linkejian123/Antique-Music-Box/CAD/ecc88/Renderings/ecc88_003.JPG

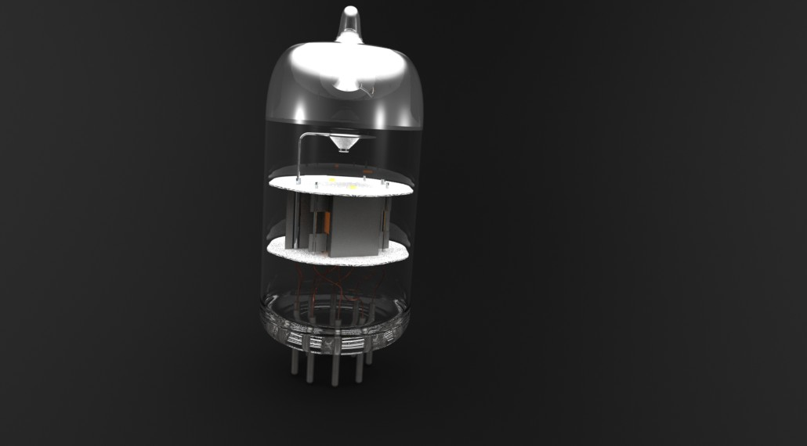
CAD/ecc88/Renderings/ecc88_003.JPG
