linkejian123/Antique-Music-Box/CAD/ecc88/Renderings/ECC88_in_Noval.JPG

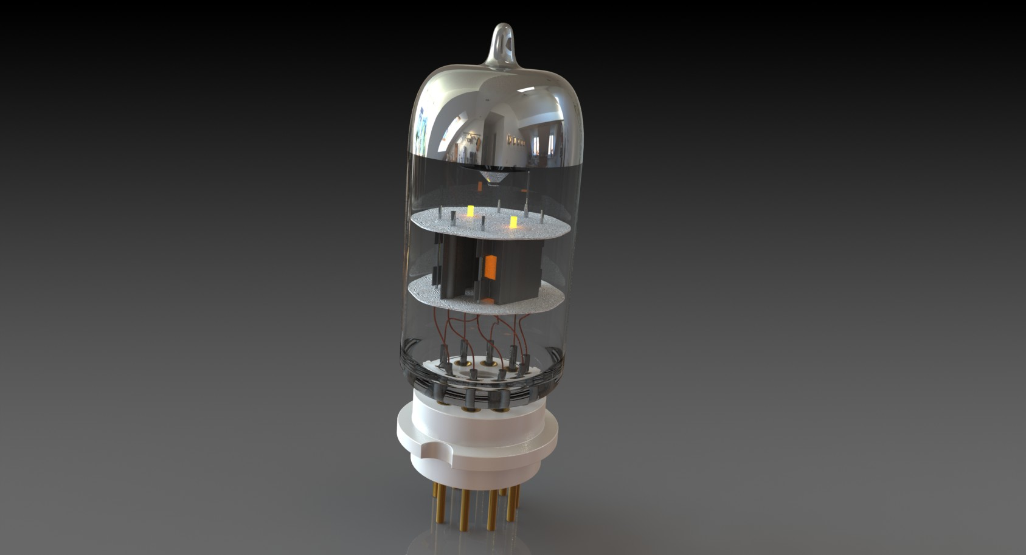
CAD/ecc88/Renderings/ECC88_in_Noval.JPG
