linkejian123/Antique-Music-Box/CAD/iv-17/render2.png

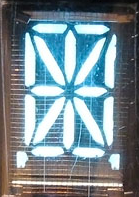
CAD/iv-17/render2.png
