linkejian123/Antique-Music-Box/CAD/iv-17/render.png

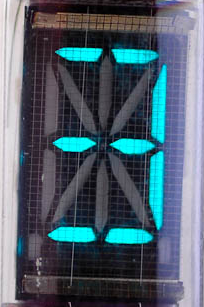
CAD/iv-17/render.png
