linkejian123/Antique-Music-Box/CAD/little-knob.snapshot.2/Renderings/2.jpg

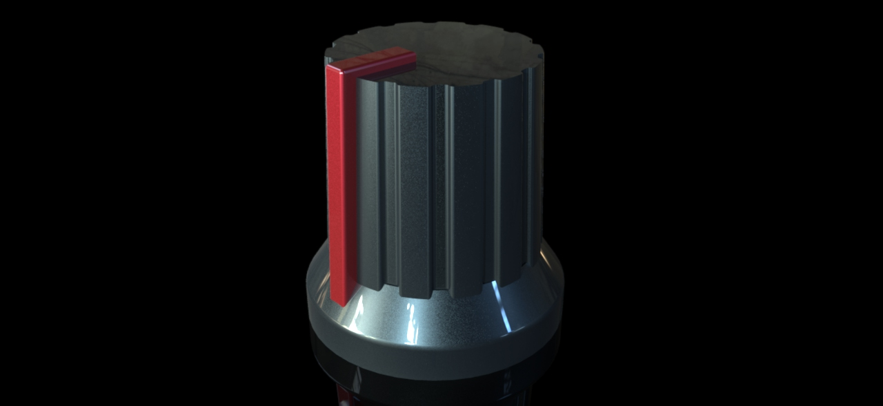
CAD/little-knob.snapshot.2/Renderings/2.jpg
