linkejian123/Antique-Music-Box/CAD/little-knob.snapshot.2/Renderings/345.JPG

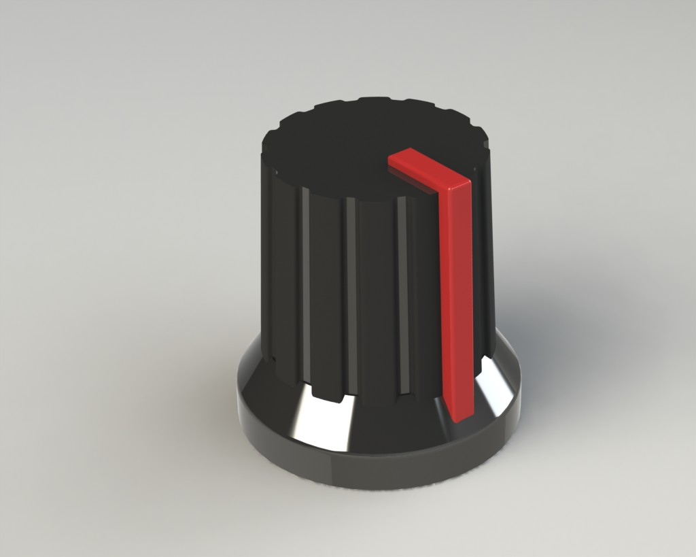
CAD/little-knob.snapshot.2/Renderings/345.JPG
