linkejian123/Antique-Music-Box/OBJ477/Gerbers/ap.JPG

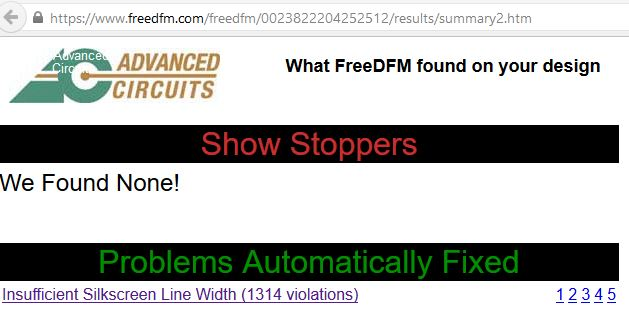
OBJ477/Gerbers/ap.JPG
