linkejian123/Antique-Music-Box/OBJ477/Gerbers/iv25.JPG

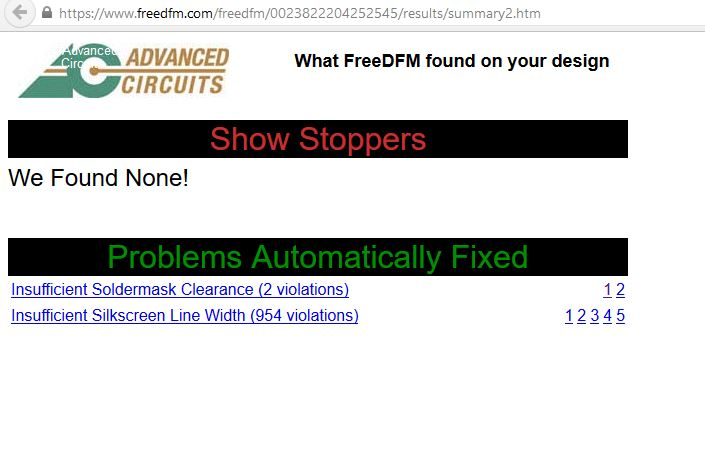
OBJ477/Gerbers/iv25.JPG
