linkejian123/Antique-Music-Box/CAD/little-knob.snapshot.2/myknob.IGS

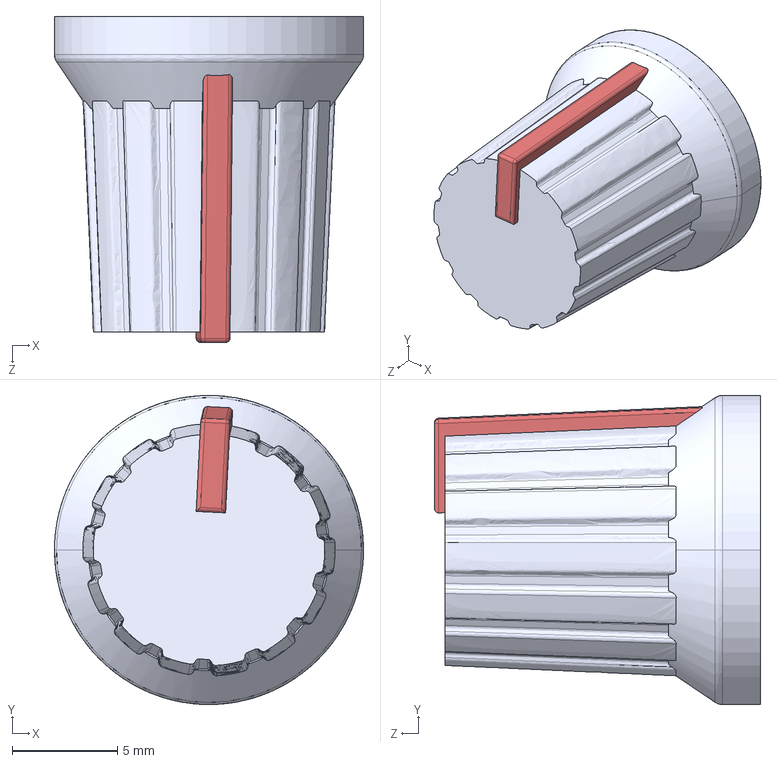
[picture p29: CAD file, 2017-10-23]
CAD/little-knob.snapshot.2/myknob.IGS
14.7 x 14.7 x 15.5 mm
