linkejian123/Antique-Music-Box/CAD/msc/12ax7/sheild.sldprt

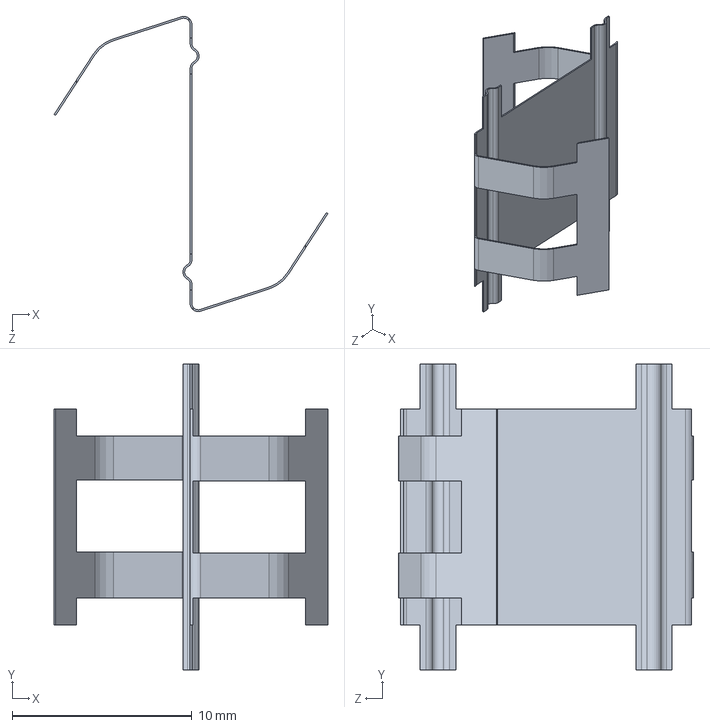
[picture p30: CAD file, 2017-10-23]
CAD/msc/12ax7/sheild.sldprt
15.2 x 17.0 x 16.4 mm
