linkejian123/Antique-Music-Box/CAD/msc/845/845 - cathode.SLDPRT

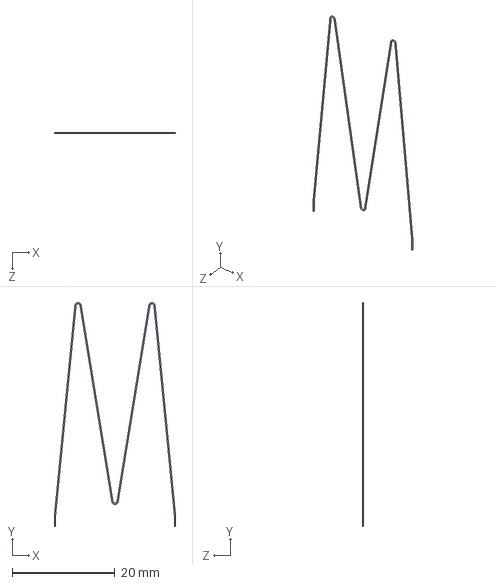
[picture p31: CAD file, 2017-10-23]
CAD/msc/845/845 - cathode.SLDPRT
23.6 x 43.6 x 0.25 mm
