linkejian123/Antique-Music-Box/CAD/ecc88/ecc88/ecc88_balon.SLDPRT

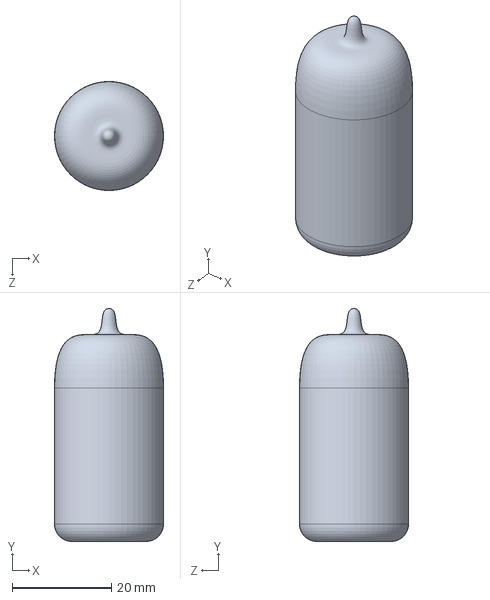
[picture p32: CAD file, 2017-10-23]
CAD/ecc88/ecc88/ecc88_balon.SLDPRT
22.0 x 47.0 x 22.0 mm
