linkejian123/Antique-Music-Box/CAD/el84  sub 6z4/el84 - spring thing.SLDPRT

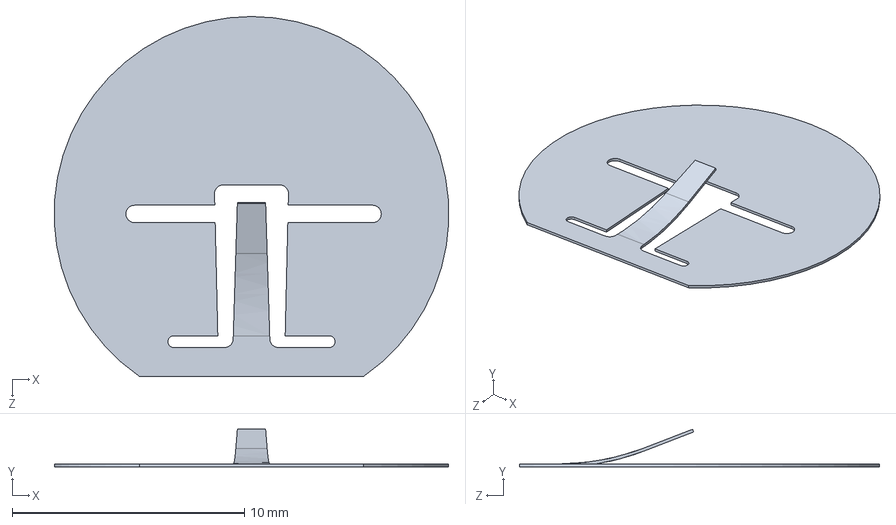
[picture p33: CAD file, 2017-10-23]
CAD/el84 sub 6z4/el84 - spring thing.SLDPRT
17.0 x 1.62 x 15.5 mm
