linkejian123/Antique-Music-Box/CAD/etd39-transformer-horizontal-1.snapshot.6/ETD39 Horizontal/7. Mounting bracket.SLDPRT

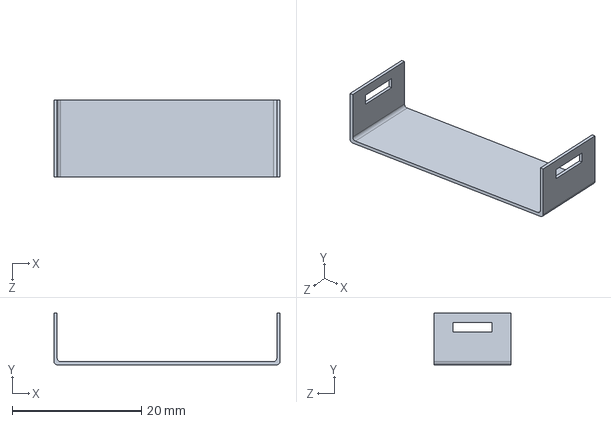
[picture p34: CAD file, 2017-10-23]
CAD/etd39-transformer-horizontal-1.snapshot.6/ETD39 Horizontal/7. Mounting bracket.SLDPRT
35.0 x 8.00 x 12.0 mm
