linkejian123/Antique-Music-Box/CAD/iv-17/tube_leads.SLDPRT

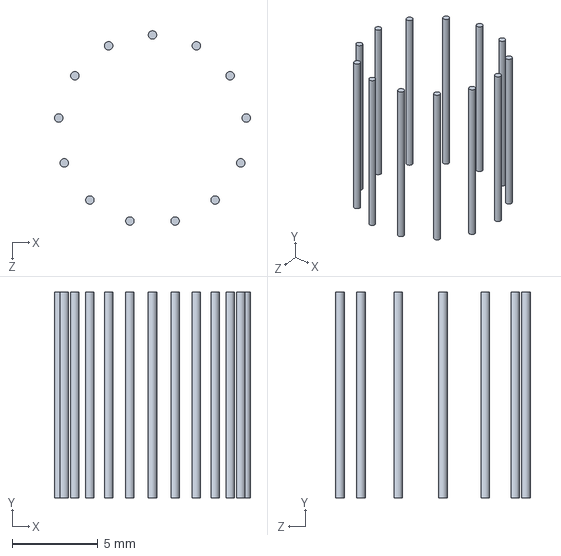
[picture p35: CAD file, 2017-10-23]
CAD/iv-17/tube_leads.SLDPRT
11.4 x 12.0 x 11.3 mm
