linkejian123/Antique-Music-Box/CAD/iv-25/insole.SLDPRT

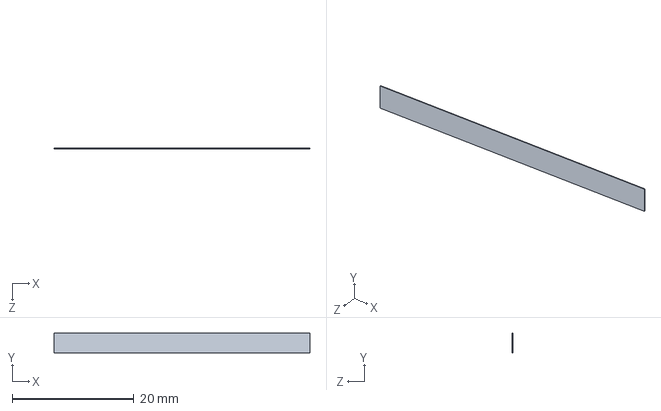
[picture p36: CAD file, 2017-10-23]
CAD/iv-25/insole.SLDPRT
42.0 x 3.20 x 0.1 mm
