linkejian123/Antique-Music-Box/CAD/msc/12ax7/cathode_end.sldprt

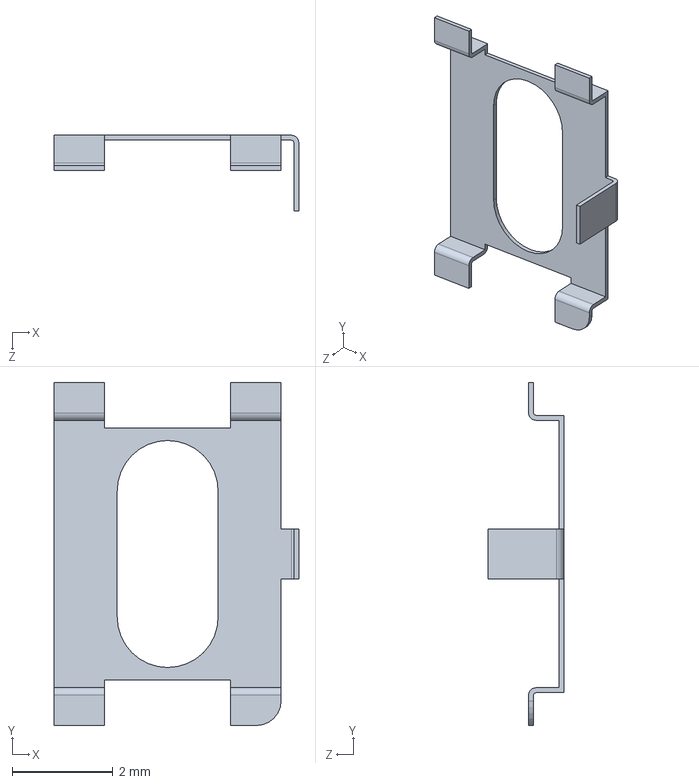
[picture p37: CAD file, 2017-10-23]
CAD/msc/12ax7/cathode_end.sldprt
4.85 x 6.80 x 1.50 mm
