linkejian123/Antique-Music-Box/CAD/ecc88/ecc88/ecc88_insulator.SLDPRT

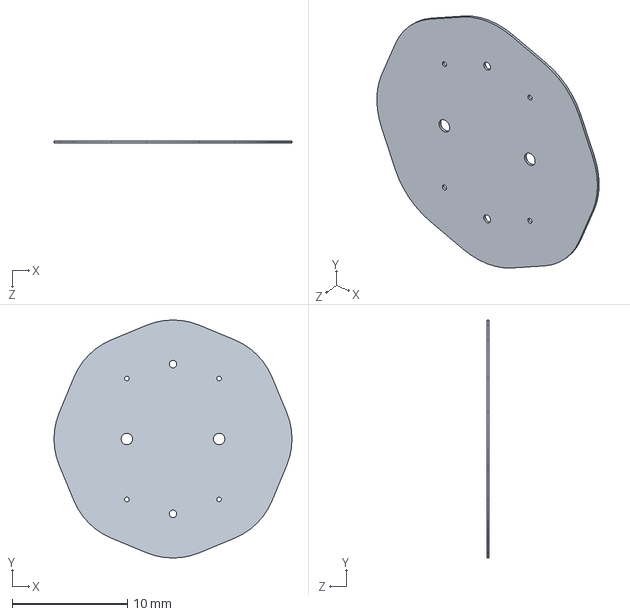
[picture p39: CAD file, 2017-10-23]
CAD/ecc88/ecc88/ecc88_insulator.SLDPRT
20.7 x 20.7 x 0.2 mm
