linkejian123/Antique-Music-Box/CAD/el84  sub 6z4/screen connector.SLDPRT

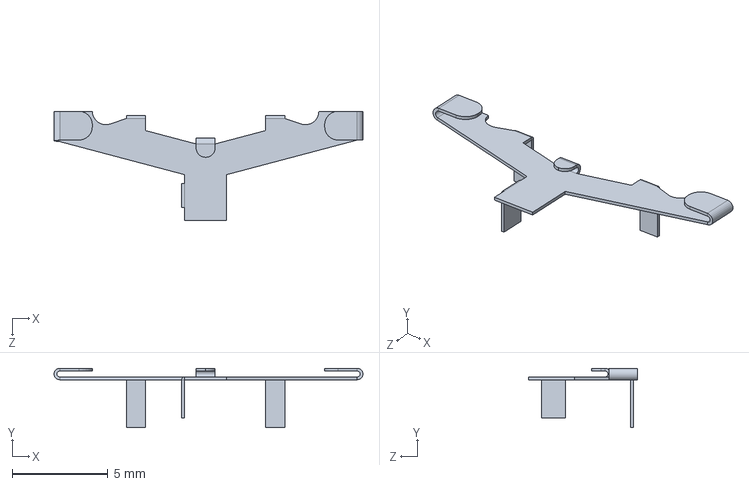
[picture p40: CAD file, 2017-10-23]
CAD/el84 sub 6z4/screen connector.SLDPRT
16.1 x 3.10 x 5.70 mm
