linkejian123/Antique-Music-Box/CAD/em84/tube_body2.SLDPRT

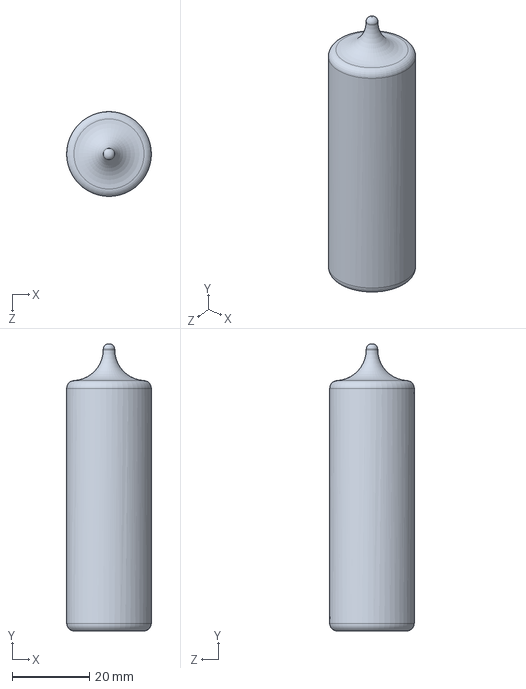
[picture p41: CAD file, 2017-10-23]
CAD/em84/tube_body2.SLDPRT
22.0 x 74.5 x 22.0 mm
