linkejian123/Antique-Music-Box/CAD/iv-25/iv-25.SLDPRT

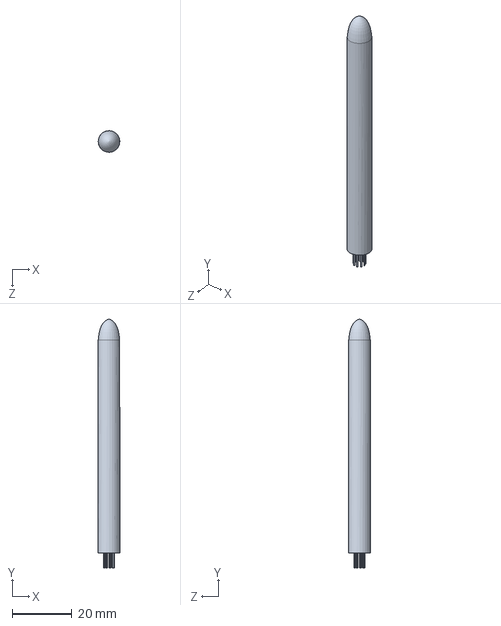
[picture p42: CAD file, 2017-10-23]
CAD/iv-25/iv-25.SLDPRT
7.20 x 83.0 x 7.20 mm
