linkejian123/Antique-Music-Box/CAD/msc/12ax7/grid wire.sldprt

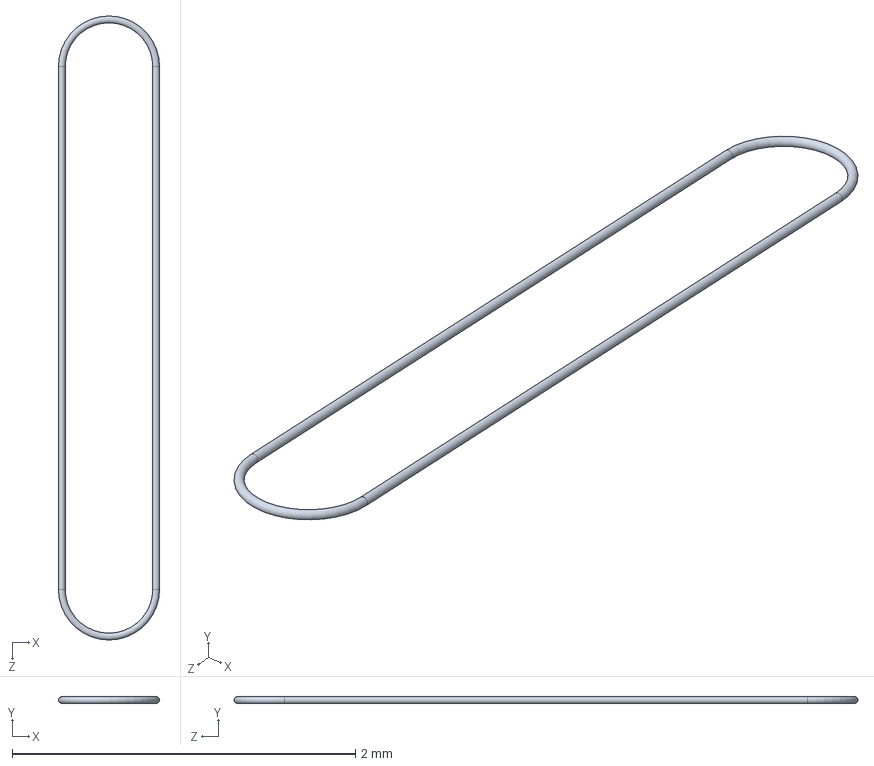
[picture p43: CAD file, 2017-10-23]
CAD/msc/12ax7/grid wire.sldprt
0.59 x 0.04 x 3.64 mm
