linkejian123/Antique-Music-Box/CAD/msc/845/845 - heater long lead.SLDPRT

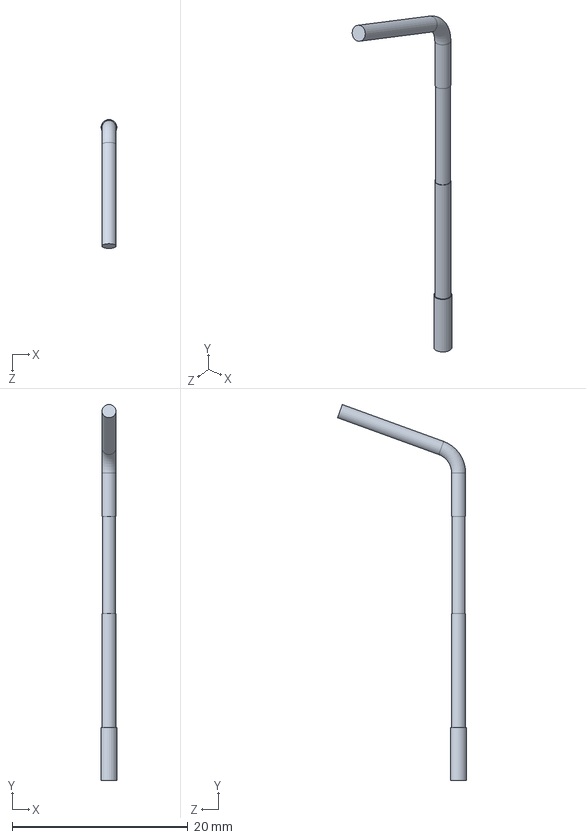
[picture p44: CAD file, 2017-10-23]
CAD/msc/845/845 - heater long lead.SLDPRT
1.80 x 42.8 x 14.7 mm
