linkejian123/Antique-Music-Box/CAD/el84  sub 6z4/el84 lower mica.SLDPRT

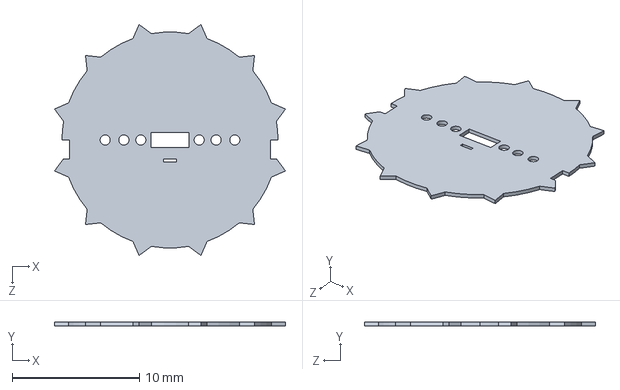
[picture p45: CAD file, 2017-10-23]
CAD/el84 sub 6z4/el84 lower mica.SLDPRT
18.2 x 0.3 x 18.2 mm
