linkejian123/Antique-Music-Box/CAD/etd39-transformer-horizontal-1.snapshot.6/ETD39 Horizontal/3. Case (Pin end)1.SLDPRT

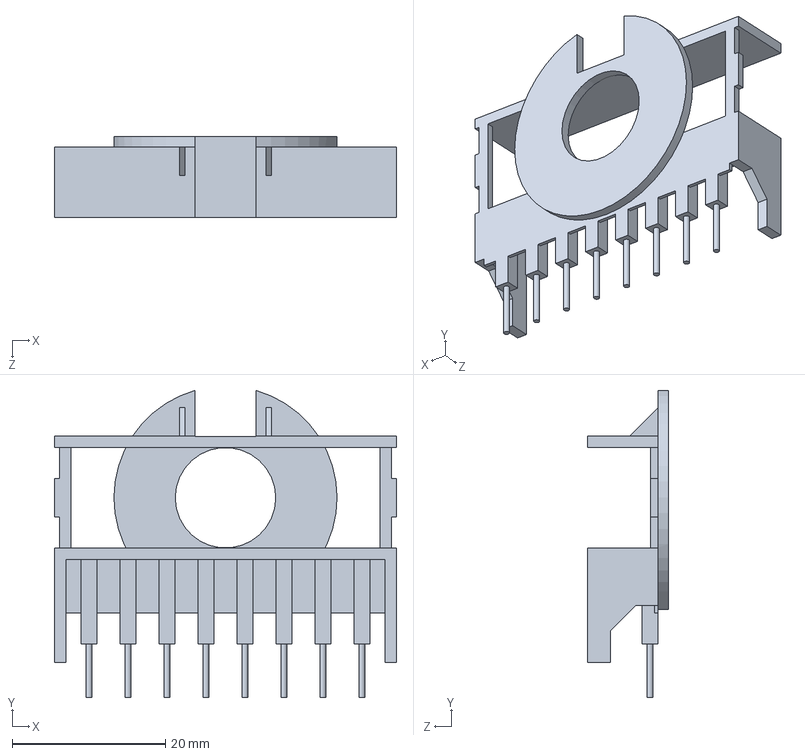
[picture p46: CAD file, 2017-10-23]
CAD/etd39-transformer-horizontal-1.snapshot.6/ETD39 Horizontal/3. Case (Pin end)1.SLDPRT
44.6 x 40.0 x 10.6 mm
