linkejian123/Antique-Music-Box/CAD/iv-17/flip.SLDPRT

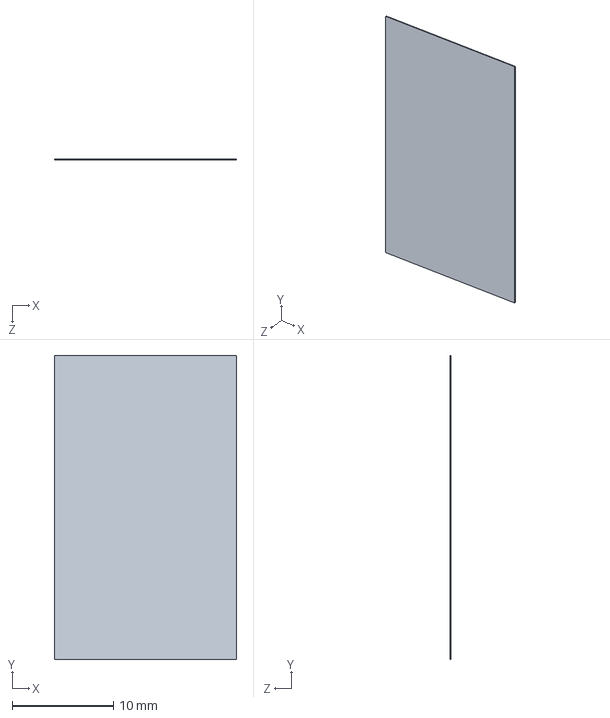
[picture p47: CAD file, 2017-10-23]
CAD/iv-17/flip.SLDPRT
18.0 x 30.0 x 0.1 mm
