linkejian123/Antique-Music-Box/CAD/msc/845/845 - inner heater to pin.SLDPRT

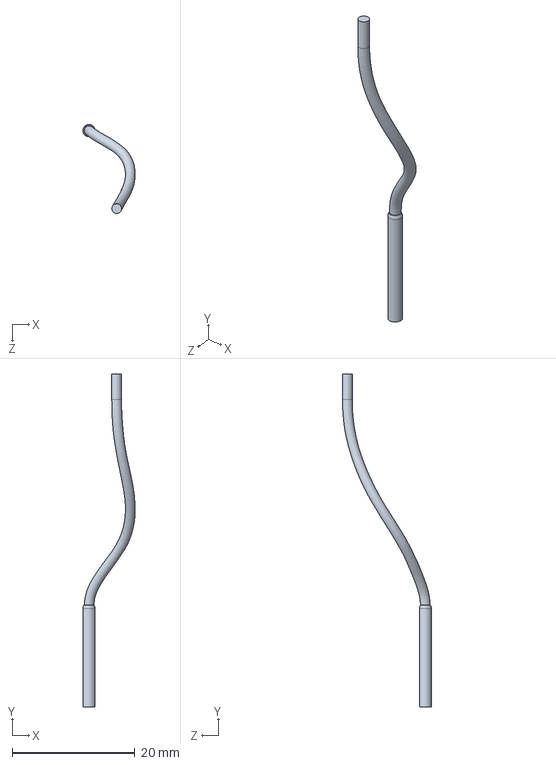
[picture p48: CAD file, 2017-10-23]
CAD/msc/845/845 - inner heater to pin.SLDPRT
8.51 x 54.2 x 14.5 mm
