linkejian123/Antique-Music-Box/CAD/ecc88/ecc88/ecc88_heater.SLDPRT

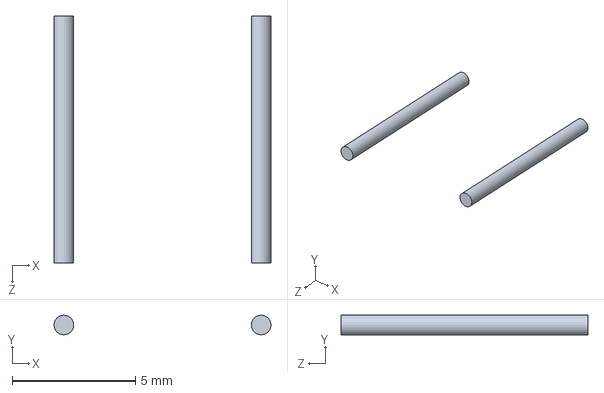
[picture p49: CAD file, 2017-10-23]
CAD/ecc88/ecc88/ecc88_heater.SLDPRT
8.80 x 0.8 x 10.0 mm
