linkejian123/Antique-Music-Box/CAD/el84  sub 6z4/el84 plate.SLDPRT

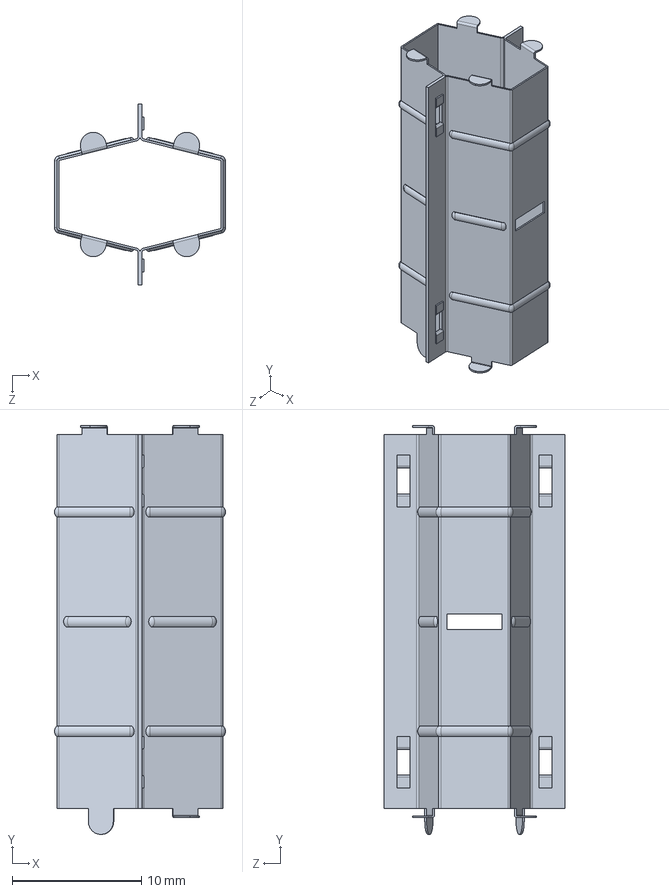
[picture p50: CAD file, 2017-10-23]
CAD/el84 sub 6z4/el84 plate.SLDPRT
13.3 x 31.7 x 14.0 mm
