linkejian123/Antique-Music-Box/CAD/em84/tiepian.SLDPRT

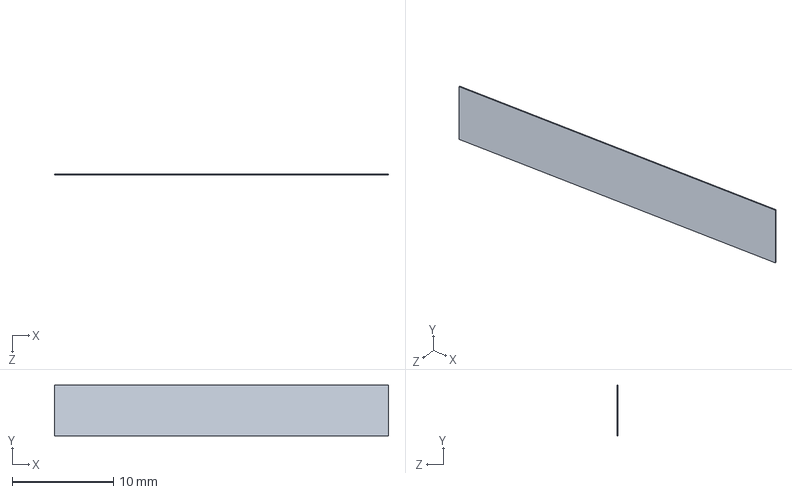
[picture p51: CAD file, 2017-10-23]
CAD/em84/tiepian.SLDPRT
33.0 x 5.00 x 0.1 mm
