linkejian123/Antique-Music-Box/CAD/etd39-transformer-horizontal-1.snapshot.6/ETD39 Horizontal/5. Coil.SLDPRT

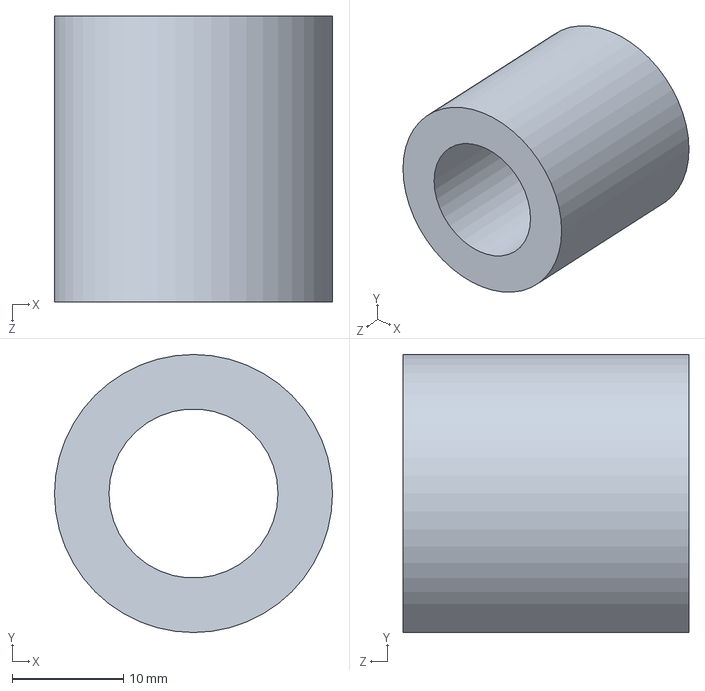
[picture p52: CAD file, 2017-10-23]
CAD/etd39-transformer-horizontal-1.snapshot.6/ETD39 Horizontal/5. Coil.SLDPRT
25.0 x 25.0 x 25.7 mm
