linkejian123/Antique-Music-Box/CAD/iv-17/tube_body.SLDPRT

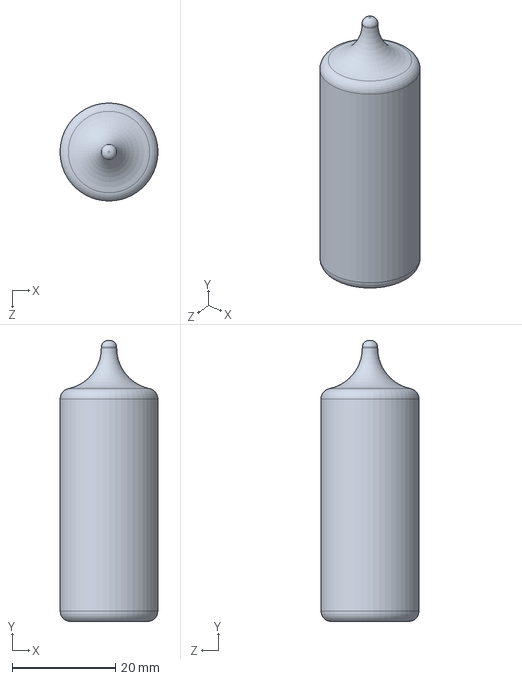
[picture p53: CAD file, 2017-10-23]
CAD/iv-17/tube_body.SLDPRT
19.0 x 54.5 x 19.0 mm
