linkejian123/Antique-Music-Box/CAD/msc/12ax7/12ax7_glass.sldprt

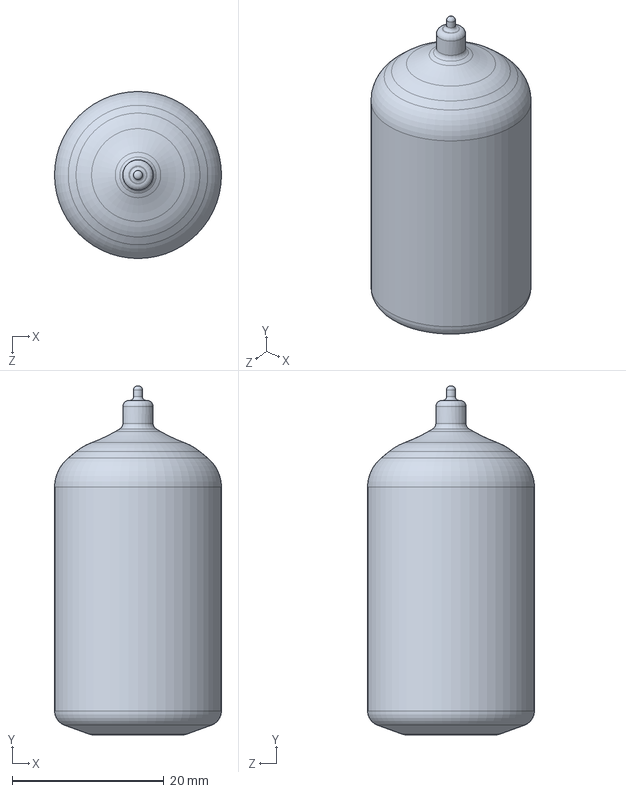
[picture p54: CAD file, 2017-10-23]
CAD/msc/12ax7/12ax7_glass.sldprt
22.0 x 46.0 x 22.0 mm
