linkejian123/Antique-Music-Box/CAD/msc/845/845 - aluminium base.SLDPRT

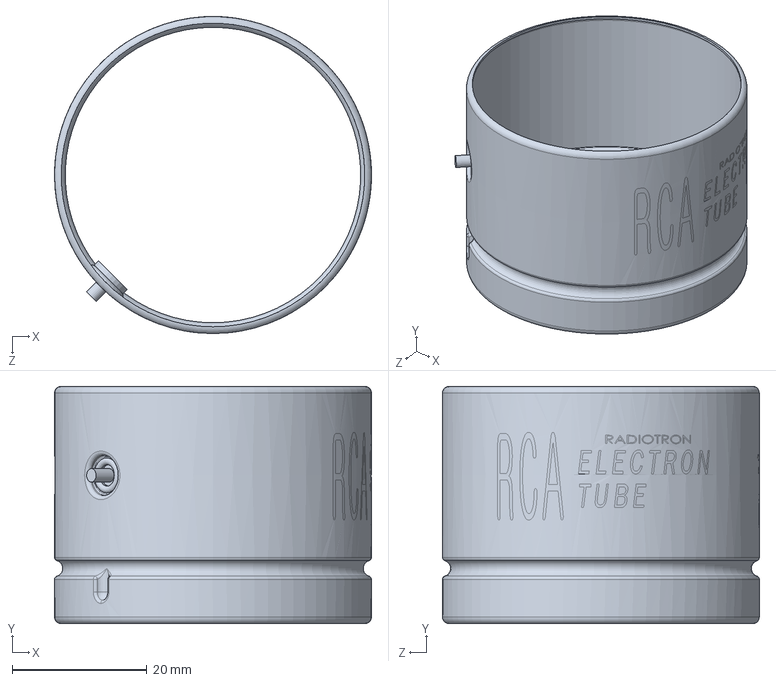
[picture p55: CAD file, 2017-10-23]
CAD/msc/845/845 - aluminium base.SLDPRT
47.0 x 35.2 x 47.0 mm
