linkejian123/Antique-Music-Box/CAD/el84  sub 6z4/el84 - top shield.SLDPRT

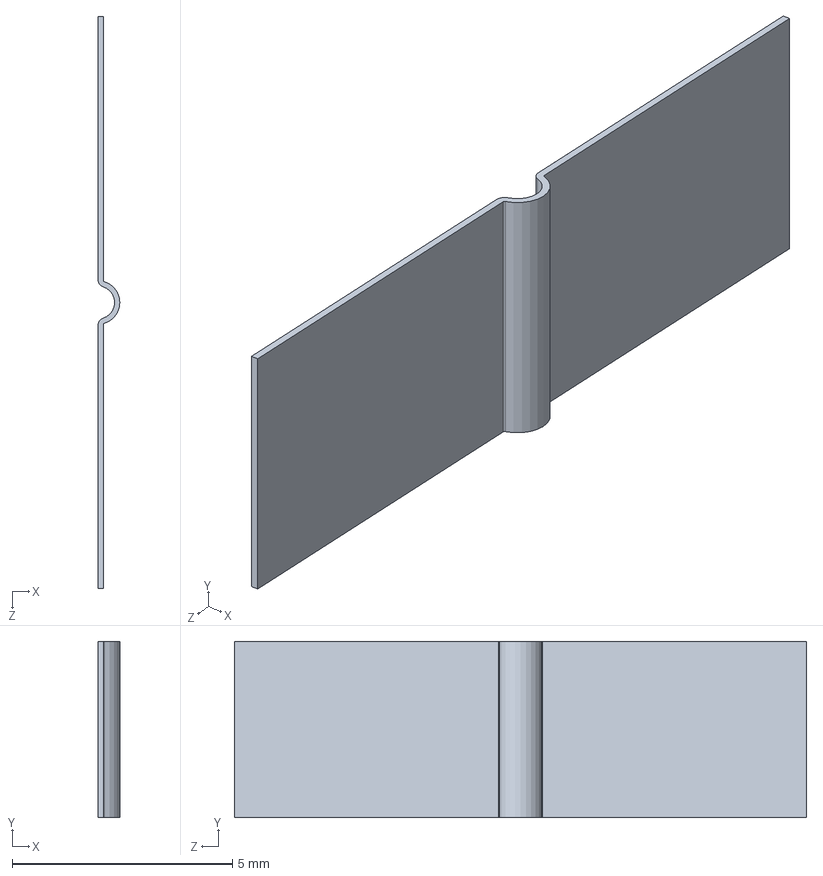
[picture p56: CAD file, 2017-10-23]
CAD/el84 sub 6z4/el84 - top shield.SLDPRT
0.495 x 4.00 x 13.0 mm
