linkejian123/Antique-Music-Box/CAD/etd39-transformer-horizontal-1.snapshot.6/ETD39 Horizontal/2. Case (center).SLDPRT

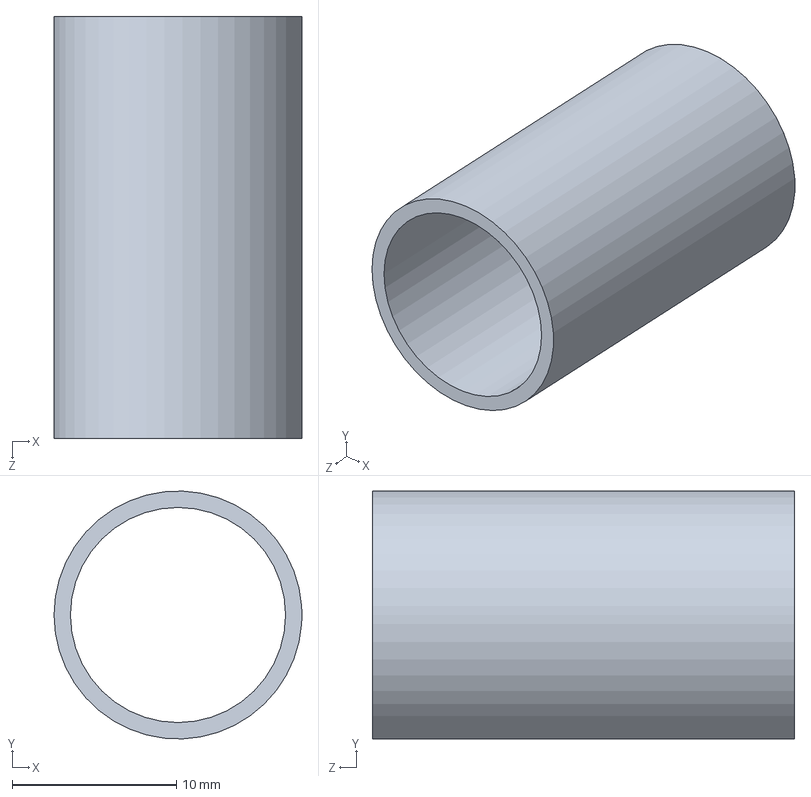
[picture p57: CAD file, 2017-10-23]
CAD/etd39-transformer-horizontal-1.snapshot.6/ETD39 Horizontal/2. Case (center).SLDPRT
15.1 x 15.1 x 25.7 mm
