linkejian123/Antique-Music-Box/CAD/msc/12ax7/top_mica.sldprt

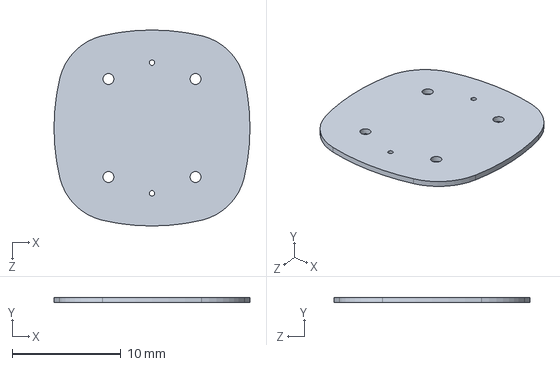
[picture p58: CAD file, 2017-10-23]
CAD/msc/12ax7/top_mica.sldprt
18.0 x 0.5 x 18.0 mm
