linkejian123/Antique-Music-Box/CAD/msc/845/845 - grid lead.SLDPRT

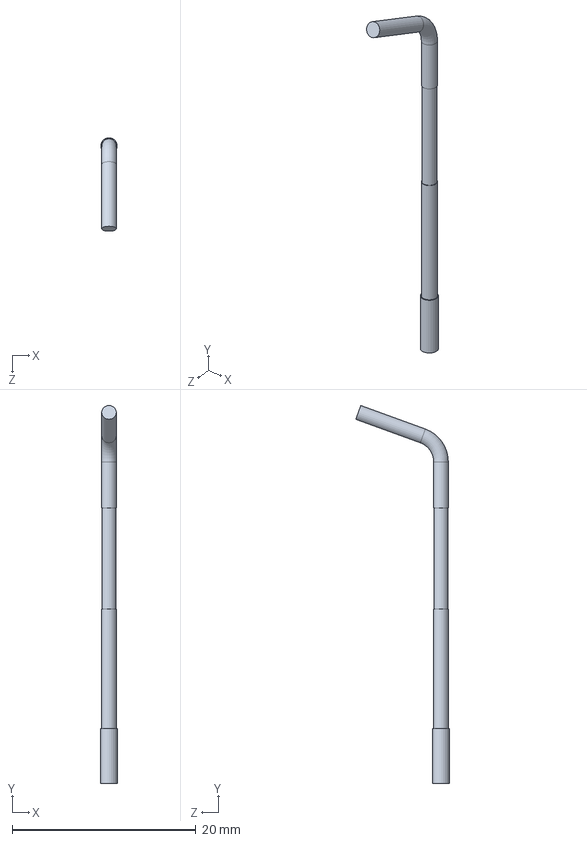
[picture p59: CAD file, 2017-10-23]
CAD/msc/845/845 - grid lead.SLDPRT
1.80 x 41.1 x 10.2 mm
