linkejian123/Antique-Music-Box/CAD/el84  sub 6z4/EL84 HEATER LEADS.SLDPRT

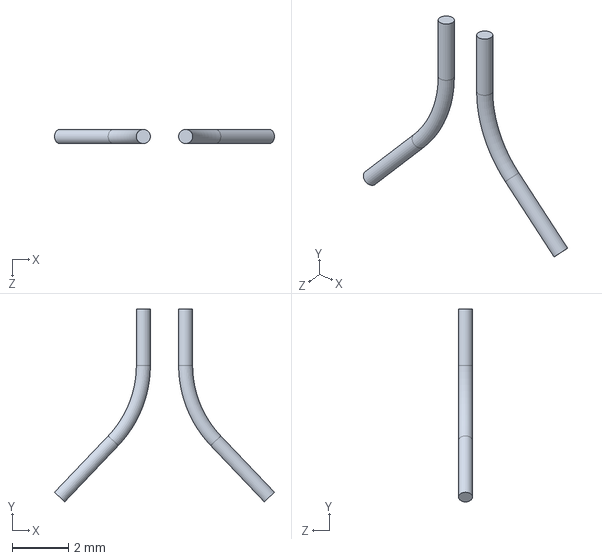
[picture p60: CAD file, 2017-10-23]
CAD/el84 sub 6z4/EL84 HEATER LEADS.SLDPRT
7.81 x 6.84 x 0.5 mm
