linkejian123/Antique-Music-Box/CAD/msc/12ax7/support_pin.sldprt

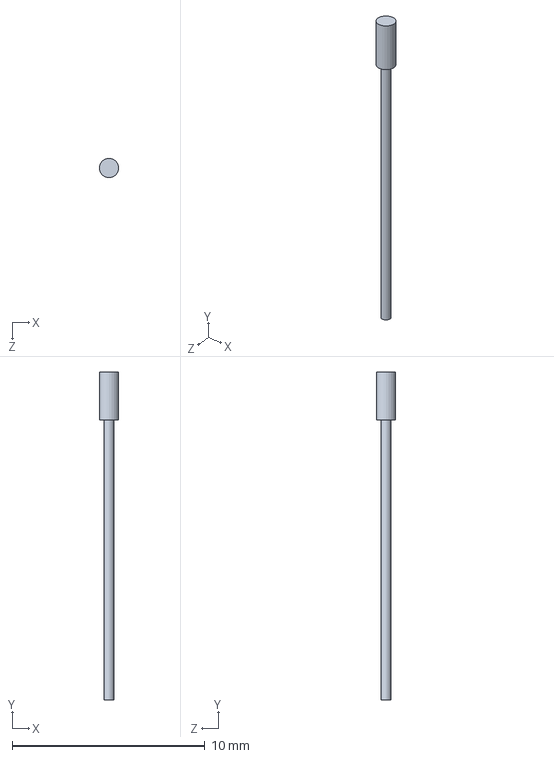
[picture p61: CAD file, 2017-10-23]
CAD/msc/12ax7/support_pin.sldprt
1.00 x 17.0 x 1.00 mm
