linkejian123/Antique-Music-Box/CAD/el84  sub 6z4/el84 pins.SLDPRT

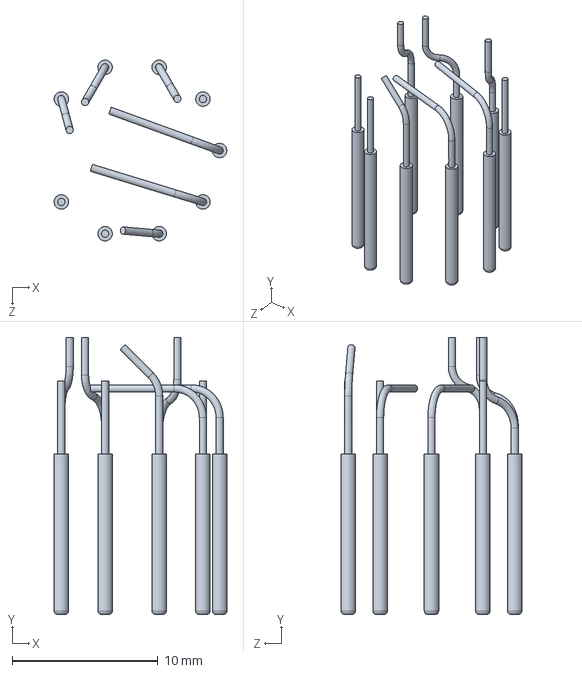
[picture p62: CAD file, 2017-10-23]
CAD/el84 sub 6z4/el84 pins.SLDPRT
11.9 x 19.0 x 12.4 mm
