linkejian123/Antique-Music-Box/CAD/msc/845/845 - left hand cathode anchor.SLDPRT

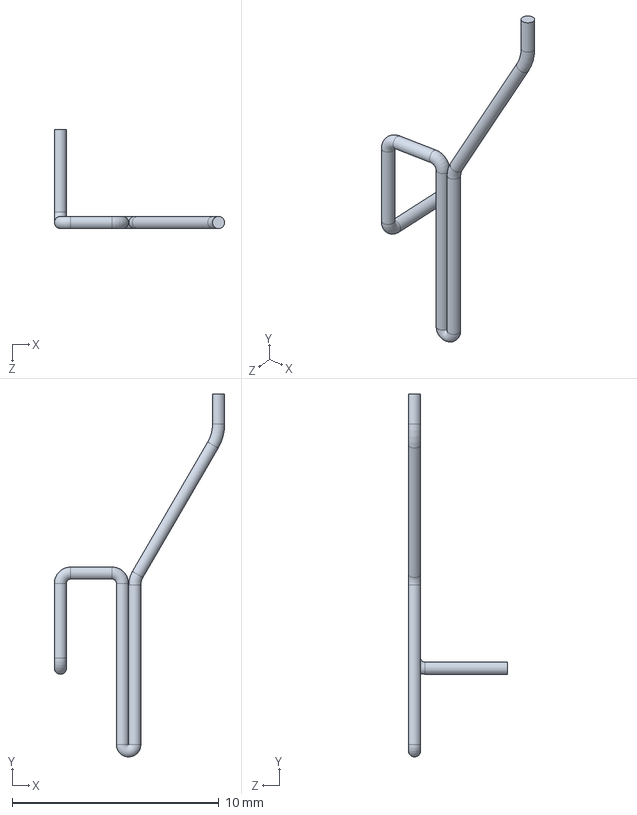
[picture p63: CAD file, 2017-10-23]
CAD/msc/845/845 - left hand cathode anchor.SLDPRT
8.24 x 17.6 x 4.79 mm
