linkejian123/Antique-Music-Box/CAD/el84  sub 6z4/el34 suppressor.SLDPRT

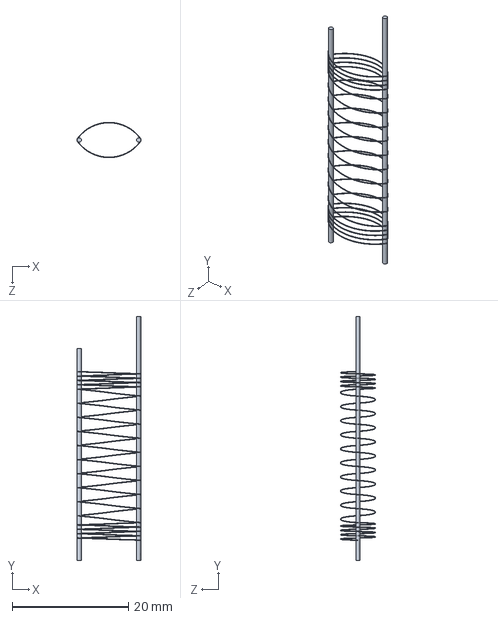
[picture p64: CAD file, 2017-10-23]
CAD/el84 sub 6z4/el34 suppressor.SLDPRT
11.1 x 42.0 x 6.10 mm
