linkejian123/Antique-Music-Box/CAD/msc/12ax7/mica3_lower.sldprt

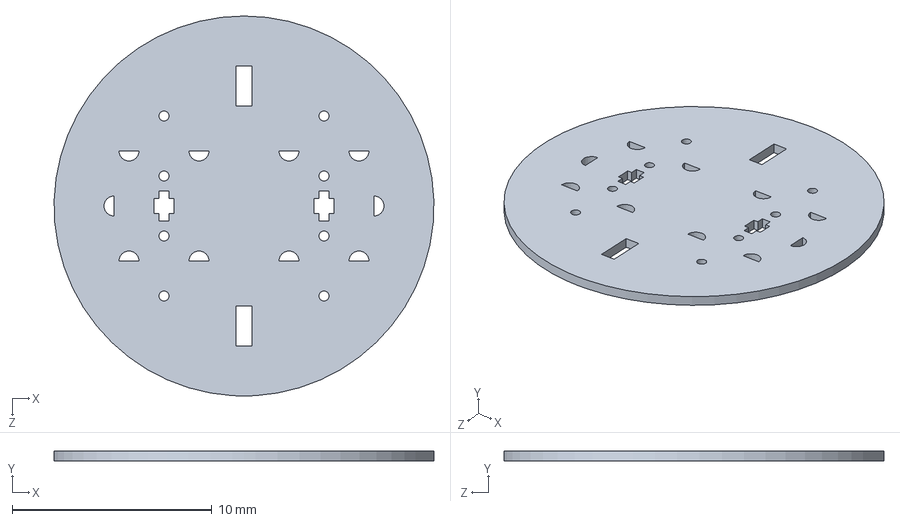
[picture p65: CAD file, 2017-10-23]
CAD/msc/12ax7/mica3_lower.sldprt
19.0 x 0.5 x 19.0 mm
