linkejian123/Antique-Music-Box/CAD/el84  sub 6z4/el84 glass.SLDPRT

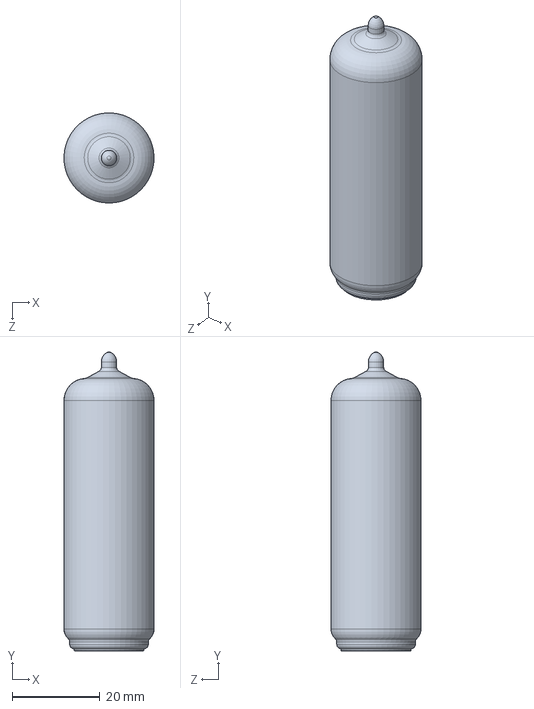
[picture p66: CAD file, 2017-10-23]
CAD/el84 sub 6z4/el84 glass.SLDPRT
20.5 x 68.0 x 20.5 mm
