linkejian123/Antique-Music-Box/CAD/msc/12ax7/pins.sldprt

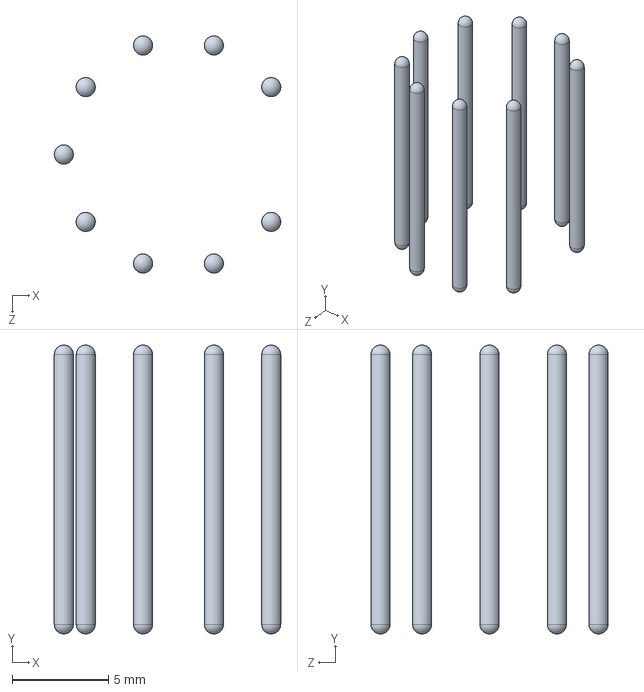
[picture p67: CAD file, 2017-10-23]
CAD/msc/12ax7/pins.sldprt
11.8 x 15.0 x 12.3 mm
