linkejian123/Antique-Music-Box/CAD/msc/845/845 - anode.SLDPRT

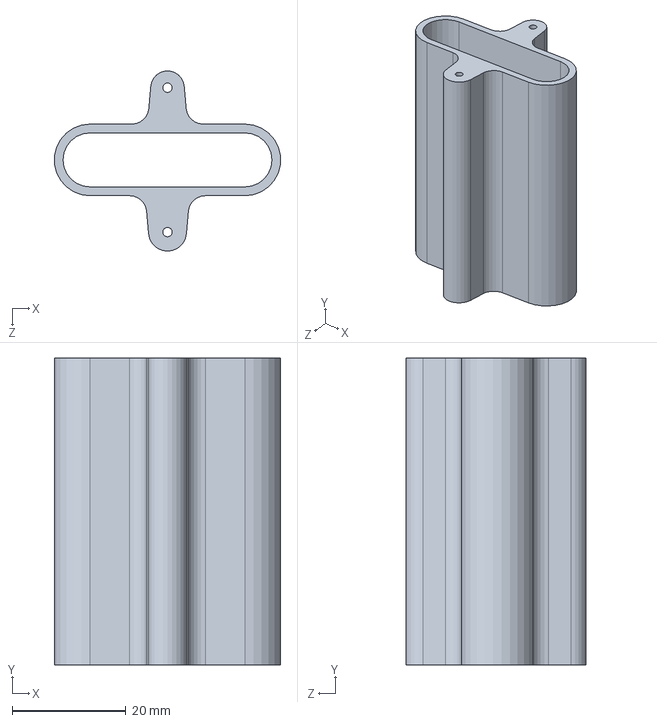
[picture p68: CAD file, 2017-10-23]
CAD/msc/845/845 - anode.SLDPRT
39.8 x 54.0 x 31.7 mm
