linkejian123/Antique-Music-Box/CAD/el84  sub 6z4/el84 - boat.SLDPRT

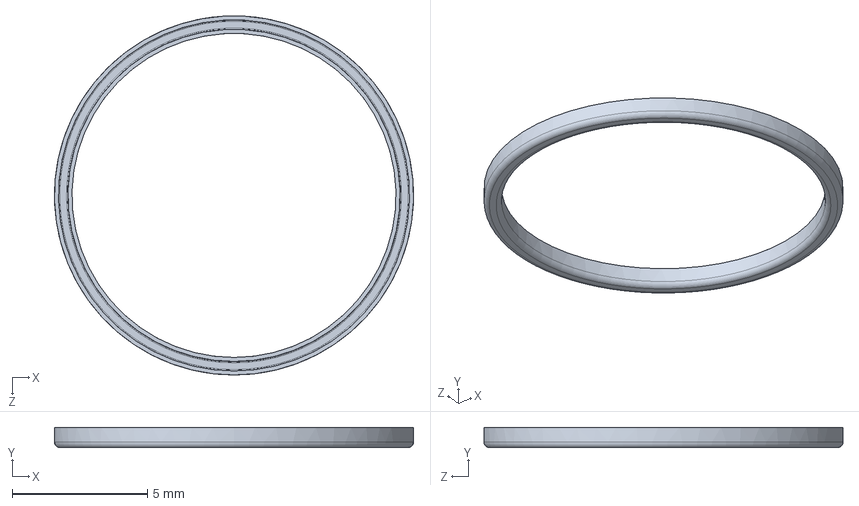
[picture p69: CAD file, 2017-10-23]
CAD/el84 sub 6z4/el84 - boat.SLDPRT
13.3 x 0.75 x 13.3 mm
