linkejian123/Antique-Music-Box/CAD/msc/12ax7/cathode.sldprt

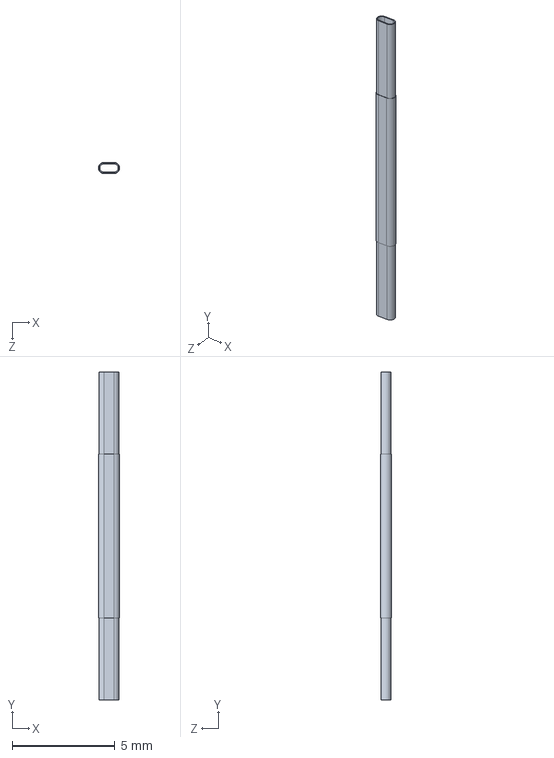
[picture p70: CAD file, 2017-10-23]
CAD/msc/12ax7/cathode.sldprt
1.04 x 16.0 x 0.54 mm
