linkejian123/Antique-Music-Box/CAD/msc/845/845 - centre cathode anchor.SLDPRT

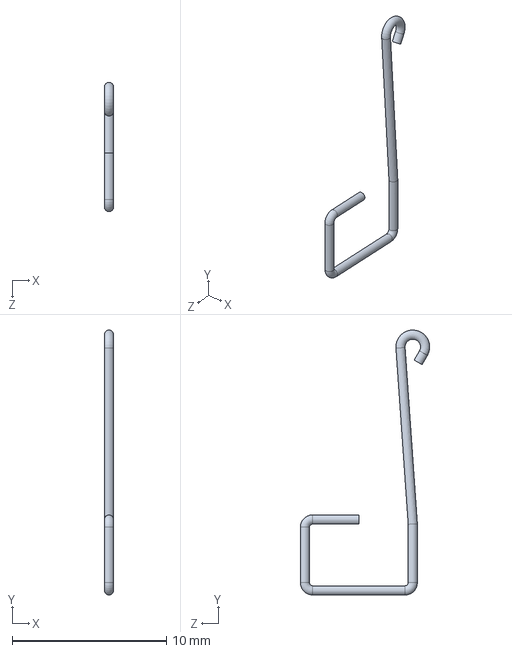
[picture p71: CAD file, 2017-10-23]
CAD/msc/845/845 - centre cathode anchor.SLDPRT
0.6 x 17.2 x 8.39 mm
