linkejian123/Antique-Music-Box/CAD/msc/12ax7/grid.sldprt

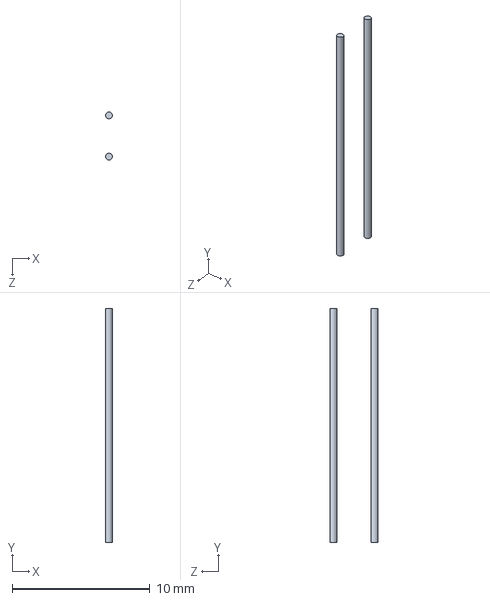
[picture p72: CAD file, 2017-10-23]
CAD/msc/12ax7/grid.sldprt
0.5 x 17.0 x 3.50 mm
