linkejian123/Antique-Music-Box/CAD/msc/12ax7/boat.sldprt

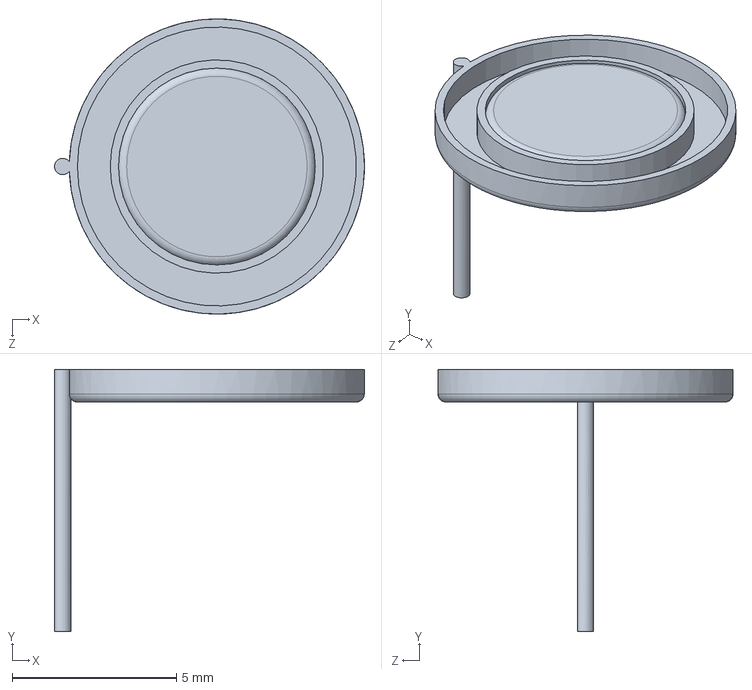
[picture p73: CAD file, 2017-10-23]
CAD/msc/12ax7/boat.sldprt
9.45 x 8.00 x 9.00 mm
