linkejian123/Antique-Music-Box/CAD/msc/845/845 - bottom ceramic.SLDPRT

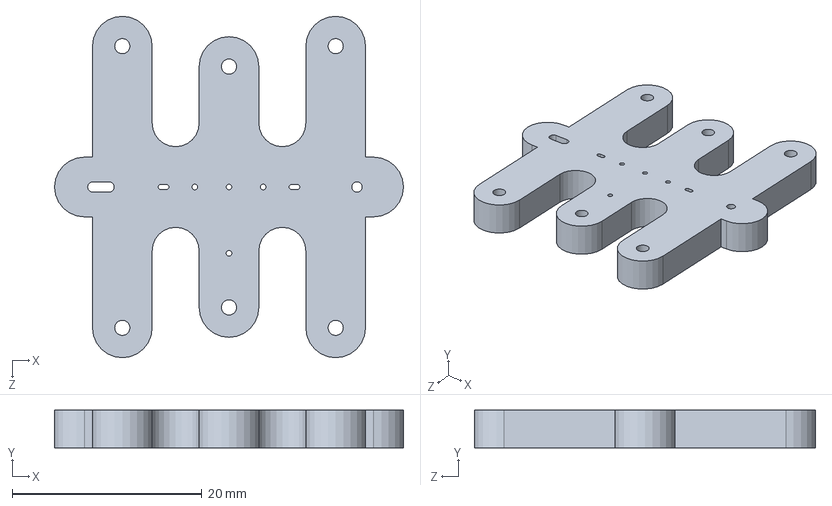
[picture p74: CAD file, 2017-10-23]
CAD/msc/845/845 - bottom ceramic.SLDPRT
36.8 x 4.00 x 36.0 mm
