linkejian123/Antique-Music-Box/CAD/msc/12ax7/mica2.sldprt

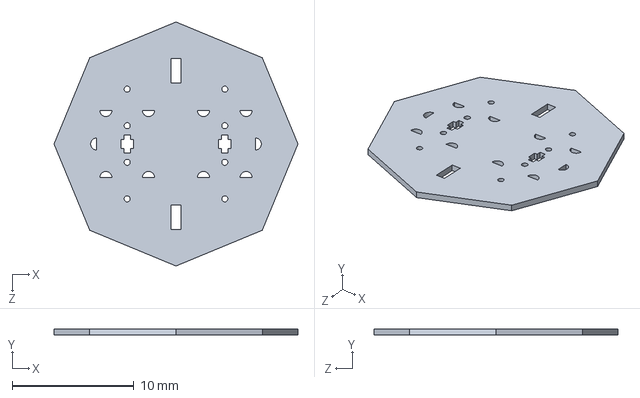
[picture p75: CAD file, 2017-10-23]
CAD/msc/12ax7/mica2.sldprt
20.0 x 0.5 x 20.0 mm
