linkejian123/Antique-Music-Box/CAD/msc/845/845 - base ceramic.SLDPRT

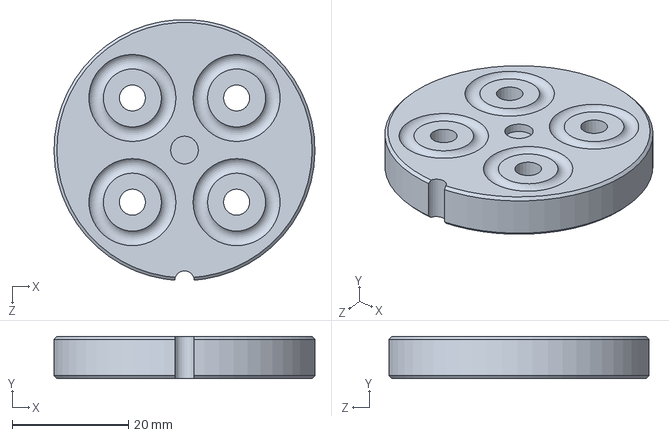
[picture p76: CAD file, 2017-10-23]
CAD/msc/845/845 - base ceramic.SLDPRT
45.0 x 7.25 x 44.9 mm
