linkejian123/Antique-Music-Box/CAD/msc/12ax7/anode.sldprt

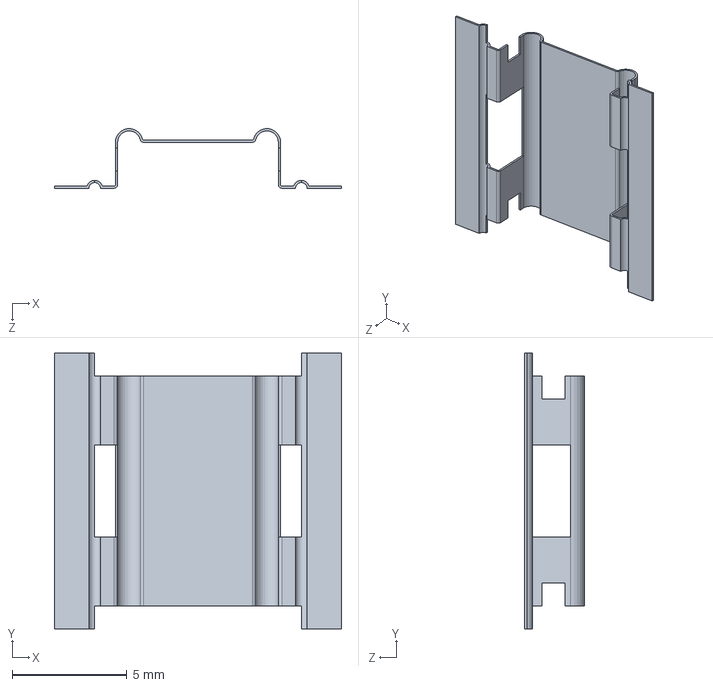
[picture p77: CAD file, 2017-10-23]
CAD/msc/12ax7/anode.sldprt
12.5 x 12.0 x 2.60 mm
