linkejian123/Antique-Music-Box/CAD/msc/845/845 - heater short lead.SLDPRT

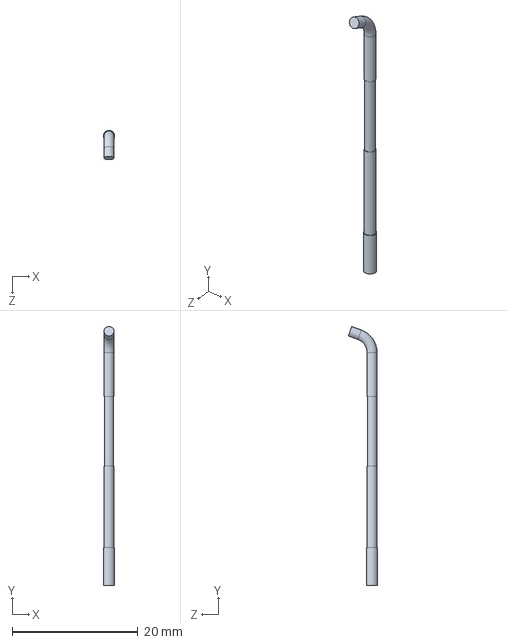
[picture p78: CAD file, 2017-10-23]
CAD/msc/845/845 - heater short lead.SLDPRT
1.80 x 41.1 x 4.67 mm
