linkejian123/Antique-Music-Box/CAD/msc/845/845 - boat frame.SLDPRT

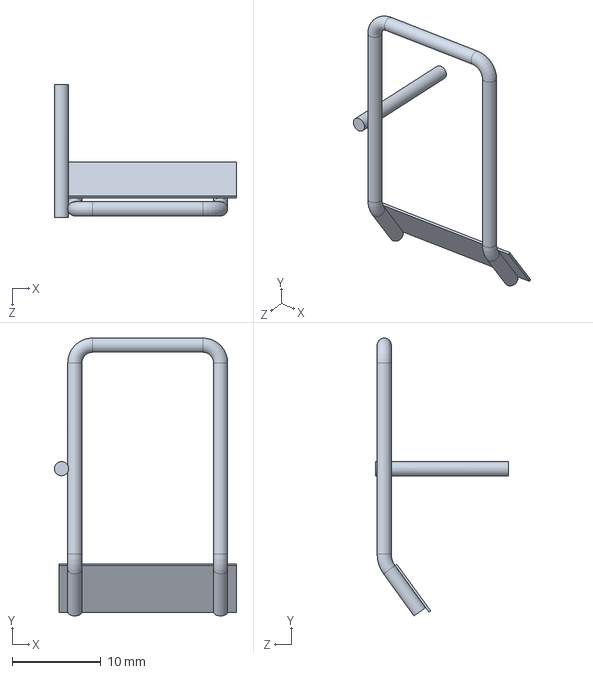
[picture p79: CAD file, 2017-10-23]
CAD/msc/845/845 - boat frame.SLDPRT
20.5 x 31.3 x 15.0 mm
