linkejian123/Antique-Music-Box/CAD/msc/845/845 - cathode spring.SLDPRT

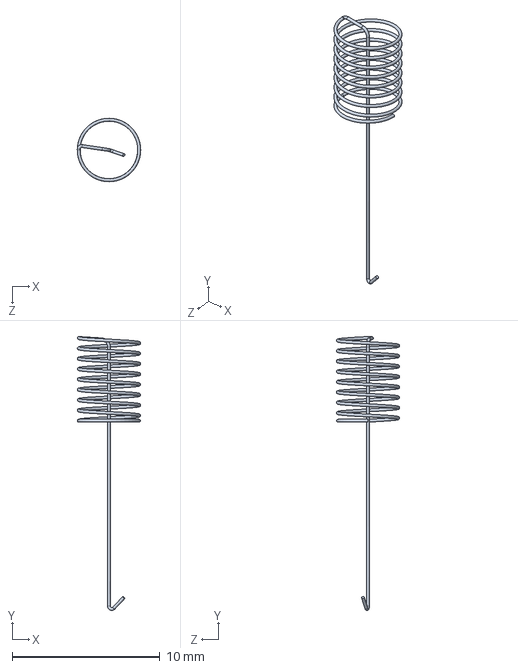
[picture p80: CAD file, 2017-10-23]
CAD/msc/845/845 - cathode spring.SLDPRT
4.30 x 18.5 x 4.30 mm
