linkejian123/Antique-Music-Box/CAD/msc/845/845 - grid wire.SLDPRT

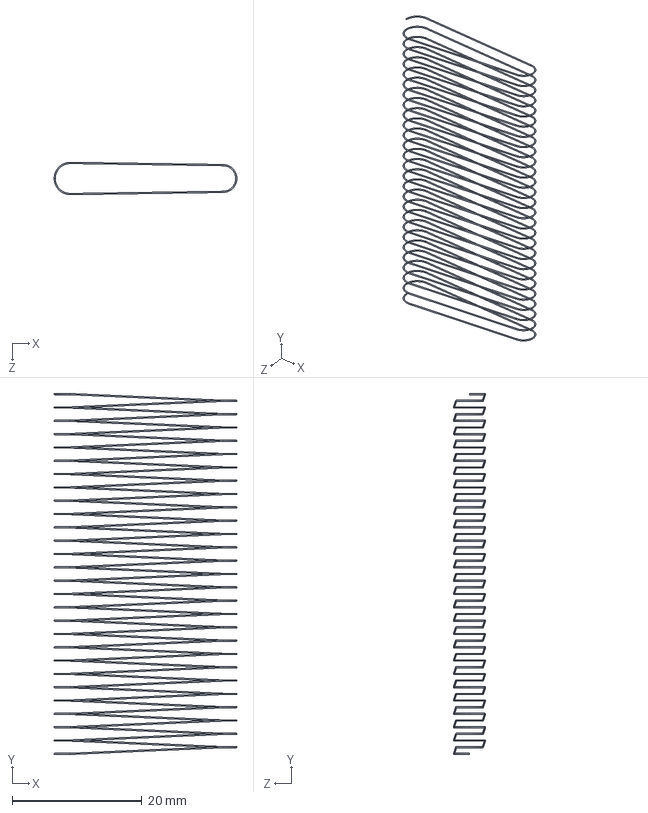
[picture p81: CAD file, 2017-10-23]
CAD/msc/845/845 - grid wire.SLDPRT
28.2 x 55.5 x 5.00 mm
