linkejian123/Antique-Music-Box/CAD/msc/845/845 - boat part 2.SLDPRT

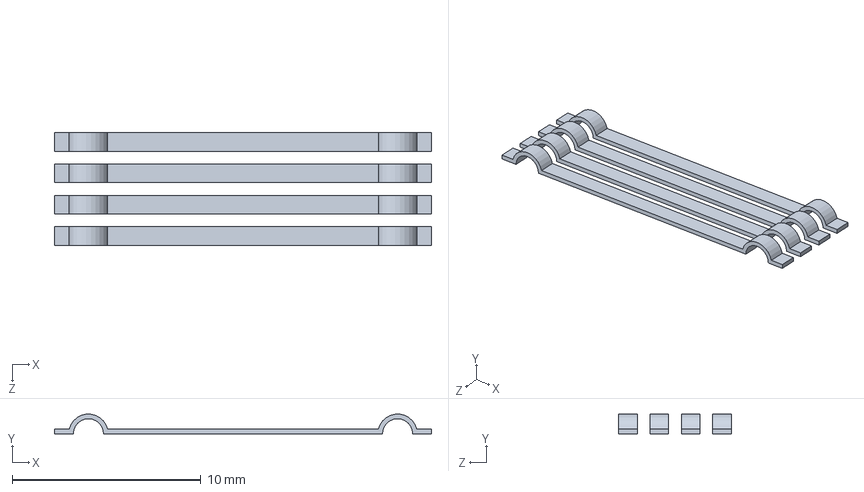
[picture p82: CAD file, 2017-10-23]
CAD/msc/845/845 - boat part 2.SLDPRT
20.0 x 1.04 x 6.00 mm
