linkejian123/Antique-Music-Box/CAD/msc/845/845 - anode lead to pin.SLDPRT

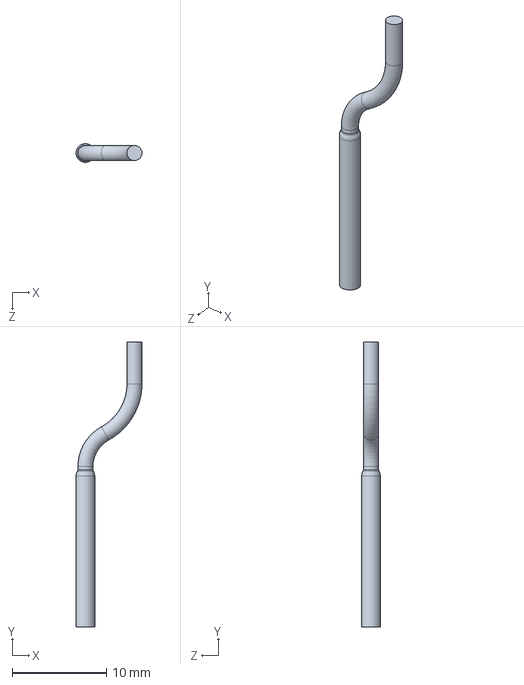
[picture p83: CAD file, 2017-10-23]
CAD/msc/845/845 - anode lead to pin.SLDPRT
7.00 x 30.2 x 2.00 mm
