linkejian123/Antique-Music-Box/CAD/msc/845/845 - grid support.SLDPRT

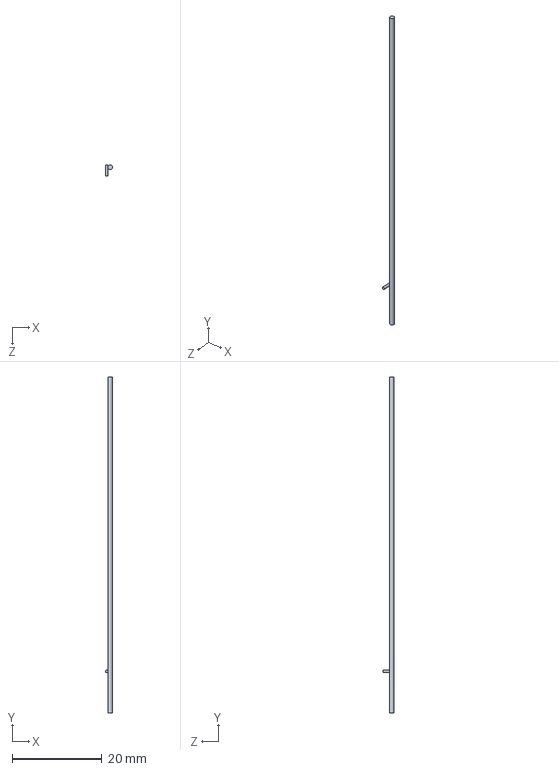
[picture p84: CAD file, 2017-10-23]
CAD/msc/845/845 - grid support.SLDPRT
1.65 x 75.0 x 2.55 mm
