linkejian123/Antique-Music-Box/SD/SD.X/FSIO.c

/******************************************************************************
*
*               Microchip Memory Disk Drive File System
*
******************************************************************************
* FileName:           FSIO.c
* Dependencies:       GenericTypeDefs.h
*                     FSIO.h
*                     Physical interface include file (SD-SPI.h, CF-PMP.h, ...)
*                     string.h
*                     stdlib.h
*                     FSDefs.h
*                     ctype.h
*                     salloc.h
* Processor:          PIC18/PIC24/dsPIC30/dsPIC33/PIC32
* Compiler:           C18/C30/C32
* Company:            Microchip Technology, Inc.
*
* Software License Agreement
*
* The software supplied herewith by Microchip Technology Incorporated
* (the ?Company?) for its PICmicro® Microcontroller is intended and
* supplied to you, the Company?s customer, for use solely and
* exclusively on Microchip PICmicro Microcontroller products. The
* software is owned by the Company and/or its supplier, and is
* protected under applicable copyright laws. All rights are reserved.
* Any use in violation of the foregoing restrictions may subject the
* user to criminal sanctions under applicable laws, as well as to
* civil liability for the breach of the terms and conditions of this
* license.
*
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
********************************************************************
 File Description:

 Change History:
  Rev     Description
  -----   -----------
  1.2.5   Fixed bug that prevented writes to alternate FAT tables
          Fixed bug that prevented FAT being updated when media is re-inserted

  1.2.6   Fixed bug that resulted in a bus error when attempts to read a invalid memory region
          Fixed bug that prevented the Windows Explorer to show the Date Creation field for directories

  x.x.x   Fixed issue on some USB drives where the information written
            to the drive is cached in a RAM for 500ms before it is 
            written to the flash unless the sector is accessed again.
          Add some error recovery for FAT32 systems when there is
            corruption in the boot sector.
********************************************************************/

#include "Compiler.h"
#include "FSIO.h"
#include "GenericTypeDefs.h"
#include <string.h>
#include <stdlib.h>
#include <ctype.h>
#include "FSDefs.h"


#ifdef ALLOW_FSFPRINTF
#include "stdarg.h"
#endif

#ifdef FS_DYNAMIC_MEM
   #ifdef __18CXX
      #include "salloc.h"
   #endif
#endif

#ifndef ALLOW_WRITES
   #ifdef ALLOW_FORMATS
      #error Write functions must be enabled to use the format function
   #endif
   #ifdef ALLOW_FSFPRINTF
      #error Write functions must be enabled to use the FSfprintf function
   #endif
#endif

#ifdef USEREALTIMECLOCK
    #ifdef USERDEFINEDCLOCK
        #error Please select only one timestamp clocking mode in FSconfig.h
    #endif
    #ifdef INCREMENTTIMESTAMP
        #error Please select only one timestamp clocking mode in FSconfig.h
    #endif
#elif defined USERDEFINEDCLOCK
    #ifdef INCREMENTTIMESTAMP
        #error Please select only one timestamp clocking mode in FSconfig.h
    #endif
#endif
/*****************************************************************************/
/*                         Global Variables                                  */
/*****************************************************************************/

#ifndef FS_DYNAMIC_MEM
    FSFILE  gFileArray[FS_MAX_FILES_OPEN];      // Array that contains file information (static allocation)
    BYTE    gFileSlotOpen[FS_MAX_FILES_OPEN];   // Array that indicates which elements of gFileArray are available for use
#endif

#if defined(USEREALTIMECLOCK) || defined(USERDEFINEDCLOCK)
// Timing variables
BYTE    gTimeCrtMS;     // Global time variable (for timestamps) used to indicate create time (milliseconds)
WORD    gTimeCrtTime;   // Global time variable (for timestamps) used to indicate create time
WORD    gTimeCrtDate;   // Global time variable (for timestamps) used to indicate create date
WORD    gTimeAccDate;   // Global time variable (for timestamps) used to indicate last access date
WORD    gTimeWrtTime;   // Global time variable (for timestamps) used to indicate last update time
WORD    gTimeWrtDate;   // Global time variable (for timestamps) used to indicate last update date
#endif

DWORD       gLastFATSectorRead = 0xFFFFFFFF;    // Global variable indicating which FAT sector was read last
BYTE        gNeedFATWrite = FALSE;              // Global variable indicating that there is information that needs to be written to the FAT
FSFILE  *   gBufferOwner = NULL;                // Global variable indicating which file is using the data buffer
DWORD       gLastDataSectorRead = 0xFFFFFFFF;   // Global variable indicating which data sector was read last
BYTE        gNeedDataWrite = FALSE;             // Global variable indicating that there is information that needs to be written to the data section
BYTE        nextClusterIsLast = FALSE;          // Global variable indicating that the entries in a directory align with a cluster boundary

BYTE    gBufferZeroed = FALSE;      // Global variable indicating that the data buffer contains all zeros

DWORD   FatRootDirClusterValue;     // Global variable containing the cluster number of the root dir (0 for FAT12/16)

BYTE    FSerrno;                    // Global error variable.  Set to one of many error codes after each function call.

DWORD   TempClusterCalc;            // Global variable used to store the calculated value of the cluster of a specified sector.
BYTE    dirCleared;                 // Global variable used by the "recursive" FSrmdir function to indicate that all subdirectories and files have been deleted from the target directory.
BYTE    recache = FALSE;            // Global variable used by the "recursive" FSrmdir function to indicate that additional cache reads are needed.
FSFILE  tempCWDobj;                 // Global variable used to preserve the current working directory information.
FSFILE  gFileTemp;                  // Global variable used for file operations.

#ifdef ALLOW_DIRS
    FSFILE   cwd;               // Global current working directory
    FSFILE * cwdptr = &cwd;     // Pointer to the current working directory
#endif


#ifdef __18CXX
    #pragma udata dataBuffer = DATA_BUFFER_ADDRESS
    BYTE gDataBuffer[MEDIA_SECTOR_SIZE];    // The global data sector buffer
    #pragma udata FATBuffer = FAT_BUFFER_ADDRESS
    BYTE gFATBuffer[MEDIA_SECTOR_SIZE];     // The global FAT sector buffer
#endif

#if defined (__C30__) || defined (__PIC32MX__)
    BYTE __attribute__ ((aligned(4)))   gDataBuffer[MEDIA_SECTOR_SIZE];     // The global data sector buffer
    BYTE __attribute__ ((aligned(4)))   gFATBuffer[MEDIA_SECTOR_SIZE];      // The global FAT sector buffer
#endif


#pragma udata

DISK gDiskData;         // Global structure containing device information.



/************************************************************************/
/*                        Structures and defines                        */
/************************************************************************/

// Directory entry structure
typedef struct
{
    char      DIR_Name[DIR_NAMESIZE];           // File name
    char      DIR_Extension[DIR_EXTENSION];     // File extension
    BYTE      DIR_Attr;                         // File attributes
    BYTE      DIR_NTRes;                        // Reserved byte
    BYTE      DIR_CrtTimeTenth;                 // Create time (millisecond field)
    WORD      DIR_CrtTime;                      // Create time (second, minute, hour field)
    WORD      DIR_CrtDate;                      // Create date
    WORD      DIR_LstAccDate;                   // Last access date
    WORD      DIR_FstClusHI;                    // High word of the entry's first cluster number
    WORD      DIR_WrtTime;                      // Last update time
    WORD      DIR_WrtDate;                      // Last update date
    WORD      DIR_FstClusLO;                    // Low word of the entry's first cluster number
    DWORD     DIR_FileSize;                     // The 32-bit file size
}_DIRENTRY;

typedef _DIRENTRY * DIRENTRY;                   // A pointer to a directory entry structure

#define DIRECTORY 0x12          // Value indicating that the CreateFileEntry function will be creating a directory

#define DIRENTRIES_PER_SECTOR   (MEDIA_SECTOR_SIZE / 32)        // The number of directory entries in a sector

// internal errors
#define CE_FAT_EOF            60   // Error that indicates an attempt to read FAT entries beyond the end of the file
#define CE_EOF                61   // Error that indicates that the end of the file has been reached

typedef FSFILE   * FILEOBJ;         // Pointer to an FSFILE object

#ifdef ALLOW_FSFPRINTF

#define _FLAG_MINUS 0x1             // FSfprintf minus flag indicator
#define _FLAG_PLUS  0x2             // FSfprintf plus flag indicator
#define _FLAG_SPACE 0x4             // FSfprintf space flag indicator
#define _FLAG_OCTO  0x8             // FSfprintf octothorpe (hash mark) flag indicator
#define _FLAG_ZERO  0x10            // FSfprintf zero flag indicator
#define _FLAG_SIGNED 0x80           // FSfprintf signed flag indicator

#ifdef __18CXX
    #define _FMT_UNSPECIFIED 0      // FSfprintf unspecified argument size flag
    #define _FMT_LONG 1             // FSfprintf 32-bit argument size flag
    #define _FMT_SHRTLONG 2         // FSfprintf 24-bit argument size flag
    #define _FMT_BYTE   3           // FSfprintf 8-bit argument size flag
#else
    #define _FMT_UNSPECIFIED 0      // FSfprintf unspecified argument size flag
    #define _FMT_LONGLONG 1         // FSfprintf 64-bit argument size flag
    #define _FMT_LONG 2             // FSfprintf 32-bit argument size flag
    #define _FMT_BYTE 3             // FSfprintf 8-bit argument size flag
#endif

#ifdef __18CXX
    static const rom char s_digits[] = "0123456789abcdef";      // FSfprintf table of conversion digits
#else
    static const char s_digits[] = "0123456789abcdef";          // FSfprintf table of conversion digits
#endif

#endif

/************************************************************************************/
/*                               Prototypes                                         */
/************************************************************************************/

DWORD ReadFAT (DISK *dsk, DWORD ccls);
DIRENTRY Cache_File_Entry( FILEOBJ fo, WORD * curEntry, BYTE ForceRead);
BYTE Fill_File_Object(FILEOBJ fo, WORD *fHandle);
DWORD Cluster2Sector(DISK * disk, DWORD cluster);
DIRENTRY LoadDirAttrib(FILEOBJ fo, WORD *fHandle);
#ifdef INCREMENTTIMESTAMP
    void IncrementTimeStamp(DIRENTRY dir);
#elif defined USEREALTIMECLOCK
    void CacheTime (void);
#endif

#if defined (__C30__) || defined (__PIC32MX__)
    BYTE ReadByte( BYTE* pBuffer, WORD index );
    WORD ReadWord( BYTE* pBuffer, WORD index );
    DWORD ReadDWord( BYTE* pBuffer, WORD index );
#endif

void FileObjectCopy(FILEOBJ foDest,FILEOBJ foSource);
BYTE ValidateChars (char * FileName, BYTE mode);
BYTE FormatFileName( const char* fileName, char* fN2, BYTE mode);
CETYPE FILEfind( FILEOBJ foDest, FILEOBJ foCompareTo, BYTE cmd, BYTE mode);
BYTE FILEget_next_cluster(FILEOBJ fo, DWORD n);
CETYPE FILEopen (FILEOBJ fo, WORD *fHandle, char type);

// Write functions
#ifdef ALLOW_WRITES
    BYTE Write_File_Entry( FILEOBJ fo, WORD * curEntry);
    BYTE flushData (void);
    CETYPE FILEerase( FILEOBJ fo, WORD *fHandle, BYTE EraseClusters);
    BYTE FILEallocate_new_cluster( FILEOBJ fo, BYTE mode);
    BYTE FAT_erase_cluster_chain (DWORD cluster, DISK * dsk);
    DWORD FATfindEmptyCluster(FILEOBJ fo);
    BYTE FindEmptyEntries(FILEOBJ fo, WORD *fHandle);
    BYTE PopulateEntries(FILEOBJ fo, char *name , WORD *fHandle, BYTE mode);
    CETYPE FILECreateHeadCluster( FILEOBJ fo, DWORD *cluster);
    BYTE EraseCluster(DISK *disk, DWORD cluster);
    CETYPE CreateFirstCluster(FILEOBJ fo);
    DWORD WriteFAT (DISK *dsk, DWORD ccls, DWORD value, BYTE forceWrite);
    CETYPE CreateFileEntry(FILEOBJ fo, WORD *fHandle, BYTE mode);
#endif

// Directory functions
#ifdef ALLOW_DIRS
    BYTE GetPreviousEntry (FSFILE * fo);
    BYTE FormatDirName (char * string, BYTE mode);
    int CreateDIR (char * path);
    BYTE writeDotEntries (DISK * dsk, DWORD dotAddress, DWORD dotdotAddress);
    int eraseDir (char * path);
#ifdef ALLOW_PGMFUNCTIONS
    #ifdef ALLOW_WRITES
        int mkdirhelper (BYTE mode, char * ramptr, const rom char * romptr);
        int rmdirhelper (BYTE mode, char * ramptr, const rom char * romptr, unsigned char rmsubdirs);
    #endif
int chdirhelper (BYTE mode, char * ramptr, const rom char * romptr);
#else
    #ifdef ALLOW_WRITES
        int mkdirhelper (BYTE mode, char * ramptr, char * romptr);
        int rmdirhelper (BYTE mode, char * ramptr, char * romptr, unsigned char rmsubdirs);
    #endif
    int chdirhelper (BYTE mode, char * ramptr, char * romptr);
#endif
#endif

#ifdef ALLOW_FSFPRINTF
    #ifdef __18CXX
        int FSvfprintf (auto FSFILE *handle, auto const rom char *formatString, auto va_list ap);
    #else
        int FSvfprintf (FSFILE *handle, const char *formatString, va_list ap);
    #endif
    int FSputc (char c, FSFILE * file);
    unsigned char str_put_n_chars (FSFILE * handle, unsigned char n, char c);
#endif

BYTE DISKmount( DISK *dsk);
BYTE LoadMBR(DISK *dsk);
BYTE LoadBootSector(DISK *dsk);
DWORD GetFullClusterNumber(DIRENTRY entry);


/*************************************************************************
  Function:
    int FSInit(void)
  Summary:
    Function to initialize the device.
  Conditions:
    The physical device should be connected to the microcontroller.
  Input:
    None
  Return Values:
    TRUE -  Initialization successful
    FALSE - Initialization unsuccessful
  Side Effects:
    The FSerrno variable will be changed.
  Description:
    Initializes the static or dynamic memory slots for holding file
    structures.  Initializes the device with the DISKmount function. Loads
    MBR and boot sector information.  Initializes the current working
    directory to the root directory for the device if directory support
    is enabled.
  Remarks:
    None
  *************************************************************************/

int FSInit(void)
{
    int fIndex;
#ifndef FS_DYNAMIC_MEM
    for( fIndex = 0; fIndex < FS_MAX_FILES_OPEN; fIndex++ )
        gFileSlotOpen[fIndex] = TRUE;
#else
    #ifdef __18CXX
        SRAMInitHeap();
    #endif
#endif

    gBufferZeroed = FALSE;
    gNeedFATWrite = FALSE;             
    gLastFATSectorRead = 0xFFFFFFFF;       
    gLastDataSectorRead = 0xFFFFFFFF;  

    MDD_InitIO();

    if(DISKmount(&gDiskData) == CE_GOOD)
    {
    // Initialize the current working directory to the root
#ifdef ALLOW_DIRS
        cwdptr->dsk = &gDiskData;
        cwdptr->sec = 0;
        cwdptr->pos = 0;
        cwdptr->seek = 0;
        cwdptr->size = 0;
        cwdptr->name[0] = '\\';
        for (fIndex = 1; fIndex < 11; fIndex++)
        {
            cwdptr->name[fIndex] = 0x20;
        }
        cwdptr->entry = 0;
        cwdptr->attributes = ATTR_DIRECTORY;
        // "FatRootDirClusterValue" indicates the root
        cwdptr->dirclus = FatRootDirClusterValue;
        cwdptr->dirccls = FatRootDirClusterValue;
#endif

        FSerrno = 0;
        return TRUE;
    }

    return FALSE;
}


/********************************************************************************
  Function:
    CETYPE FILEfind (FILEOBJ foDest, FILEOBJ foCompareTo, BYTE cmd, BYTE mode)
  Summary
    Finds a file on the device
  Conditions:
    This function should not be called by the user.
  Input:
    foDest -       FSFILE object containing information of the file found
    foCompareTo -  FSFILE object containing the name/attr of the file to be
                   found
    cmd -
        -          LOOK_FOR_EMPTY_ENTRY: Search for empty entry.
        -          LOOK_FOR_MATCHING_ENTRY: Search for matching entry.
    mode -
         -         0: Match file exactly with default attributes.
         -         1: Match file to user-specified attributes.
  Return Values:
    CE_GOOD -            File found.
    CE_FILE_NOT_FOUND -  File not found.
  Side Effects:
    None.
  Description:
    The FILEfind function will sequentially cache directory entries within
    the current working directory into the foDest FSFILE object.  If the cmd
    parameter is specified as LOOK_FOR_EMPTY_ENTRY the search will continue
    until an empty directory entry is found. If the cmd parameter is specified
    as LOOK_FOR_MATCHING_ENTRY these entries will be compared to the foCompareTo
    object until a match is found or there are no more entries in the current
    working directory. If the mode is specified a '0' the attributes of the FSFILE
    entries are irrelevant. If the mode is specified as '1' the attributes of the
    foDest entry must match the attributes specified in the foCompareTo file and
    partial string search characters may bypass portions of the comparison.
  Remarks:
    None
  ********************************************************************************/

CETYPE FILEfind( FILEOBJ foDest, FILEOBJ foCompareTo, BYTE cmd, BYTE mode)
{
    WORD   attrib, compareAttrib;
    WORD   fHandle = foDest->entry;                  // current entry counter
    BYTE   state,index;                              // state of the current object
    CETYPE   statusB = CE_FILE_NOT_FOUND;
    BYTE   character,test;

    // reset the cluster
    foDest->dirccls = foDest->dirclus;
    compareAttrib = 0xFFFF ^ foCompareTo->attributes;                // Attribute to be compared as per application layer request

    if (fHandle == 0)
    {
        if (Cache_File_Entry(foDest, &fHandle, TRUE) == NULL)
        {
            statusB = CE_BADCACHEREAD;
        }
    }
    else
    {
        if ((fHandle & MASK_MAX_FILE_ENTRY_LIMIT_BITS) != 0)          // Maximum 16 entries possible
        {
            if (Cache_File_Entry (foDest, &fHandle, TRUE) == NULL)
            {
                statusB = CE_BADCACHEREAD;
            }
        }
    }

    if (statusB != CE_BADCACHEREAD)
    {
        // Loop until you reach the end or find the file
        while(1)
        {
            if(statusB!=CE_GOOD) //First time entry always here
            {
                state = Fill_File_Object(foDest, &fHandle);
                if(state == NO_MORE) // Reached the end of available files. Comparision over and file not found so quit.
                {
                    break;
                }
            }
            else // statusB == CE_GOOD then exit
            {
                break; // Code below intializes"statusB = CE_GOOD;" so, if no problem in the filled file, Exit the while loop.
            }

            if(state == FOUND) // Validate the correct matching of filled file data with the required(to be found) one.
            {
                /* We got something */
                // get the attributes
                attrib = foDest->attributes;

                attrib &= ATTR_MASK;
                switch (mode)
                {
                    case 0:
                        // see if we are a volume id or hidden, ignore
                        if(attrib != ATTR_VOLUME)
                        {
                            statusB = CE_GOOD;
                            character = (BYTE)'m'; // random value

                            // search for one. if status = TRUE we found one
                            for(index = 0; index < DIR_NAMECOMP; index++)
                            {
                                // get the source character
                                character = foDest->name[index];
                                // get the destination character
                                test = foCompareTo->name[index];
                                if(tolower(character) != tolower(test))
                                {
                                    statusB = CE_FILE_NOT_FOUND; // Nope its not a match
                                    break;
                                }
                            }// for loop
                        } // not dir nor vol
                        break;

                    case 1:
                        // Check for attribute match
                        if (((attrib & compareAttrib) == 0) && (attrib != ATTR_LONG_NAME))
                        {
                            statusB = CE_GOOD;                 // Indicate the already filled file data is correct and go back
                            character = (BYTE)'m';             // random value
                            if (foCompareTo->name[0] != '*')   //If "*" is passed for comparion as 1st char then don't proceed. Go back, file alreay found.
                            {
                                for (index = 0; index < DIR_NAMESIZE; index++)
                                {
                                    // Get the source character
                                    character = foDest->name[index];
                                    // Get the destination character
                                    test = foCompareTo->name[index];
                                    if (test == '*')
                                        break;
                                    if (test != '?')
                                    {
                                        if(tolower(character) != tolower(test))
                                        {
                                            statusB = CE_FILE_NOT_FOUND; // it's not a match
                                            break;
                                        }
                                    }
                                }
                            }

                            // Before calling this "FILEfind" fn, "formatfilename" must be called. Hence, extn always starts from position "8".
                            if ((foCompareTo->name[8] != '*') && (statusB == CE_GOOD))
                            {
                                for (index = 8; index < DIR_NAMECOMP; index++)
                                {
                                    // Get the source character
                                    character = foDest->name[index];
                                    // Get the destination character
                                    test = foCompareTo->name[index];
                                    if (test == '*')
                                        break;
                                    if (test != '?')
                                    {
                                        if(tolower(character) != tolower(test))
                                        {
                                            statusB = CE_FILE_NOT_FOUND; // it's not a match
                                            break;
                                        }
                                    }
                                }
                            }

                        } // Attribute match

                        break;
                }
            } // not found
            else
            {
                /*** looking for an empty/re-usable entry ***/
                if ( cmd == LOOK_FOR_EMPTY_ENTRY)
                    statusB = CE_GOOD;
            } // found or not

            // increment it no matter what happened
            fHandle++;

        }// while
    }

    return(statusB);
} // FILEFind


/**************************************************************************
  Function:
    CETYPE FILEopen (FILEOBJ fo, WORD *fHandle, char type)
  Summary:
    Loads file information from the device
  Conditions:
    This function should not be called by the user.
  Input:
    fo -       File to be opened
    fHandle -  Location of file
    type -
         -     WRITE -  Create a new file or replace an existing file
         -     READ -   Read data from an existing file
         -     APPEND - Append data to an existing file
  Return Values:
    CE_GOOD -            FILEopen successful
    CE_NOT_INIT -        Device is not yet initialized
    CE_FILE_NOT_FOUND -  Could not find the file on the device
    CE_BAD_SECTOR_READ - A bad read of a sector occured
  Side Effects:
    None
  Description:
    This function will cache a directory entry in the directory specified
    by the dirclus parameter of hte FSFILE object 'fo.'  The offset of the
    entry in the directory is specified by fHandle.  Once the directory entry
    has been loaded, the first sector of the file can be loaded using the
    cluster value specified in the directory entry. The type argument will
    specify the mode the files will be opened in.  This will allow this
    function to set the correct read/write flags for the file.
  Remarks:
    If the mode the file is being opened in is a plus mode (e.g. READ+) the
    flags will be modified further in the FSfopen function.
  **************************************************************************/

CETYPE FILEopen (FILEOBJ fo, WORD *fHandle, char type)
{
    DISK   *dsk;      //Disk structure
    BYTE    r;               //Result of search for file
    DWORD    l;               //lba of first sector of first cluster
    CETYPE    error = CE_GOOD;

    dsk = (DISK *)(fo->dsk);
    if (dsk->mount == FALSE)
    {
        error = CE_NOT_INIT;
    }
    else
    {
        // load the sector
        fo->dirccls = fo->dirclus;
        // Cache no matter what if it's the first entry
        if (*fHandle == 0)
        {
            if (Cache_File_Entry(fo, fHandle, TRUE) == NULL)
            {
                error = CE_BADCACHEREAD;
            }
        }
        else
        {
            // If it's not the first, only cache it if it's
            // not divisible by the number of entries per sector
            // If it is, Fill_File_Object will cache it
            if ((*fHandle & 0xf) != 0)
            {
                if (Cache_File_Entry (fo, fHandle, TRUE) == NULL)
                {
                    error = CE_BADCACHEREAD;
                }
            }
        }

        // Fill up the File Object with the information pointed to by fHandle
        r = Fill_File_Object(fo, fHandle);
        if (r != FOUND)
            error = CE_FILE_NOT_FOUND;
        else
        {
            fo->seek = 0;               // first byte in file
            fo->ccls = fo->cluster;     // first cluster
            fo->sec = 0;                // first sector in the cluster
            fo->pos = 0;                // first byte in sector/cluster

            if  ( r == NOT_FOUND)
            {
                error = CE_FILE_NOT_FOUND;
            }
            else
            {
                // Determine the lba of the selected sector and load
                l = Cluster2Sector(dsk,fo->ccls);
#ifdef ALLOW_WRITES
                if (gNeedDataWrite)
                    if (flushData())
                        return CE_WRITE_ERROR;
#endif
                gBufferOwner = fo;
                if (gLastDataSectorRead != l)
                {
                    gBufferZeroed = FALSE;
                    if ( !MDD_SectorRead( l, dsk->buffer))
                        error = CE_BAD_SECTOR_READ;
                    gLastDataSectorRead = l;
                }
            } // -- found

            fo->flags.FileWriteEOF = FALSE;
            // Set flag for operation type
#ifdef ALLOW_WRITES
            if (type == 'w' || type == 'a')
            {
                fo->flags.write = 1;   //write or append
                fo->flags.read = 0;
            }
            else
            {
#endif
                fo->flags.write = 0;   //read
                fo->flags.read = 1;
#ifdef ALLOW_WRITES
            } // -- flags
#endif
        } // -- r = Found
    } // -- Mounted
    return (error);
} // -- FILEopen


/*************************************************************************
  Function:
    BYTE FILEget_next_cluster(FILEOBJ fo, WORD n)
  Summary:
    Step through a chain of clusters
  Conditions:
    This function should not be called by the user.
  Input:
    fo - The file to get the next cluster of
    n -  Number of links in the FAT cluster chain to jump through
  Return Values:
    CE_GOOD - Operation successful
    CE_BAD_SECTOR_READ - A bad read occured of a sector
    CE_INVALID_CLUSTER - Invalid cluster value \> maxcls
    CE_FAT_EOF - Fat attempt to read beyond EOF
  Side Effects:
    None
  Description:
    This function will load 'n' proximate clusters for a file from
    the FAT on the device.  It will stop checking for clusters if the
    ReadFAT function returns an error, if it reaches the last cluster in
    a file, or if the device tries to read beyond the last cluster used
    by the device.
  Remarks:
    None
  *************************************************************************/

BYTE FILEget_next_cluster(FILEOBJ fo, DWORD n)
{
    DWORD         c, c2, ClusterFailValue, LastClustervalue;
    BYTE          error = CE_GOOD;
    DISK *      disk;

    disk = fo->dsk;

    /* Settings based on FAT type */
    switch (disk->type)
    {
#ifdef SUPPORT_FAT32 // If FAT32 supported.
        case FAT32:
            LastClustervalue = LAST_CLUSTER_FAT32;
            ClusterFailValue  = CLUSTER_FAIL_FAT32;
            break;
#endif
        case FAT12:
            LastClustervalue = LAST_CLUSTER_FAT12;
            ClusterFailValue  = CLUSTER_FAIL_FAT16;
            break;
        case FAT16:
        default:
            LastClustervalue = LAST_CLUSTER_FAT16;
            ClusterFailValue  = CLUSTER_FAIL_FAT16;
            break;
    }

    // loop n times
    do
    {
        // get the next cluster link from FAT
        c2 = fo->ccls;
        if ( (c = ReadFAT( disk, c2)) == ClusterFailValue)
            error = CE_BAD_SECTOR_READ;
        else
        {
            // check if cluster value is valid
            if ( c >= disk->maxcls)
            {
                error = CE_INVALID_CLUSTER;
            }

            // compare against max value of a cluster in FAT
            // return if eof
            if ( c >= LastClustervalue)    // check against eof
            {
                error = CE_FAT_EOF;
            }
        }

        // update the FSFILE structure
        fo->ccls = c;

    } while (--n > 0 && error == CE_GOOD);// loop end

    return(error);
} // get next cluster


/**************************************************************************
  Function:
    BYTE DISKmount ( DISK *dsk)
  Summary:
    Initialies the device and loads MBR and boot sector information
  Conditions:
    This function should not be called by the user.
  Input:
    dsk -  The disk structure to be initialized.
  Return Values:
    CE_GOOD -       Disk mounted
    CE_INIT_ERROR - Initialization error has occured
    CE_UNSUPPORTED_SECTOR_SIZE - Media sector size bigger than
                MEDIA_SECTOR_SIZE as defined in FSconfig.h.
  Side Effects:
    None
  Description:
    This function will use the function pointed to by the MDD_MediaInitialize
    function pointer to initialize the device (if any initialization is
    required).  It then attempts to load the master boot record with the
    LoadMBR function and the boot sector with the LoadBootSector function.
    These two functions will be used to initialize a global DISK structure
    that will be used when accessing file information in the future.
  Remarks:
    None
  **************************************************************************/

BYTE DISKmount( DISK *dsk)
{
    BYTE                error = CE_GOOD;
    MEDIA_INFORMATION   *mediaInformation;

    dsk->mount = FALSE; // default invalid
    dsk->buffer = gDataBuffer;    // assign buffer

    // Initialize the device
    mediaInformation = MDD_MediaInitialize();
    if (mediaInformation->errorCode != MEDIA_NO_ERROR)
    {
        error = CE_INIT_ERROR;
        FSerrno = CE_INIT_ERROR;
    }
    else
    {
        // If the media initialization routine determined the sector size,
        // check it and make sure we can support it.
        if (mediaInformation->validityFlags.bits.sectorSize)
        {
			dsk->sectorSize = mediaInformation->sectorSize;
            if (mediaInformation->sectorSize > MEDIA_SECTOR_SIZE)
            {
                error = CE_UNSUPPORTED_SECTOR_SIZE;
                FSerrno = CE_UNSUPPORTED_SECTOR_SIZE;
                return error;
            }
        }

        // Load the Master Boot Record (partition)
        if((error = LoadMBR(dsk)) == CE_GOOD)
        {
            // Now the boot sector
            if((error = LoadBootSector(dsk)) == CE_GOOD)
                dsk->mount = TRUE; // Mark that the DISK mounted successfully
        }
    } // -- Load file parameters

    return(error);
} // -- mount



/********************************************************************
  Function:
    CETYPE LoadMBR ( DISK *dsk)
  Summary:
    Loads the MBR and extracts necessary information
  Conditions:
    This function should not be called by the user.
  Input:
    dsk -  The disk containing the master boot record to be loaded
  Return Values:
    CE_GOOD -            MBR loaded successfully
    CE_BAD_SECTOR_READ - A bad read occured of a sector
    CE_BAD_PARTITION -   The boot record is bad
  Side Effects:
    None
  Description:
    The LoadMBR function will use the function pointed to by the
    MDD_SectorRead function pointer to read the 0 sector from the
    device.  If a valid boot signature is obtained, this function
    will compare fields in that cached sector to the values that
    would be present if that sector was a boot sector.  If all of
    those values match, it will be assumed that the device does not
    have a master boot record and the 0 sector is actually the boot
    sector.  Otherwise, data about the partition and the actual
    location of the boot sector will be loaded from the MBR into
    the DISK structure pointed to by 'dsk.'
  Remarks:
    None
  ********************************************************************/

BYTE LoadMBR(DISK *dsk)
{
    PT_MBR  Partition;
    BYTE error = CE_GOOD;
    BYTE type;
    BootSec BSec;

    // Get the partition table from the MBR
    if ( MDD_SectorRead( FO_MBR, dsk->buffer) != TRUE)
    {
        error = CE_BAD_SECTOR_READ;
        FSerrno = CE_BAD_SECTOR_READ;
    }
    else
    {
        // Check if the card has no MBR
        BSec = (BootSec) dsk->buffer;

        if((BSec->Signature0 == FAT_GOOD_SIGN_0) && (BSec->Signature1 == FAT_GOOD_SIGN_1))
        {
         // Technically, the OEM name is not for indication
         // The alternative is to read the CIS from attribute
         // memory.  See the PCMCIA metaformat for more details
#if defined (__C30__) || defined (__PIC32MX__)
            if (ReadByte( dsk->buffer, BSI_FSTYPE ) == 'F' && \
            ReadByte( dsk->buffer, BSI_FSTYPE + 1 ) == 'A' && \
            ReadByte( dsk->buffer, BSI_FSTYPE + 2 ) == 'T' && \
            ReadByte( dsk->buffer, BSI_FSTYPE + 3 ) == '1' && \
            ReadByte( dsk->buffer, BSI_BOOTSIG) == 0x29)
#else
            if (BSec->FAT.FAT_16.BootSec_FSType[0] == 'F' && \
                BSec->FAT.FAT_16.BootSec_FSType[1] == 'A' && \
                BSec->FAT.FAT_16.BootSec_FSType[2] == 'T' && \
                BSec->FAT.FAT_16.BootSec_FSType[3] == '1' && \
                BSec->FAT.FAT_16.BootSec_BootSig == 0x29)
#endif
             {
                dsk->firsts = 0;
                dsk->type = FAT16;
                return CE_GOOD;
             }
             else
             {
#if defined (__C30__) || defined (__PIC32MX__)
                if (ReadByte( dsk->buffer, BSI_FAT32_FSTYPE ) == 'F' && \
                    ReadByte( dsk->buffer, BSI_FAT32_FSTYPE + 1 ) == 'A' && \
                    ReadByte( dsk->buffer, BSI_FAT32_FSTYPE + 2 ) == 'T' && \
                    ReadByte( dsk->buffer, BSI_FAT32_FSTYPE + 3 ) == '3' && \
                    ReadByte( dsk->buffer, BSI_FAT32_BOOTSIG) == 0x29)
#else
                if (BSec->FAT.FAT_32.BootSec_FilSysType[0] == 'F' && \
                    BSec->FAT.FAT_32.BootSec_FilSysType[1] == 'A' && \
                    BSec->FAT.FAT_32.BootSec_FilSysType[2] == 'T' && \
                    BSec->FAT.FAT_32.BootSec_FilSysType[3] == '3' && \
                    BSec->FAT.FAT_32.BootSec_BootSig == 0x29)
#endif
                {
                    dsk->firsts = 0;
                    dsk->type = FAT32;
                    return CE_GOOD;
                }
            }
        }
        // assign it the partition table strucutre
        Partition = (PT_MBR)dsk->buffer;

        // Ensure its good
        if((Partition->Signature0 != FAT_GOOD_SIGN_0) || (Partition->Signature1 != FAT_GOOD_SIGN_1))
        {
            FSerrno = CE_BAD_PARTITION;
            error = CE_BAD_PARTITION;
        }
        else
        {
            /*    Valid Master Boot Record Loaded   */

            // Get the 32 bit offset to the first partition
            dsk->firsts = Partition->Partition0.PTE_FrstSect;

            // check if the partition type is acceptable
              type = Partition->Partition0.PTE_FSDesc;

            switch (type)
            {
                case 0x01:
                    dsk->type = FAT12;
                    break;

            case 0x04:
                case 0x06:
                case 0x0E:
                    dsk->type = FAT16;
                    break;

                case 0x0B:
                case 0x0C:

#ifdef SUPPORT_FAT32 // If FAT32 supported.
            dsk->type = FAT32;    // FAT32 is supported too
#else
            FSerrno = CE_CARDFAT32;
            error = CE_CARDFAT32;
#endif
                    break;

                default:
                    FSerrno = CE_UNSUPPORTED_FS;
                    error = CE_UNSUPPORTED_FS;
            } // switch
        }
    }

    return(error);
}// -- LoadMBR


/**************************************************************************
  Function:
    BYTE LoadBootSector (DISK *dsk)
  Summary:
    Load the boot sector and extract the necessary information
  Conditions:
    This function should not be called by the user.
  Input:
    dsk -  The disk containing the boot sector
  Return Values:
    CE_GOOD -                    Boot sector loaded
    CE_BAD_SECTOR_READ -         A bad read occured of a sector
    CE_NOT_FORMATTED -           The disk is of an unsupported format
    CE_CARDFAT32 -               FAT 32 device not supported
    CE_UNSUPPORTED_SECTOR_SIZE - The sector size is not supported
  Side Effects:
    None
  Description:
    LoadBootSector will use the function pointed to by the MDD_SectorWrite
    function pointer to load the boot sector, whose location was obtained
    by a previous call of LoadMBR.  If the boot sector is loaded successfully,
    partition information will be calcualted from it and copied into the DISK
    structure pointed to by 'dsk.'
  Remarks:
    None
  **************************************************************************/


BYTE LoadBootSector(DISK *dsk)
{
    DWORD       RootDirSectors;
    DWORD       TotSec,DataSec;
    BYTE        error = CE_GOOD;
    BootSec     BSec;
    WORD        BytesPerSec;
    WORD        ReservedSectorCount;

    #if defined(SUPPORT_FAT32)
    BOOL        TriedSpecifiedBackupBootSec = FALSE;
    BOOL        TriedBackupBootSecAtAddress6 = FALSE;
    #endif
    // Get the Boot sector
    if ( MDD_SectorRead( dsk->firsts, dsk->buffer) != TRUE)
    {
        error = CE_BAD_SECTOR_READ;
    }
    else
    {
        BSec = (BootSec)dsk->buffer;

        do      //test each possible boot sector (FAT32 can have backup boot sectors)
        {

            //Verify the Boot Sector has a valid signature
            if(    (BSec->Signature0 != FAT_GOOD_SIGN_0)
                || (BSec->Signature1 != FAT_GOOD_SIGN_1)
              )
            {
                error = CE_NOT_FORMATTED;
            }
            else   
            {

                do      //loop just to allow a break to jump out of this section of code
                {
                    #ifdef __18CXX
                    // Load count of sectors per cluster
                    dsk->SecPerClus = BSec->FAT.FAT_16.BootSec_SPC;
                    // Load the sector number of the first FAT sector
                    dsk->fat        = dsk->firsts + BSec->FAT.FAT_16.BootSec_ResrvSec;
                    // Load the count of FAT tables
                    dsk->fatcopy    = BSec->FAT.FAT_16.BootSec_FATCount;
                    // Load the size of the FATs
                    dsk->fatsize = BSec->FAT.FAT_16.BootSec_SPF;
                    if(dsk->fatsize == 0)
                        dsk->fatsize  = BSec->FAT.FAT_32.BootSec_FATSz32;
                    // Calculate the location of the root sector (for FAT12/16)
                    dsk->root = dsk->fat + (DWORD)(dsk->fatcopy * (DWORD)dsk->fatsize);
                    // Determine the max size of the root (will be 0 for FAT32)
                    dsk->maxroot    = BSec->FAT.FAT_16.BootSec_RootDirEnts;
    
                    // Determine the total number of sectors in the partition
                    if(BSec->FAT.FAT_16.BootSec_TotSec16 != 0)
                    {
                        TotSec = BSec->FAT.FAT_16.BootSec_TotSec16;
                    }
                    else
                    {
                        TotSec = BSec->FAT.FAT_16.BootSec_TotSec32;
                    }
    
                    // Calculate the number of bytes in each sector
                    BytesPerSec = BSec->FAT.FAT_16.BootSec_BPS;
                    if( BytesPerSec == 0 || (BytesPerSec & 1) == 1 )
                    {
                        error = CE_UNSUPPORTED_SECTOR_SIZE;
                        break;  //break out of the do while loop
                    }
    
                    // Calculate the number of sectors in the root (will be 0 for FAT32)
                    RootDirSectors = ((BSec->FAT.FAT_16.BootSec_RootDirEnts * 32) + (BSec->FAT.FAT_16.BootSec_BPS - 1)) / BSec->FAT.FAT_16.BootSec_BPS;
                    // Calculate the number of data sectors on the card
                    DataSec = TotSec - (dsk->root + RootDirSectors);
                    // Calculate the maximum number of clusters on the card
                    dsk->maxcls = DataSec / dsk->SecPerClus;
    
                    #else // PIC24/30/33
    
                    // Read the count of reserved sectors
                    ReservedSectorCount = ReadWord( dsk->buffer, BSI_RESRVSEC );
                    // Load the count of sectors per cluster
                    dsk->SecPerClus = ReadByte( dsk->buffer, BSI_SPC );
                    // Load the sector number of the first FAT sector
                    dsk->fat = dsk->firsts + ReservedSectorCount;
                    // Load the count of FAT tables
                    dsk->fatcopy    = ReadByte( dsk->buffer, BSI_FATCOUNT );
                    // Load the size of the FATs
                    dsk->fatsize = ReadWord( dsk->buffer, BSI_SPF );
                    if(dsk->fatsize == 0)
                        dsk->fatsize  = ReadDWord( dsk->buffer, BSI_FATSZ32 );
                    // Calculate the location of the root sector (for FAT12/16)
                    dsk->root = dsk->fat + (DWORD)(dsk->fatcopy * (DWORD)dsk->fatsize);
                    // Determine the max size of the root (will be 0 for FAT32)
                    dsk->maxroot = ReadWord( dsk->buffer, BSI_ROOTDIRENTS );
    
                    // Determine the total number of sectors in the partition
                    TotSec = ReadWord( dsk->buffer, BSI_TOTSEC16 );
                    if( TotSec == 0 )
                        TotSec = ReadDWord( dsk->buffer, BSI_TOTSEC32 );
    
                    // Calculate the number of bytes in each sector
                    BytesPerSec = ReadWord( dsk->buffer, BSI_BPS );
                    if( BytesPerSec == 0 || (BytesPerSec & 1) == 1 )
                    {
                        error = CE_UNSUPPORTED_SECTOR_SIZE;
                        break;
                    }
    
                    // Calculate the number of sectors in the root (will be 0 for FAT32)
                    RootDirSectors = ((dsk->maxroot * NUMBER_OF_BYTES_IN_DIR_ENTRY) + (BytesPerSec - 1)) / BytesPerSec;
                    // Calculate the number of data sectors on the card
                    DataSec = TotSec - (ReservedSectorCount + (dsk->fatcopy * dsk->fatsize )  + RootDirSectors);
                    // Calculate the maximum number of clusters on the card
                    dsk->maxcls = DataSec / dsk->SecPerClus;
    
                    #endif
    
                    // Determine the file system type based on the number of clusters used
                    if(dsk->maxcls < 4085)
                    {
                        dsk->type = FAT12;
                    }
                    else
                    {
                        if(dsk->maxcls < 65525)
                        {
                            dsk->type = FAT16;
                        }
                        else
                        {
                            #ifdef SUPPORT_FAT32
                                dsk->type = FAT32;
                            #else
                                error = CE_CARDFAT32;
                            #endif
                        }
                    }
        
                    #ifdef SUPPORT_FAT32
                        if (dsk->type == FAT32)
                        {
                            #ifdef __18CXX
                                FatRootDirClusterValue =  BSec->FAT.FAT_32.BootSec_RootClus;
                            #else
                                FatRootDirClusterValue = ReadDWord( dsk->buffer, BSI_ROOTCLUS );
                            #endif
                            dsk->data = dsk->root + RootDirSectors;
                        }
                        else
                    #endif
                    {
                        FatRootDirClusterValue = 0;
                        dsk->data = dsk->root + ( dsk->maxroot >> 4);
                    }
    
                #ifdef __18CXX
                    if(BSec->FAT.FAT_16.BootSec_BPS > MEDIA_SECTOR_SIZE)
                #else
                    if(BytesPerSec > MEDIA_SECTOR_SIZE)
                #endif
                    {
                        error = CE_UNSUPPORTED_SECTOR_SIZE;
                    }

                }while(0);  // do/while loop designed to allow to break out if
                            //   there is an error detected without returning
                            //   from the function.

            }

            #if defined(SUPPORT_FAT32)
            if ((dsk->type == FAT32) || ((error != CE_GOOD) && ((BSec->FAT.FAT_32.BootSec_BootSig == 0x29) || (BSec->FAT.FAT_32.BootSec_BootSig == 0x28))))
            {
                //Check for possible errors in the formatting
                if(    (BSec->FAT.FAT_32.BootSec_TotSec16 != 0)
                    || (BSec->FAT.FAT_32.BootSec_Reserved[0] != 0)
                    || (BSec->FAT.FAT_32.BootSec_Reserved[1] != 0)
                    || (BSec->FAT.FAT_32.BootSec_Reserved[2] != 0)
                    || (BSec->FAT.FAT_32.BootSec_Reserved[3] != 0)
                    || (BSec->FAT.FAT_32.BootSec_Reserved[4] != 0)
                    || (BSec->FAT.FAT_32.BootSec_Reserved[5] != 0)
                    || (BSec->FAT.FAT_32.BootSec_Reserved[6] != 0)
                    || (BSec->FAT.FAT_32.BootSec_Reserved[7] != 0)
                    || (BSec->FAT.FAT_32.BootSec_Reserved[8] != 0)
                    || (BSec->FAT.FAT_32.BootSec_Reserved[9] != 0)
                    || (BSec->FAT.FAT_32.BootSec_Reserved[10] != 0)
                    || (BSec->FAT.FAT_32.BootSec_Reserved[11] != 0)
                    || ((BSec->FAT.FAT_32.BootSec_BootSig != 0x29) && (BSec->FAT.FAT_32.BootSec_BootSig != 0x28))
                  )
                {
                    error = CE_NOT_FORMATTED;
                }
    
                //If there were formatting errors then in FAT32 we can try to use
                //  the backup boot sector
                if((error != CE_GOOD) && (TriedSpecifiedBackupBootSec == FALSE))
                {
                    TriedSpecifiedBackupBootSec = TRUE;
    
                    if ( MDD_SectorRead( dsk->firsts + BSec->FAT.FAT_32.BootSec_BkBootSec, dsk->buffer) != TRUE)
                    {
                        FSerrno = CE_BAD_SECTOR_READ;
                        return CE_BAD_SECTOR_READ;
                    }
                    else
                    {
                        error = CE_GOOD;
                        continue;
                    }
                }
    
                if((error != CE_GOOD) && (TriedBackupBootSecAtAddress6 == FALSE))
                {
                    TriedBackupBootSecAtAddress6 = TRUE;
    
                    //Here we are using the magic number 6 because the FAT32 specification
                    //  recommends that "No value other than 6 is recommended."  We've
                    //  already tried using the value specified in the BPB_BkBootSec
                    //  field and it must have failed
                    if ( MDD_SectorRead( dsk->firsts + 6, dsk->buffer) != TRUE)
                    {
                        FSerrno = CE_BAD_SECTOR_READ;
                        return CE_BAD_SECTOR_READ;
                    }
                    else
                    {
                        error = CE_GOOD;
                        continue;
                    }
                }

            }   //type == FAT32
            #endif  //SUPPORT_FAT32
            break;
        }
        while(1);
    }

    if(error != CE_GOOD)
    {
        FSerrno = error;
    }

    return(error);
}



/*************************************************************************
  Function:
    DWORD GetFullClusterNumber (DIRENTRY entry)
  Summary:
    Gets the cluster number from a directory entry
  Conditions:
    This function should not be called by the user.
  Input:
    entry - The cached directory entry to get the cluster number from
  Returns:
    The cluster value from the passed directory entry
  Side Effects:
    None.
  Description:
    This function will load both the high and low 16-bit first cluster
    values of a file from a directory entry and copy them into a 32-bit
    cluster number variable, which will be returned.
  Remarks:
    None
  *************************************************************************/

DWORD GetFullClusterNumber(DIRENTRY entry)
{

    DWORD TempFullClusterCalc = 0;

#ifndef SUPPORT_FAT32 // If FAT32 Not supported.
    entry->DIR_FstClusHI = 0; // If FAT32 is not supported then Higher Word of the address is "0"
#endif

    // Get the cluster
    TempFullClusterCalc = (entry->DIR_FstClusHI);
    TempFullClusterCalc = TempFullClusterCalc << 16;
    TempFullClusterCalc |= entry->DIR_FstClusLO;

    return TempFullClusterCalc;
}


#ifdef ALLOW_FORMATS
#ifdef ALLOW_WRITES


/*********************************************************************************
  Function:
    int FSCreateMBR (unsigned long firstSector, unsigned long numSectors)
  Summary:
    Creates a master boot record
  Conditions:
    The I/O pins for the device have been initialized by the InitIO function.
  Input:
    firstSector -  The first sector of the partition on the device (cannot
                   be 0; that's the MBR)
    numSectors -   The number of sectors available in memory (including the
                   MBR)
  Return Values:
    0 -   MBR was created successfully
    EOF - MBR could not be created
  Side Effects:
    None
  Description:
    This function can be used to create a master boot record for a device.  Note
    that this function should not be used on a device that is already formatted
    with a master boot record (i.e. most SD cards, CF cards, USB keys).  This
    function will fill the global data buffer with appropriate partition information
    for a FAT partition with a type determined by the number of sectors available
    to the partition.  It will then write the MBR information to the first sector
    on the device.  This function should be followed by a call to FSformat, which
    will create a boot sector, root dir, and FAT appropriate the the information
    contained in the new master boot record.  Note that FSformat only supports
    FAT12 and FAT16 formatting at this time, and so cannot be used to format a
    device with more than 0x3FFD5F sectors.
  Remarks:
    This function can damage the device being used, and should not be called
    unless the user is sure about the size of the device and the first sector value.
  *********************************************************************************/

int FSCreateMBR (unsigned long firstSector, unsigned long numSectors)
{
    PT_MBR  Partition;
    DWORD CyHdSc = 0x00000000;
    DWORD tempSector;

    if ((firstSector == 0) || (numSectors <= 1))
        return EOF;

    if (firstSector > (numSectors - 1))
        return EOF;

    if (gNeedDataWrite)
        if (flushData())
            return EOF;

    memset (gDataBuffer, 0x00, MEDIA_SECTOR_SIZE);

    Partition = (PT_MBR) gDataBuffer;

    // Set Cylinder-head-sector address of the first sector
    tempSector = firstSector;
    CyHdSc = (tempSector / (unsigned int)16065 ) << 14;
    tempSector %= 16065;
    CyHdSc |= (tempSector / 63) << 6;
    tempSector %= 63;
    CyHdSc |= tempSector + 1;
    gDataBuffer[447] = (BYTE)((CyHdSc >> 16) & 0xFF);
    gDataBuffer[448] = (BYTE)((CyHdSc >> 8) & 0xFF);
    gDataBuffer[449] = (BYTE)((CyHdSc) & 0xFF);

    // Set the count of sectors
    Partition->Partition0.PTE_NumSect = numSectors - firstSector;

    // Set the partition type
    // We only support creating FAT12 and FAT16 MBRs at this time
    if (Partition->Partition0.PTE_NumSect < 0x1039)
    {
        // FAT12
        Partition->Partition0.PTE_FSDesc = 0x01;
    }
    else if (Partition->Partition0.PTE_NumSect <= 0x3FFD5F)
    {
        // FAT16
        Partition->Partition0.PTE_FSDesc = 0x06;
    }
    else
        return EOF;

    // Set the LBA of the first sector
    Partition->Partition0.PTE_FrstSect = firstSector;

    // Set the Cylinder-head-sector address of the last sector
    tempSector = firstSector + numSectors - 1;
    CyHdSc = (tempSector / (unsigned int)16065 ) << 14;
    tempSector %= 16065;
    CyHdSc |= (tempSector / 63) << 6;
    tempSector %= 63;
    CyHdSc |= tempSector + 1;
    gDataBuffer[451] = (BYTE)((CyHdSc >> 16) & 0xFF);
    gDataBuffer[452] = (BYTE)((CyHdSc >> 8) & 0xFF);
    gDataBuffer[453] = (BYTE)((CyHdSc) & 0xFF);

    // Set the boot descriptor.  This will be 0, since we won't
    // be booting anything from our device probably
    Partition->Partition0.PTE_BootDes = 0x00;

    // Set the signature codes
    Partition->Signature0 = 0x55;
    Partition->Signature1 = 0xAA;

    if (MDD_SectorWrite (0x00, gDataBuffer, TRUE) != TRUE)
        return EOF;
    else
        return 0;

}



/*******************************************************************
  Function:
    int FSformat (char mode, long int serialNumber, char * volumeID)
  Summary:
    Formats a device
  Conditions:
    The device must possess a valid master boot record.
  Input:
    mode -          - 0 - Just erase the FAT and root
                    - 1 - Create a new boot sector
    serialNumber -  Serial number to write to the card
    volumeID -      Name of the card
  Return Values:
    0 -    Format was successful
    EOF -  Format was unsuccessful
  Side Effects:
    The FSerrno variable will be changed.
  Description:
    The FSformat function can be used to create a new boot sector
    on a device, based on the information in the master boot record.
    This function will first initialize the I/O pins and the device,
    and then attempts to read the master boot record.  If the MBR
    cannot be loaded successfully, the function will fail.  Next, if
    the 'mode' argument is specified as '0' the existing boot sector
    information will be loaded.  If the 'mode' argument is '1' an
    entirely new boot sector will be constructed using the disk
    values from the master boot record.  Once the boot sector has
    been successfully loaded/created, the locations of the FAT and
    root will be loaded from it, and they will be completely
    erased.  If the user has specified a volumeID parameter, a
    VOLUME attribute entry will be created in the root directory
    to name the device.

    FAT12, FAT16 and FAT32 formatting are supported.

    Based on the number of sectors, the format function automatically
    compute the smallest possible value for the cluster size in order to
    accommodate the physical size of the media. In this case, if a media 
    with a big capacity is formatted, the format function may take a very
    long time to write all the FAT tables. 

    Therefore, the FORMAT_SECTORS_PER_CLUSTER macro may be used to 
    specify the exact cluster size (in multiples of sector size). This 
    macro can be defined in FSconfig.h

  Remarks:
    Only devices with a sector size of 512 bytes are supported by the 
    format function
  *******************************************************************/

int FSformat (char mode, long int serialNumber, char * volumeID)
{
    PT_MBR   masterBootRecord;
    DWORD    secCount, DataClusters, RootDirSectors;
    BootSec   BSec;
    DISK   d;
    DISK * disk = &d;
    WORD    j;
    DWORD   fatsize, test;
    DWORD Index;
    MEDIA_INFORMATION * mediaInfo;
#ifdef __18CXX
    // This is here because of a C18 compiler feature
    BYTE *  dataBufferPointer = gDataBuffer;
#endif

    FSerrno = CE_GOOD;

    gBufferZeroed = FALSE;
    gNeedFATWrite = FALSE;             
    gLastFATSectorRead = 0xFFFFFFFF;       
    gLastDataSectorRead = 0xFFFFFFFF;  

    disk->buffer = gDataBuffer;

    MDD_InitIO();

    mediaInfo = MDD_MediaInitialize();
    if (mediaInfo->errorCode != MEDIA_NO_ERROR)
    {
        FSerrno = CE_INIT_ERROR;
        return EOF;
    }

    if (MDD_SectorRead (0x00, gDataBuffer) == FALSE)
    {
        FSerrno = CE_BADCACHEREAD;
        return EOF;
    }

    // Check if the card has no MBR
    BSec = (BootSec) disk->buffer;
    if((BSec->Signature0 == FAT_GOOD_SIGN_0) && (BSec->Signature1 == FAT_GOOD_SIGN_1))
    {
        // Technically, the OEM name is not for indication
        // The alternative is to read the CIS from attribute
        // memory.  See the PCMCIA metaformat for more details
#if defined (__C30__) || defined (__PIC32MX__)
        if (ReadByte( disk->buffer, BSI_FSTYPE ) == 'F' && \
            ReadByte( disk->buffer, BSI_FSTYPE + 1 ) == 'A' && \
            ReadByte( disk->buffer, BSI_FSTYPE + 2 ) == 'T' && \
            ReadByte( disk->buffer, BSI_FSTYPE + 3 ) == '1' && \
            ReadByte( disk->buffer, BSI_BOOTSIG) == 0x29)
#else
        if (BSec->FAT.FAT_16.BootSec_FSType[0] == 'F' && \
            BSec->FAT.FAT_16.BootSec_FSType[1] == 'A' && \
            BSec->FAT.FAT_16.BootSec_FSType[2] == 'T' && \
            BSec->FAT.FAT_16.BootSec_FSType[3] == '1' && \
            BSec->FAT.FAT_16.BootSec_BootSig == 0x29)
#endif
        {
            /* Mark that we do not have a MBR; 
                this is not actualy used - is here only to remove a compilation warning */
            masterBootRecord = (PT_MBR) NULL;
            switch (mode)
            {
                case 1:
                    // not enough info to construct our own boot sector
                    FSerrno = CE_INVALID_ARGUMENT;
                    return EOF;
                case 0:
                    // We have to determine the operating system, and the
                    // locations and sizes of the root dir and FAT, and the
                    // count of FATs
                    disk->firsts = 0;
                    if (LoadBootSector (disk) != CE_GOOD)
                    {
                        FSerrno = CE_BADCACHEREAD;
                        return EOF;
                    }
                default:
                    break;
            }
        }
        else
        {
            masterBootRecord = (PT_MBR) &gDataBuffer;
            disk->firsts = masterBootRecord->Partition0.PTE_FrstSect;
        }
    }
    else
    {
        /* If the signature is not correct, this is neither a MBR, nor a VBR */
        FSerrno = CE_BAD_PARTITION;
        return EOF;
    }

    switch (mode)
    {
        // True: Rewrite the whole boot sector
        case 1:
            secCount = masterBootRecord->Partition0.PTE_NumSect;

            if (secCount < 0x1039)
            {
                disk->type = FAT12;
                // Format to FAT12 only if there are too few sectors to format
                // as FAT16
                masterBootRecord->Partition0.PTE_FSDesc = 0x01;
                if (MDD_SectorWrite (0x00, gDataBuffer, TRUE) == FALSE)
                {
                    FSerrno = CE_WRITE_ERROR;
                    return EOF;
                }

                if (secCount >= 0x1028)
                {
                    // More than 0x18 sectors for FATs, 0x20 for root dir,
                    // 0x8 reserved, and 0xFED for data
                    // So double the number of sectors in a cluster to reduce
                    // the number of data clusters used
                    disk->SecPerClus = 2;
                }
                else
                {
                    // One sector per cluster
                    disk->SecPerClus = 1;
                }

                // Prepare a boot sector
                memset (gDataBuffer, 0x00, MEDIA_SECTOR_SIZE);

                // Last digit of file system name (FAT12   )
                gDataBuffer[58] = '2';

                // Calculate the size of the FAT
                fatsize = (secCount - 0x21  + (2*disk->SecPerClus));
                test =   (341 * disk->SecPerClus) + 2;
                fatsize = (fatsize + (test-1)) / test;
    
                disk->fatcopy = 0x02;
                disk->maxroot = 0x200;
    
                disk->fatsize = fatsize;

            }
            else if (secCount <= 0x3FFD5F)
            {
                disk->type = FAT16;
                // Format to FAT16
                masterBootRecord->Partition0.PTE_FSDesc = 0x06;
                if (MDD_SectorWrite (0x00, gDataBuffer, TRUE) == FALSE)
                {
                    FSerrno = CE_WRITE_ERROR;
                    return EOF;
                }

                DataClusters = secCount - 0x218;
                // Figure out how many sectors per cluster we need
                disk->SecPerClus = 1;
                while (DataClusters > 0xFFED)
                {
                    disk->SecPerClus *= 2;
                    DataClusters /= 2;
                }
                // This shouldnt happen
                if (disk->SecPerClus > 128)
                {
                    FSerrno = CE_BAD_PARTITION;
                    return EOF;
                }

                // Prepare a boot sector
                memset (gDataBuffer, 0x00, MEDIA_SECTOR_SIZE);

                // Last digit of file system name (FAT16   )
                gDataBuffer[58] = '6';

                // Calculate the size of the FAT
                fatsize = (secCount - 0x21  + (2*disk->SecPerClus));
                test =    (256  * disk->SecPerClus) + 2;
                fatsize = (fatsize + (test-1)) / test;
    
                disk->fatcopy = 0x02;
                disk->maxroot = 0x200;
    
                disk->fatsize = fatsize;
            }
            else
            {
                disk->type = FAT32;
                // Format to FAT32
                masterBootRecord->Partition0.PTE_FSDesc = 0x0B;
                if (MDD_SectorWrite (0x00, gDataBuffer, TRUE) == FALSE)
                {
                    FSerrno = CE_WRITE_ERROR;
                    return EOF;
                }

                #ifdef FORMAT_SECTORS_PER_CLUSTER
                    disk->SecPerClus = FORMAT_SECTORS_PER_CLUSTER;
                    DataClusters = secCount / disk->SecPerClus;

                    /* FAT32: 65526 < Number of clusters < 4177918 */
                    if ((DataClusters <= 65526) || (DataClusters >= 4177918))
                    {
                        FSerrno = CE_BAD_PARTITION;
                        return EOF;
                    }
                #else               
                    /*  FAT32: 65526 < Number of clusters < 4177918 */
                    DataClusters = secCount;
                    // Figure out how many sectors per cluster we need
                    disk->SecPerClus = 1;
                    while (DataClusters > 0x3FBFFE)
                    {
                        disk->SecPerClus *= 2;
                        DataClusters /= 2;
                    }
                #endif
                // Check the cluster size: FAT32 supports 512, 1024, 2048, 4096, 8192, 16K, 32K, 64K
                if (disk->SecPerClus > 128)
                {
                    FSerrno = CE_BAD_PARTITION;
                    return EOF;
                }

                // Prepare a boot sector
                memset (gDataBuffer, 0x00, MEDIA_SECTOR_SIZE);

               // Calculate the size of the FAT
                fatsize = (secCount - 0x20);
                test =    (128  * disk->SecPerClus) + 1;
                fatsize = (fatsize + (test-1)) / test;
    
                disk->fatcopy = 0x02;
                disk->maxroot = 0x200;
    
                disk->fatsize = fatsize;
            }

            // Non-file system specific values
            gDataBuffer[0] = 0xEB;         //Jump instruction
            gDataBuffer[1] = 0x3C;
            gDataBuffer[2] = 0x90;
            gDataBuffer[3] =  'M';         //OEM Name "MCHP FAT"
            gDataBuffer[4] =  'C';
            gDataBuffer[5] =  'H';
            gDataBuffer[6] =  'P';
            gDataBuffer[7] =  ' ';
            gDataBuffer[8] =  'F';
            gDataBuffer[9] =  'A';
            gDataBuffer[10] = 'T';

            gDataBuffer[11] = 0x00;             //Sector size 
            gDataBuffer[12] = 0x02;

            gDataBuffer[13] = disk->SecPerClus;   //Sectors per cluster

            if (disk->type == FAT12 || disk->type == FAT16)
            {
                gDataBuffer[14] = 0x08;         //Reserved sector count
                gDataBuffer[15] = 0x00;
                disk->fat = 0x08 + disk->firsts;

                gDataBuffer[16] = 0x02;         //number of FATs

                gDataBuffer[17] = 0x00;          //Max number of root directory entries - 512 files allowed
                gDataBuffer[18] = 0x02;

                gDataBuffer[19] = 0x00;         //total sectors
                gDataBuffer[20] = 0x00;

                gDataBuffer[21] = 0xF8;         //Media Descriptor

                gDataBuffer[22] = fatsize & 0xFF;         //Sectors per FAT
                gDataBuffer[23] = (fatsize >> 8) & 0xFF;

                gDataBuffer[24] = 0x3F;           //Sectors per track
                gDataBuffer[25] = 0x00;
    
                gDataBuffer[26] = 0xFF;         //Number of heads
                gDataBuffer[27] = 0x00;
    
                // Hidden sectors = sectors between the MBR and the boot sector
                gDataBuffer[28] = (BYTE)(disk->firsts & 0xFF);
                gDataBuffer[29] = (BYTE)((disk->firsts / 0x100) & 0xFF);
                gDataBuffer[30] = (BYTE)((disk->firsts / 0x10000) & 0xFF);
                gDataBuffer[31] = (BYTE)((disk->firsts / 0x1000000) & 0xFF);
    
                // Total Sectors = same as sectors in the partition from MBR
                gDataBuffer[32] = (BYTE)(secCount & 0xFF);
                gDataBuffer[33] = (BYTE)((secCount / 0x100) & 0xFF);
                gDataBuffer[34] = (BYTE)((secCount / 0x10000) & 0xFF);
                gDataBuffer[35] = (BYTE)((secCount / 0x1000000) & 0xFF);

                gDataBuffer[36] = 0x00;         // Physical drive number

                gDataBuffer[37] = 0x00;         // Reserved (current head)

                gDataBuffer[38] = 0x29;         // Signature code

                gDataBuffer[39] = (BYTE)(serialNumber & 0xFF);
                gDataBuffer[40] = (BYTE)((serialNumber / 0x100) & 0xFF);
                gDataBuffer[41] = (BYTE)((serialNumber / 0x10000) & 0xFF);
                gDataBuffer[42] = (BYTE)((serialNumber / 0x1000000) & 0xFF);

                // Volume ID
                if (volumeID != NULL)
                {
                    for (Index = 0; (*(volumeID + Index) != 0) && (Index < 11); Index++)
                    {
                        gDataBuffer[Index + 43] = *(volumeID + Index);
                    }
                    while (Index < 11)
                    {
                        gDataBuffer[43 + Index++] = 0x20;
                    }
                }
                else
                {
                    for (Index = 0; Index < 11; Index++)
                    {
                        gDataBuffer[Index+43] = 0;
                    }
                }

                gDataBuffer[54] = 'F';
                gDataBuffer[55] = 'A';
                gDataBuffer[56] = 'T';
                gDataBuffer[57] = '1';
                gDataBuffer[59] = ' ';
                gDataBuffer[60] = ' ';
                gDataBuffer[61] = ' ';

            }
            else //FAT32
            {
                gDataBuffer[14] = 0x20;         //Reserved sector count
                gDataBuffer[15] = 0x00;
                disk->fat = 0x20 + disk->firsts;

                gDataBuffer[16] = 0x02;         //number of FATs

                gDataBuffer[17] = 0x00;          //Max number of root directory entries - 512 files allowed
                gDataBuffer[18] = 0x00;

                gDataBuffer[19] = 0x00;         //total sectors
                gDataBuffer[20] = 0x00;

                gDataBuffer[21] = 0xF8;         //Media Descriptor

                gDataBuffer[22] = 0x00;         //Sectors per FAT
                gDataBuffer[23] = 0x00;

                gDataBuffer[24] = 0x3F;         //Sectors per track
                gDataBuffer[25] = 0x00;
    
                gDataBuffer[26] = 0xFF;         //Number of heads
                gDataBuffer[27] = 0x00;
    
                // Hidden sectors = sectors between the MBR and the boot sector
                gDataBuffer[28] = (BYTE)(disk->firsts & 0xFF);
                gDataBuffer[29] = (BYTE)((disk->firsts / 0x100) & 0xFF);
                gDataBuffer[30] = (BYTE)((disk->firsts / 0x10000) & 0xFF);
                gDataBuffer[31] = (BYTE)((disk->firsts / 0x1000000) & 0xFF);
    
                // Total Sectors = same as sectors in the partition from MBR
                gDataBuffer[32] = (BYTE)(secCount & 0xFF);
                gDataBuffer[33] = (BYTE)((secCount / 0x100) & 0xFF);
                gDataBuffer[34] = (BYTE)((secCount / 0x10000) & 0xFF);
                gDataBuffer[35] = (BYTE)((secCount / 0x1000000) & 0xFF);

                gDataBuffer[36] = fatsize & 0xFF;         //Sectors per FAT
                gDataBuffer[37] = (fatsize >>  8) & 0xFF;
                gDataBuffer[38] = (fatsize >> 16) & 0xFF;         
                gDataBuffer[39] = (fatsize >> 24) & 0xFF;

                gDataBuffer[40] = 0x00;         //Active FAT
                gDataBuffer[41] = 0x00;

                gDataBuffer[42] = 0x00;         //File System version  
                gDataBuffer[43] = 0x00;

                gDataBuffer[44] = 0x02;         //First cluster of the root directory
                gDataBuffer[45] = 0x00;
                gDataBuffer[46] = 0x00;
                gDataBuffer[47] = 0x00;

                gDataBuffer[48] = 0x01;         //FSInfo
                gDataBuffer[49] = 0x00;

                gDataBuffer[50] = 0x00;         //Backup Boot Sector
                gDataBuffer[51] = 0x00;

                gDataBuffer[52] = 0x00;         //Reserved for future expansion
                gDataBuffer[53] = 0x00;
                gDataBuffer[54] = 0x00;                   
                gDataBuffer[55] = 0x00;
                gDataBuffer[56] = 0x00;                   
                gDataBuffer[57] = 0x00;
                gDataBuffer[58] = 0x00;                   
                gDataBuffer[59] = 0x00;
                gDataBuffer[60] = 0x00;                   
                gDataBuffer[61] = 0x00;
                gDataBuffer[62] = 0x00;                   
                gDataBuffer[63] = 0x00;

                gDataBuffer[64] = 0x00;         // Physical drive number

                gDataBuffer[65] = 0x00;         // Reserved (current head)

                gDataBuffer[66] = 0x29;         // Signature code

                gDataBuffer[67] = (BYTE)(serialNumber & 0xFF);
                gDataBuffer[68] = (BYTE)((serialNumber / 0x100) & 0xFF);
                gDataBuffer[69] = (BYTE)((serialNumber / 0x10000) & 0xFF);
                gDataBuffer[70] = (BYTE)((serialNumber / 0x1000000) & 0xFF);

                // Volume ID
                if (volumeID != NULL)
                {
                    for (Index = 0; (*(volumeID + Index) != 0) && (Index < 11); Index++)
                    {
                        gDataBuffer[Index + 71] = *(volumeID + Index);
                    }
                    while (Index < 11)
                    {
                        gDataBuffer[71 + Index++] = 0x20;
                    }
                }
                else
                {
                    for (Index = 0; Index < 11; Index++)
                    {
                        gDataBuffer[Index+71] = 0;
                    }
                }

                gDataBuffer[82] = 'F';
                gDataBuffer[83] = 'A';
                gDataBuffer[84] = 'T';
                gDataBuffer[85] = '3';
                gDataBuffer[86] = '2';
                gDataBuffer[87] = ' ';
                gDataBuffer[88] = ' ';
                gDataBuffer[89] = ' ';


            }

#ifdef __18CXX
            // C18 can't reference a value greater than 256
            // using an array name pointer
            *(dataBufferPointer + 510) = 0x55;
            *(dataBufferPointer + 511) = 0xAA;
#else
            gDataBuffer[510] = 0x55;
            gDataBuffer[511] = 0xAA;
#endif

            disk->root = disk->fat + (disk->fatcopy * disk->fatsize);

            if (MDD_SectorWrite (disk->firsts, gDataBuffer, FALSE) == FALSE)
            {
                FSerrno = CE_WRITE_ERROR;
                return EOF;
            }

            break;
        case 0:
            if (LoadBootSector (disk) != CE_GOOD)
            {
                FSerrno = CE_BADCACHEREAD;
                return EOF;
            }
            break;
        default:
            FSerrno = CE_INVALID_ARGUMENT;
            return EOF;
    }

    // Erase the FAT
    memset (gDataBuffer, 0x00, MEDIA_SECTOR_SIZE);

    if (disk->type == FAT32)
    {
        gDataBuffer[0] = 0xF8;          //BPB_Media byte value in its low 8 bits, and all other bits are set to 1
        gDataBuffer[1] = 0xFF;
        gDataBuffer[2] = 0xFF;
        gDataBuffer[3] = 0xFF;

        gDataBuffer[4] = 0x00;          //Disk is clean and no read/write errors were encountered
        gDataBuffer[5] = 0x00;
        gDataBuffer[6] = 0x00;
        gDataBuffer[7] = 0x0C;

        gDataBuffer[8]  = 0xFF;         //Root Directory EOF  
        gDataBuffer[9]  = 0xFF;
        gDataBuffer[10] = 0xFF;
        gDataBuffer[11] = 0xFF;

        for (j = disk->fatcopy - 1; j != 0xFFFF; j--)
        {
            if (MDD_SectorWrite (disk->fat + (j * disk->fatsize), gDataBuffer, FALSE) == FALSE)
                return EOF;
        }
    
        memset (gDataBuffer, 0x00, 12);
    
        for (Index = disk->fat + 1; Index < (disk->fat + disk->fatsize); Index++)
        {
            for (j = disk->fatcopy - 1; j != 0xFFFF; j--)
            {
                if (MDD_SectorWrite (Index + (j * disk->fatsize), gDataBuffer, FALSE) == FALSE)
                    return EOF;
            }
        }
    
        // Erase the root directory
        for (Index = 1; Index < disk->SecPerClus; Index++)
        {
            if (MDD_SectorWrite (disk->root + Index, gDataBuffer, FALSE) == FALSE)
                return EOF;
        }
    
        if (volumeID != NULL)
        {
            // Create a drive name entry in the root dir
            Index = 0;
            while ((*(volumeID + Index) != 0) && (Index < 11))
            {
                gDataBuffer[Index] = *(volumeID + Index);
                Index++;
            }
            while (Index < 11)
            {
                gDataBuffer[Index++] = ' ';
            }
            gDataBuffer[11] = 0x08;
            gDataBuffer[17] = 0x11;
            gDataBuffer[19] = 0x11;
            gDataBuffer[23] = 0x11;
    
            if (MDD_SectorWrite (disk->root, gDataBuffer, FALSE) == FALSE)
                return EOF;
        }
        else
        {
            if (MDD_SectorWrite (disk->root, gDataBuffer, FALSE) == FALSE)
                return EOF;
        }
    
        return 0;
    }
    else
    {
        gDataBuffer[0] = 0xF8;
        gDataBuffer[1] = 0xFF;
        gDataBuffer[2] = 0xFF;
        if (disk->type == FAT16)
            gDataBuffer[3] = 0xFF;
    
        for (j = disk->fatcopy - 1; j != 0xFFFF; j--)
        {
            if (MDD_SectorWrite (disk->fat + (j * disk->fatsize), gDataBuffer, FALSE) == FALSE)
                return EOF;
        }
    
        memset (gDataBuffer, 0x00, 4);
    
        for (Index = disk->fat + 1; Index < (disk->fat + disk->fatsize); Index++)
        {
            for (j = disk->fatcopy - 1; j != 0xFFFF; j--)
            {
                if (MDD_SectorWrite (Index + (j * disk->fatsize), gDataBuffer, FALSE) == FALSE)
                    return EOF;
            }
        }
    
        // Erase the root directory
        RootDirSectors = ((disk->maxroot * 32) + (disk->sectorSize - 1)) / disk->sectorSize;
    
        for (Index = 1; Index < RootDirSectors; Index++)
        {
            if (MDD_SectorWrite (disk->root + Index, gDataBuffer, FALSE) == FALSE)
                return EOF;
        }
    
        if (volumeID != NULL)
        {
            // Create a drive name entry in the root dir
            Index = 0;
            while ((*(volumeID + Index) != 0) && (Index < 11))
            {
                gDataBuffer[Index] = *(volumeID + Index);
                Index++;
            }
            while (Index < 11)
            {
                gDataBuffer[Index++] = ' ';
            }
            gDataBuffer[11] = 0x08;
            gDataBuffer[17] = 0x11;
            gDataBuffer[19] = 0x11;
            gDataBuffer[23] = 0x11;
    
            if (MDD_SectorWrite (disk->root, gDataBuffer, FALSE) == FALSE)
                return EOF;
        }
        else
        {
            if (MDD_SectorWrite (disk->root, gDataBuffer, FALSE) == FALSE)
                return EOF;
        }
    
        return 0;
    }
}
#endif
#endif


/*******************************************************
  Function:
    BYTE Write_File_Entry( FILEOBJ fo, WORD * curEntry)
  Summary:
    Write dir entry info into a specified entry
  Conditions:
    This function should not be called by the user.
  Input:
    fo -        \File structure
    curEntry -  Write destination
  Return Values:
    TRUE - Operation successful
    FALSE - Operation failed
  Side Effects:
    None
  Description:
    This function will calculate the sector of the
    directory (whose base sector is pointed to by the
    dirccls value in the FSFILE object 'fo') that contains
    a directory entry whose offset is indicated by the
    curEntry parameter.  It will then write the data
    in the global data buffer (which should already
    contain the entries for that sector) to the device.
  Remarks:
    None
  *******************************************************/

#ifdef ALLOW_WRITES
BYTE Write_File_Entry( FILEOBJ fo, WORD * curEntry)
{
    DISK   *dsk;
    BYTE   status;
    BYTE   offset2;
    DWORD   sector;
    DWORD   ccls;

    dsk = fo->dsk;

    // get the cluster of this entry
    ccls = fo->dirccls;

     // figure out the offset from the base sector
    offset2  = (*curEntry / (dsk->sectorSize/32));

    /* Settings based on FAT type */
    switch (dsk->type)
    {
#ifdef SUPPORT_FAT32 // If FAT32 supported.
        case FAT32:
            // Root is always cluster-based in FAT32
            offset2 = offset2 % (dsk->SecPerClus);
            break;
#endif
        case FAT12:
        case FAT16:
            if(ccls != FatRootDirClusterValue)
                offset2 = offset2 % (dsk->SecPerClus);
            break;
    }

    sector = Cluster2Sector(dsk,ccls);

    // Now write it
    // "Offset" ensures writing of data belonging to a file entry only. Hence it doesn't change other file entries.
    if ( !MDD_SectorWrite( sector + offset2, dsk->buffer, FALSE))
        status = FALSE;
    else
        status = TRUE;

    return(status);
} // Write_File_Entry
#endif


/**********************************************************
  Function:
    BYTE FAT_erase_cluster_chain (WORD cluster, DISK * dsk)
  Summary:
    Erase a chain of clusters
  Conditions:
    This function should not be called by the user.
  Input:
    cluster -  The cluster number
    dsk -      The disk structure
  Return Values:
    TRUE -  Operation successful
    FALSE - Operation failed
  Side Effects:
    None
  Description:
    This function will parse through a cluster chain
    starting with the cluster pointed to by 'cluster' and
    mark all of the FAT entries as empty until the end of
    the chain has been reached or an error occurs.
  Remarks:
    None
  **********************************************************/

#ifdef ALLOW_WRITES
BYTE FAT_erase_cluster_chain (DWORD cluster, DISK * dsk)
{
    DWORD     c,c2,ClusterFailValue;
    enum    _status {Good, Fail, Exit}status;

    status = Good;

    /* Settings based on FAT type */
    switch (dsk->type)
    {

#ifdef SUPPORT_FAT32 // If FAT32 supported.
        case FAT32:
            ClusterFailValue = CLUSTER_FAIL_FAT32;
            c2 =  LAST_CLUSTER_FAT32;
            break;
#endif
        case FAT12:
            ClusterFailValue = CLUSTER_FAIL_FAT16; // FAT16 value itself
            c2 =  LAST_CLUSTER_FAT12;
            break;
        case FAT16:
        default:
            ClusterFailValue = CLUSTER_FAIL_FAT16;
            c2 =  LAST_CLUSTER_FAT16;
            break;
    }

    // Make sure there is actually a cluster assigned
    if(cluster == 0 || cluster == 1)  // Cluster assigned can't be "0" and "1"
    {
        status = Exit;
    }
    else
    {
        while(status == Good)
        {
            // Get the FAT entry
            if((c = ReadFAT( dsk, cluster)) == ClusterFailValue)
                status = Fail;
            else
            {
                if(c == 0 || c == 1)  // Cluster assigned can't be "0" and "1"
                {
                    status = Exit;
                }
                else
                {
                    // compare against max value of a cluster in FATxx
                    // look for the last cluster in the chain
                    if ( c >= c2)
                        status = Exit;

                    // Now erase this FAT entry
                    if(WriteFAT(dsk, cluster, CLUSTER_EMPTY, FALSE) == ClusterFailValue)
                        status = Fail;

                    // now update what the current cluster is
                    cluster = c;
                }
            }
        }// while status
    }// cluster == 0

    WriteFAT (dsk, 0, 0, TRUE);

    if(status == Exit)
        return(TRUE);
    else
        return(FALSE);
} // Erase cluster
#endif

/**************************************************************************
  Function:
    DIRENTRY Cache_File_Entry( FILEOBJ fo, WORD * curEntry, BYTE ForceRead)
  Summary:
    Load a file entry
  Conditions:
    This function should not be called by the user.
  Input:
    fo -         File information
    curEntry -   Offset of the directory entry to load.
    ForceRead -  Forces loading of a new sector of the directory.
  Return:
    DIRENTRY - Pointer to the directory entry that was loaded.
  Side Effects:
    Any unwritten data in the data buffer will be written to the device.
  Description:
    Load the sector containing the file entry pointed to by 'curEntry'
    from the directory pointed to by the variables in 'fo.'
  Remarks:
    Any modification of this function is extremely likely to
    break something.
  **************************************************************************/

DIRENTRY Cache_File_Entry( FILEOBJ fo, WORD * curEntry, BYTE ForceRead)
{
    DIRENTRY dir;
    DISK *dsk;
    DWORD sector;
    DWORD cluster, LastClusterLimit;
    DWORD ccls;
    BYTE offset2;
    BYTE numofclus;

    dsk = fo->dsk;

    // get the base sector of this directory
    cluster = fo->dirclus;
    ccls = fo->dirccls;

     // figure out the offset from the base sector
    offset2  = (*curEntry / (dsk->sectorSize/32));

    offset2 = offset2; // emulator issue

    /* Settings based on FAT type */
    switch (dsk->type)
    {
#ifdef SUPPORT_FAT32 // If FAT32 supported.
        case FAT32:
            // the ROOT is always cluster based in FAT32
            /* In FAT32: There is no ROOT region. Root etries are made in DATA region only.
            Every cluster of DATA which is accupied by ROOT is tracked by FAT table/entry so the ROOT can grow
            to an amount which is restricted only by available free DATA region. */
            offset2  = offset2 % (dsk->SecPerClus);   // figure out the offset
            LastClusterLimit = LAST_CLUSTER_FAT32;
            break;
#endif
        case FAT12:
        case FAT16:
        default:
            // if its the root its not cluster based
            if(cluster != 0)
                offset2  = offset2 % (dsk->SecPerClus);   // figure out the offset
            LastClusterLimit = LAST_CLUSTER_FAT16;
            break;
    }

    // check if a new sector of the root must be loaded
    if (ForceRead || (*curEntry & MASK_MAX_FILE_ENTRY_LIMIT_BITS) == 0)     // only 16 entries per sector
    {
        // see if we have to load a new cluster
        if((offset2 == 0 && (*curEntry) >= DIRENTRIES_PER_SECTOR) || ForceRead)
        {
            if(cluster == 0)
            {
                ccls = 0;
            }
            else
            {
                // If ForceRead, read the number of sectors from 0
                if(ForceRead)
                    numofclus = ((WORD)(*curEntry) / (WORD)(((WORD)DIRENTRIES_PER_SECTOR) * (WORD)dsk->SecPerClus));
                // Otherwise just read the next sector
                else
                    numofclus = 1;

                // move to the correct cluster
                while(numofclus)
                {
                    ccls = ReadFAT(dsk, ccls);

                    if(ccls >= LastClusterLimit)
                        break;
                    else
                        numofclus--;
                }
            }
        }

        // see if that we have a valid cluster number
        if(ccls < LastClusterLimit)
        {
            fo->dirccls = ccls; // write it back

            sector = Cluster2Sector(dsk,ccls);

            /* see if we are root and about to go pass our boundaries
            FAT32 stores the root directory in the Data Region along with files and other directories,
            allowing it to grow without such a restraint */
            if((ccls == FatRootDirClusterValue) && ((sector + offset2) >= dsk->data) && (FAT32 != dsk->type))
            {
                dir = ((DIRENTRY)NULL);   // reached the end of the root
            }
            else
            {
#ifdef ALLOW_WRITES
                if (gNeedDataWrite)
                    if (flushData())
                        return NULL;
#endif
                gBufferOwner = NULL;
                gBufferZeroed = FALSE;

                if ( MDD_SectorRead( sector + offset2, dsk->buffer) != TRUE) // if FALSE: sector could not be read.
                {
                    dir = ((DIRENTRY)NULL);
                }
                else // Sector has been read properly, Copy the root entry info of the file searched.
                {
                    if(ForceRead)    // Buffer holds all 16 root entry info. Point to the one required.
                        dir = (DIRENTRY)((DIRENTRY)dsk->buffer) + ((*curEntry)%DIRENTRIES_PER_SECTOR);
                    else
                        dir = (DIRENTRY)dsk->buffer;
                }
                gLastDataSectorRead = 0xFFFFFFFF;
            }
        }
        else
        {
            nextClusterIsLast = TRUE;
            dir = ((DIRENTRY)NULL);
        }
    }
    else
        dir = (DIRENTRY)((DIRENTRY)dsk->buffer) + ((*curEntry)%DIRENTRIES_PER_SECTOR);

    return(dir);
} // Cache_File_Entry


/*************************************************************************
  Function:
    CETYPE CreateFileEntry(FILEOBJ fo, WORD *fHandle)
  Summary:
    Create a new file entry
  Conditions:
    Should not be called by the user.
  Input:
    fo -       Pointer to file structure
    fHandle -  Location to create file
  Return Values:
    CE_GOOD -        File Creation successful
    CE_DIR_FULL -    All root directory entries are taken
    CE_WRITE_ERROR - The head cluster of the file could not be created.
  Side Effects:
    Modifies the FSerrno variable.
  Description:
    With the data passed within fo, create a new file entry in the current
    directory.  This function will first search for empty file entries.
    Once an empty entry is found, the entry will be populated with data
    for a file or directory entry.  Finally, the first cluster of the
    new file will be located and allocated, and its value will be
    written into the file entry.
  Remarks:
    None
  *************************************************************************/

#ifdef ALLOW_WRITES
CETYPE CreateFileEntry(FILEOBJ fo, WORD *fHandle, BYTE mode)
{
    BYTE    index;
    CETYPE  error = CE_GOOD;
    char    name[11];

    FSerrno = CE_GOOD;

    for (index = 0; index < FILE_NAME_SIZE; index ++)
    {
        name[index] = fo->name[index];
    }

    *fHandle = 0;

    // figure out where to put this file in the directory stucture
    if(FindEmptyEntries(fo, fHandle))
    {
        // found the entry, now populate it
        if((error = PopulateEntries(fo, name ,fHandle, mode)) == CE_GOOD)
        {
            // if everything is ok, create a first cluster
            error = CreateFirstCluster(fo);
        }
    }
    else
    {
        error = CE_DIR_FULL;
    }

    FSerrno = error;

    return(error);
}
#endif

/******************************************************
  Function:
    CETYPE CreateFirstCluster(FILEOBJ fo)
  Summary:
    Create the first cluster for a file
  Conditions:
    This function should not be called by the user.
  Input:
    fo -  The file that contains the first cluster
  Return Values:
    CE_GOOD -        First cluster created successfully
    CE_WRITE_ERROR - Cluster creation failed
  Side Effects:
    None
  Description:
    This function will find an unused cluster, link it to
    a file's directory entry, and write the entry back
    to the device.
  Remarks:
    None.
  ******************************************************/

#ifdef ALLOW_WRITES
CETYPE CreateFirstCluster(FILEOBJ fo)
{
    CETYPE       error;
    DWORD      cluster,TempMsbCluster;
    WORD        fHandle;
    DIRENTRY   dir;
    fHandle = fo->entry;

    // Now create the first cluster (head cluster)
    if((error = FILECreateHeadCluster(fo,&cluster)) == CE_GOOD)
    {
        // load the file entry so the new cluster can be linked to it
        dir = LoadDirAttrib(fo, &fHandle);

        // Now update the new cluster
        dir->DIR_FstClusLO = (cluster & 0x0000FFFF);


#ifdef SUPPORT_FAT32 // If FAT32 supported.
        // Get the higher part of cluster and store it in directory entry.
       TempMsbCluster = (cluster & 0x0FFF0000);    // Since only 28 bits usedin FAT32. Mask the higher MSB nibble.
       TempMsbCluster = TempMsbCluster >> 16;      // Get the date into Lsb place.
       dir->DIR_FstClusHI = TempMsbCluster;
#else // If FAT32 support not enabled
       TempMsbCluster = 0;                         // Just to avoid compiler warnigng.
       dir->DIR_FstClusHI = 0;
#endif

        // now write it
        if(Write_File_Entry(fo, &fHandle) != TRUE)
            error = CE_WRITE_ERROR;
    } // Create Cluster

    return(error);
}// End of CreateFirstCluster
#endif

/**********************************************************
  Function:
    BYTE FindEmptyEntries(FILEOBJ fo, WORD *fHandle)
  Summary:
    Find an empty dir entry
  Conditions:
    This function should not be called by the user.
  Input:
    fo -       Pointer to file structure
    fHandle -  Start of entries
  Return Values:
    TRUE - One found
    FALSE - None found
  Side Effects:
    None
  Description:
    This function will cache directory entries, starting
    with the one pointed to by the fHandle argument.  It will
    then search through the entries until an unused one
    is found.  If the end of the cluster chain for the
    directory is reached, a new cluster will be allocated
    to the directory (unless it's a FAT12 or FAT16 root)
    and the first entry of the new cluster will be used.
  Remarks:
    None.
  **********************************************************/

#ifdef ALLOW_WRITES
BYTE FindEmptyEntries(FILEOBJ fo, WORD *fHandle)
{
    BYTE   status = NOT_FOUND;
    BYTE   amountfound;
    BYTE   a;
    WORD   bHandle;
    DWORD b;
    DIRENTRY    dir;

    fo->dirccls = fo->dirclus;
    if((dir = Cache_File_Entry( fo, fHandle, TRUE)) == NULL)
    {
        status = CE_BADCACHEREAD;
    }
    else
    {
        // while its still not found
        while(status == NOT_FOUND)
        {
            amountfound = 0;
            bHandle = *fHandle;

            // find (number) continuous entries
            do
            {
                // Get the entry
                dir = Cache_File_Entry( fo, fHandle, FALSE);

                // Read the first char of the file name
                if(dir != NULL) // Last entry of the cluster
                {
                    a = dir->DIR_Name[0];
                }
                // increase number
                (*fHandle)++;
            }while((a == DIR_DEL || a == DIR_EMPTY) && (dir != (DIRENTRY)NULL) &&  (++amountfound < 1));

            // --- now why did we exit?
            if(dir == NULL) // Last entry of the cluster
            {
                //setup the current cluster
                b = fo->dirccls; // write it back

                // make sure we are not the root directory
                if(b == FatRootDirClusterValue)
                {
                    if (fo->dsk->type != FAT32)
                        status = NO_MORE;
                    else
                    {
                        fo->ccls = b;

                        if(FILEallocate_new_cluster(fo, 1) == CE_DISK_FULL)
                            status = NO_MORE;
                        else
                        {
                            *fHandle = bHandle;
                            status = FOUND;     // a new cluster will surely hold a new file name
                        }
                    }
                }
                else
                {
                    fo->ccls = b;

                    if(FILEallocate_new_cluster(fo, 1) == CE_DISK_FULL)
                        status = NO_MORE;
                    else
                    {
                        *fHandle = bHandle;
                        status = FOUND;     // a new cluster will surely hold a new file name
                    }
                }
            }
            else
            {
                if(amountfound == 1)
                {
                    status = FOUND;
                    *fHandle = bHandle;
                }
            }
        }// while

        // copy the base handle over
        *fHandle = bHandle;
    }

    if(status == FOUND)
        return(TRUE);
    else
        return(FALSE);
}
#endif

/**************************************************************************
  Function:
    BYTE PopulateEntries(FILEOBJ fo, char *name , WORD *fHandle)
  Summary:
    Populate a dir entry with data
  Conditions:
    Should not be called by the user.
  Input:
    fo -      Pointer to file structure
    name -    Name of the file
    fHandle - Location of the file
  Return Values:
    CE_GOOD - Population successful
  Side Effects:
    None
  Description:
    This function will write data into a new file entry.  It will also
    load timestamp data (based on the method selected by the user) and
    update the timestamp variables.
  Remarks:
    None.
  **************************************************************************/

#ifdef ALLOW_WRITES
BYTE PopulateEntries(FILEOBJ fo, char *name , WORD *fHandle, BYTE mode)
{
    BYTE error = CE_GOOD;
    DIRENTRY    dir;

    fo->dirccls = fo->dirclus;
    dir = Cache_File_Entry( fo, fHandle, TRUE);

    if (dir == NULL)
        return CE_BADCACHEREAD;

    // copy the contents over
    strncpy(dir->DIR_Name,name,DIR_NAMECOMP);

    // setup no attributes
    if (mode == DIRECTORY)
        dir->DIR_Attr = ATTR_DIRECTORY;
    else
        dir->DIR_Attr   = ATTR_ARCHIVE;

    dir->DIR_NTRes  = 0x00;              // nt reserved
    dir->DIR_FstClusHI =    0x0000;      // high word of this enty's first cluster number
    dir->DIR_FstClusLO =    0x0000;      // low word of this entry's first cluster number
    dir->DIR_FileSize =     0x0;         // file size in DWORD

   // Timing information for uncontrolled clock mode
#ifdef INCREMENTTIMESTAMP
    dir->DIR_CrtTimeTenth = 0xB2;        // millisecond stamp
    dir->DIR_CrtTime =      0x7278;      // time created
    dir->DIR_CrtDate =      0x32B0;      // date created
    dir->DIR_LstAccDate =   0x32B0;      // Last Access date
    dir->DIR_WrtTime =      0x7279;      // last update time
    dir->DIR_WrtDate =      0x32B0;      // last update date
#endif

#ifdef USEREALTIMECLOCK
    CacheTime();
    dir->DIR_CrtTimeTenth = gTimeCrtMS;        // millisecond stamp
    dir->DIR_CrtTime =      gTimeCrtTime;      // time created //
    dir->DIR_CrtDate =      gTimeCrtDate;      // date created (1/1/2004)
    dir->DIR_LstAccDate =   gTimeAccDate;      // Last Access date
    dir->DIR_WrtTime =      gTimeWrtTime;      // last update time
    dir->DIR_WrtDate =      gTimeWrtDate;      // last update date
#endif

#ifdef USERDEFINEDCLOCK
    // The user will have set the time before this funciton is called
    dir->DIR_CrtTimeTenth = gTimeCrtMS;
    dir->DIR_CrtTime =      gTimeCrtTime;
    dir->DIR_CrtDate =       gTimeCrtDate;
    dir->DIR_LstAccDate =   gTimeAccDate;
    dir->DIR_WrtTime =       gTimeWrtTime;
    dir->DIR_WrtDate =      gTimeWrtDate;
#endif

    fo->size        = dir->DIR_FileSize;
    fo->time        = dir->DIR_CrtTime;
    fo->date        = dir->DIR_CrtDate;
    fo->attributes  = dir->DIR_Attr;
    fo->entry       = *fHandle;

    // just write the last entry in
    if (Write_File_Entry(fo,fHandle) != TRUE)
        error = CE_WRITE_ERROR;

    return(error);
}

#ifdef USEREALTIMECLOCK

/*************************************************************************
  Function:
    void CacheTime (void)
  Summary:
    Automatically store timestamp information from the RTCC
  Conditions:
    RTCC module enabled.  Should not be called by the user.
  Return Values:
    None
  Side Effects:
    Modifies global timing variables
  Description:
    This function will automatically load information from an RTCC
    module and use it to update the global timing variables.  These can
    then be used to update file timestamps.
  Remarks:
    None.
  *************************************************************************/

void CacheTime (void)
{
    WORD    year, monthday, weekhour, minsec, c, result;
    BYTE    ptr1, ptr0;

#if defined (__PIC32MX__)   // Added support for PIC32. -Bud (3/4/2008)

	unsigned int	t0, t1;
	unsigned int	d0, d1;

	do  // Get the time
	{
		t0=RTCTIME;
		t1=RTCTIME;
	}while(t0!=t1);

	do  // Get the date
	{
		d0=RTCDATE;
		d1=RTCDATE;
	}while(d0!=d1);

    // Put them in place.
    year        = (WORD)(d0 >> 24);
    monthday    = (WORD)(d0 >> 8);
    weekhour    = (WORD)((d0 & 0x0F) << 8);
    weekhour   |= (WORD)(t0 >> 24);
    minsec      = (WORD)(t0 >> 8);

#else

    if(RCFGCALbits.RTCPTR0)
        ptr0 = 1;
    else
        ptr0 = 0;
    if (RCFGCALbits.RTCPTR1)
        ptr1 = 1;
    else
        ptr1 = 0;

    RCFGCALbits.RTCPTR0 = 1;
    RCFGCALbits.RTCPTR1 = 1;
    year = RTCVAL;
    monthday = RTCVAL;
    weekhour = RTCVAL;
    minsec = RTCVAL;

    if (ptr0 == 1)
        RCFGCALbits.RTCPTR0 = 1;

    if (ptr1 == 1)
        RCFGCALbits.RTCPTR1 = 1;

#endif

    c = 0;
    c += (year & 0x0F);
    c += ((year & 0xF0) >> 4) * 10;
    // c equals the last 2 digits of the year from 2000 to 2099
    // Add 20 to adjust it to FAT time (from 1980 to 2107)
    c += 20;
    // shift the result to bits
    result = c << 9;

    if ((monthday & 0x1000) == 0x1000)
    {
        c = 10;
    }
    else
    {
        c = 0;
    }
    c += ((monthday & 0x0F00) >> 8);
    c <<= 5;
    result |= c;

    c = (monthday & 0x00F0) >> 4;
    c *= 10;
    c += (monthday & 0x000F);

    result |= c;

    gTimeCrtDate = result;
    gTimeWrtDate = result;
    gTimeAccDate = result;

    c = ((weekhour & 0x00F0) >> 4) * 10;
    c += (weekhour & 0x000F);
    result = c << 11;
    c = ((minsec & 0xF000) >> 12) * 10;
    c += (minsec & 0x0F00) >> 8;
    result |= (c << 5);
    c = ((minsec & 0x00F0) >> 4) * 10;
    c += (minsec & 0x000F);

    // If seconds mod 2 is 1, add 1000 ms
    if (c % 2)
        gTimeCrtMS = 100;
    else
        gTimeCrtMS = 0;

    c >>= 1;
    result |= c;

    gTimeCrtTime = result;
    gTimeWrtTime = result;
}
#endif

#ifdef USERDEFINEDCLOCK

/***********************************************************************************************************
  Function:
    int SetClockVars (unsigned int year, unsigned char month, unsigned char day, unsigned char hour, unsigned char minute, unsigned char second)
  Summary:
    Manually set timestamp variables
  Conditions:
    USERDEFINEDCLOCK macro defined in FSconfig.h.
  Input:
    year -     The year (1980\-2107)
    month -   The month (1\-12)
    day -     The day of the month (1\-31)
    hour -    The hour (0\-23)
    minute -  The minute (0\-59)
    second -  The second (0\-59)
  Return Values:
    None
  Side Effects:
    Modifies global timing variables
  Description:
    Lets the user manually set the timing variables.  The values passed in will be converted to the format
    used by the FAT timestamps.
  Remarks:
    Call this before creating a file or directory (set create time) and
    before closing a file (set last access time, last modified time)
  ***********************************************************************************************************/

int SetClockVars (unsigned int year, unsigned char month, unsigned char day, unsigned char hour, unsigned char minute, unsigned char second)
{
    unsigned int result;

    if ((year < 1980) || (year > 2107) || (month < 1) || (month > 12) ||
        (day < 1) || (day > 31) || (hour > 23) || (minute > 59) || (second > 59))
    {
        FSerrno = CE_INVALID_ARGUMENT;
        return -1;
    }

    result = (year - 1980) << 9;
    result |= (unsigned int)((unsigned int)month << 5);
    result |= (day);

    gTimeAccDate = result;
    gTimeCrtDate = result;
    gTimeWrtDate = result;

    result = ((unsigned int)hour << 11);
    result |= (unsigned int)((unsigned int)minute << 5);
    result |= (second/2);

    gTimeCrtTime = result;
    gTimeWrtTime = result;

    if (second % 2)
        gTimeCrtMS = 100;
    else
        gTimeCrtMS = 0;

    FSerrno = CE_GOOD;
    return 0;
}
#endif

#endif

/***********************************************************************
  Function:
    BYTE FILEallocate_new_cluster( FILEOBJ fo, BYTE mode)
  Summary;
    Allocate a new cluster to a file
  Conditions:
    Should not be called by the user.
  Input:
    fo -    Pointer to file structure
    mode -
         - 0 - Allocate a cluster to a file
         - 1 - Allocate a cluster to a directory
  Return Values:
    CE_GOOD -      Cluster allocated
    CE_DISK_FULL - No clusters available
  Side Effects:
    None
  Description:
    This function will find an empty cluster on the device using the
    FATfindEmptyCluster function.  It will then mark it as the last
    cluster in the file in the FAT chain, and link the current last
    cluster of the passed file to the new cluster.  If the new
    cluster is a directory cluster, it will be erased (so there are no
    extraneous directory entries).  If it's allocated to a non-directory
    file, it doesn't need to be erased; extraneous data in the cluster
    will be unviewable because of the file size parameter.
  Remarks:
    None.
  ***********************************************************************/

#ifdef ALLOW_WRITES
BYTE FILEallocate_new_cluster( FILEOBJ fo, BYTE mode)
{
    DISK *      dsk;
    DWORD c,curcls;

    dsk = fo->dsk;
    c = fo->ccls;

    // find the next empty cluster
    c = FATfindEmptyCluster(fo);
    if (c == 0)      // "0" is just an indication as Disk full in the fn "FATfindEmptyCluster()"
        return CE_DISK_FULL;


    // mark the cluster as taken, and last in chain
    if(dsk->type == FAT12)
        WriteFAT( dsk, c, LAST_CLUSTER_FAT12, FALSE);
    else if (dsk->type == FAT16)
        WriteFAT( dsk, c, LAST_CLUSTER_FAT16, FALSE);

#ifdef SUPPORT_FAT32 // If FAT32 supported.
    else
        WriteFAT( dsk, c, LAST_CLUSTER_FAT32, FALSE);
#endif

    // link current cluster to the new one
    curcls = fo->ccls;

    WriteFAT( dsk, curcls, c, FALSE);

    // update the FILE structure
    fo->ccls = c;

    // IF this is a dir, we need to erase the cluster
    // If it's a file, we can leave it- the file size
    // will limit the data we see to the data that's been
    // written
    if (mode == 1)
        return (EraseCluster(dsk, c));
    else
        return CE_GOOD;

} // allocate new cluster
#endif

/***********************************************
  Function:
    DWORD FATfindEmptyCluster(FILEOBJ fo)
  Summary:
    Find the next available cluster on the device
  Conditions:
    This function should not be called by the
    user.
  Input:
    fo -  Pointer to file structure
  Return Values:
    DWORD - Address of empty cluster
    0 -     Could not find empty cluster
  Side Effects:
    None
  Description:
    This function will search through the FAT to
    find the next available cluster on the device.
  Remarks:
    Should not be called by user
  ***********************************************/

#ifdef ALLOW_WRITES
DWORD FATfindEmptyCluster(FILEOBJ fo)
{
    DISK *   disk;
    DWORD    value = 0x0;
    DWORD    c,curcls, EndClusterLimit, ClusterFailValue;

    disk = fo->dsk;
    c = fo->ccls;

    /* Settings based on FAT type */
    switch (disk->type)
    {
#ifdef SUPPORT_FAT32 // If FAT32 supported.
        case FAT32:
            EndClusterLimit = END_CLUSTER_FAT32;
            ClusterFailValue = CLUSTER_FAIL_FAT32;
            break;
#endif
        case FAT12:
            EndClusterLimit = END_CLUSTER_FAT12;
            ClusterFailValue = CLUSTER_FAIL_FAT16;
            break;
        case FAT16:
        default:
            EndClusterLimit = END_CLUSTER_FAT16;
            ClusterFailValue = CLUSTER_FAIL_FAT16;
            break;
    }

    // just in case
    if(c < 2)
        c = 2;

    curcls = c;
    ReadFAT(disk, c);

    // sequentially scan through the FAT looking for an empty cluster
    while(c)
    {
        // look at its value
        if ( (value = ReadFAT(disk, c)) == ClusterFailValue)
        {
            c = 0;
            break;
        }

        // check if empty cluster found
        if (value == CLUSTER_EMPTY)
            break;

        c++;    // check next cluster in FAT
        // check if reached last cluster in FAT, re-start from top
        if (value == EndClusterLimit || c >= (disk->maxcls+2))
            c = 2;

        // check if full circle done, disk full
        if ( c == curcls)
        {
            c = 0;
            break;
        }
    }  // scanning for an empty cluster

    return(c);
}
#endif


/*********************************************************************************
  Function:
    void FSGetDiskProperties(FS_DISK_PROPERTIES* properties)
  Summary:
    Allows user to get the disk properties (size of disk, free space, etc)
  Conditions:
    1) ALLOW_GET_DISK_PROPERTIES must be defined in FSconfig.h
    2) a FS_DISK_PROPERTIES object must be created before the function is called
    3) the new_request member of the FS_DISK_PROPERTIES object must be set before
        calling the function for the first time.  This will start a new search.
    4) this function should not be called while there is a file open.  Close all
        files before calling this function.
  Input:
    properties - a pointer to a FS_DISK_PROPERTIES object where the results should
      be stored.
  Return Values:
    This function returns void.  The properties_status of the previous call of this 
      function is located in the properties.status field.  This field has the 
      following possible values:

    FS_GET_PROPERTIES_NO_ERRORS - operation completed without error.  Results
      are in the properties object passed into the function.
    FS_GET_PROPERTIES_DISK_NOT_MOUNTED - there is no mounted disk.  Results in
      properties object is not valid
    FS_GET_PROPERTIES_CLUSTER_FAILURE - there was a failure trying to read a 
      cluster from the drive.  The results in the properties object is a partial
      result up until the point of the failure.
    FS_GET_PROPERTIES_STILL_WORKING - the search for free sectors is still in
      process.  Continue calling this function with the same properties pointer 
      until either the function completes or until the partial results meets the
      application needs.  The properties object contains the partial results of
      the search and can be used by the application.  
  Side Effects:
    Can cause errors if called when files are open.  Close all files before
    calling this function.

    Calling this function without setting the new_request member on the first
    call can result in undefined behavior and results.

    Calling this function after a result is returned other than
    FS_GET_PROPERTIES_STILL_WORKING can result in undefined behavior and results.
  Description:  
    This function returns the information about the mounted drive.  The results 
    member of the properties object passed into the function is populated with 
    the information about the drive.    

    Before starting a new request, the new_request member of the properties
    input parameter should be set to TRUE.  This will initiate a new search
    request.

    This function will return before the search is complete with partial results.
    All of the results except the free_clusters will be correct after the first
    call.  The free_clusters will contain the number of free clusters found up
    until that point, thus the free_clusters result will continue to grow until
    the entire drive is searched.  If an application only needs to know that a 
    certain number of bytes is available and doesn't need to know the total free 
    size, then this function can be called until the required free size is
    verified.  To continue a search, pass a pointer to the same FS_DISK_PROPERTIES
    object that was passed in to create the search.

    A new search request sould be made once this function has returned a value 
    other than FS_GET_PROPERTIES_STILL_WORKING.  Continuing a completed search
    can result in undefined behavior or results.

    Typical Usage:
    <code>
    FS_DISK_PROPERTIES disk_properties;

    disk_properties.new_request = TRUE;

    do
    {
        FSGetDiskProperties(&disk_properties);
    } while (disk_properties.properties_status == FS_GET_PROPERTIES_STILL_WORKING);
    </code>

    results.disk_format - contains the format of the drive.  Valid results are 
      FAT12(1), FAT16(2), or FAT32(3).

    results.sector_size - the sector size of the mounted drive.  Valid values are
      512, 1024, 2048, and 4096.

    results.sectors_per_cluster - the number sectors per cluster.

    results.total_clusters - the number of total clusters on the drive.  This 
      can be used to calculate the total disk size (total_clusters * 
      sectors_per_cluster * sector_size = total size of drive in bytes)

    results.free_clusters - the number of free (unallocated) clusters on the drive.
      This can be used to calculate the total free disk size (free_clusters * 
      sectors_per_cluster * sector_size = total size of drive in bytes)

  Remarks:
    PIC24F size estimates:
      Flash - 400 bytes (-Os setting)

    PIC24F speed estimates:
      Search takes approximately 7 seconds per Gigabyte of drive space.  Speed
        will vary based on the number of sectors per cluster and the sector size.
  *********************************************************************************/
#if defined(ALLOW_GET_DISK_PROPERTIES)
void FSGetDiskProperties(FS_DISK_PROPERTIES* properties)
{
    BYTE    i;
    DWORD   value = 0x0;

    if(properties->new_request == TRUE)
    {
        properties->disk = &gDiskData;
        properties->results.free_clusters = 0;
        properties->new_request = FALSE;

        if(properties->disk->mount != TRUE)
        {
            properties->properties_status = FS_GET_PROPERTIES_DISK_NOT_MOUNTED;
            return;
        }

        properties->properties_status = FS_GET_PROPERTIES_STILL_WORKING;
   
        properties->results.disk_format = properties->disk->type;
        properties->results.sector_size = properties->disk->sectorSize;
        properties->results.sectors_per_cluster = properties->disk->SecPerClus;
        properties->results.total_clusters = properties->disk->maxcls;

        /* Settings based on FAT type */
        switch (properties->disk->type)
        {
    #ifdef SUPPORT_FAT32 // If FAT32 supported.
            case FAT32:
                properties->private.EndClusterLimit = END_CLUSTER_FAT32;
                properties->private.ClusterFailValue = CLUSTER_FAIL_FAT32;
                break;
    #endif
            case FAT16:
                properties->private.EndClusterLimit = END_CLUSTER_FAT16;
                properties->private.ClusterFailValue = CLUSTER_FAIL_FAT16;
                break;
            case FAT12:
                properties->private.EndClusterLimit = END_CLUSTER_FAT12;
                properties->private.ClusterFailValue = CLUSTER_FAIL_FAT16;
                break;
        }
    
        properties->private.c = 2;

        properties->private.curcls = properties->private.c;
        ReadFAT(properties->disk, properties->private.c);
    }

    if(properties->disk == NULL)
    {
        properties->properties_status = FS_GET_PROPERTIES_DISK_NOT_MOUNTED;
        return;
    }

    if(properties->properties_status != FS_GET_PROPERTIES_STILL_WORKING)
    {
        return;
    }

    // sequentially scan through the FAT looking for an empty cluster
    for(i=0;i<255;i++)
    {
        // look at its value
        if ( (value = ReadFAT(properties->disk, properties->private.c)) == properties->private.ClusterFailValue)
        {
            properties->properties_status = FS_GET_PROPERTIES_CLUSTER_FAILURE;
            return;
        }

        // check if empty cluster found
        if (value == CLUSTER_EMPTY)
        {
            properties->results.free_clusters++;
        }

        properties->private.c++;    // check next cluster in FAT
        // check if reached last cluster in FAT, re-start from top
        if (value == properties->private.EndClusterLimit || properties->private.c >= (properties->results.total_clusters + 2))
            properties->private.c = 2;

        // check if full circle done, disk full
        if ( properties->private.c == properties->private.curcls)
        {
            properties->properties_status = FS_GET_PROPERTIES_NO_ERRORS;
            return;
        }
    }  // scanning for an empty cluster

    properties->properties_status = FS_GET_PROPERTIES_STILL_WORKING;
    return;
}
#endif

/************************************************************
  Function:
    int FSfclose(FSFILE *fo)
  Summary:
    Update file information and free FSFILE objects
  Conditions:
    File opened
  Input:
    fo -  Pointer to the file to close
  Return Values:
    0 -   File closed successfully
    EOF - Error closing the file
  Side Effects:
    The FSerrno variable will be changed.
  Description:
    This function will update the directory entry for the
    file pointed to by 'fo' with the information contained
    in 'fo,' including the new file size and attributes.
    Timestamp information will also be loaded based on the
    method selected by the user and written to the entry
    as the last modified time and date.  The file entry will
    then be written to the device.  Finally, the memory
    used for the specified file object will be freed from
    the dynamic heap or the array of FSFILE objects.
  Remarks:
    A function to flush data to the device without closing the
    file can be created by removing the portion of this
    function that frees the memory and the line that clears
    the write flag.
  ************************************************************/

int FSfclose(FSFILE   *fo)
{
    WORD        fHandle;
#ifndef FS_DYNAMIC_MEM
    WORD        fIndex;
#endif
    int        error = 72;
#ifdef ALLOW_WRITES
    DIRENTRY    dir;
#endif

    FSerrno = CE_GOOD;
    fHandle = fo->entry;
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
