linkejian123/Antique-Music-Box/MICRO/MAIN/AntiqueMusicBox.X/VFDdisplayMessage.c

/*
 * File:   VFDdisplayMessage.c
 * Author: ECE477 Team8 Antique Music Box
 * This file display the message on VFD for the Antique Music Box
 * Created on October 31, 2015, 12:00 AM
 */

#include <xc.h>
#include "p33Fxxxx.h"

void shiftout(int);
void delay(int);


void VFDdisplayMessage(char* message)
{
    int byteIndex = 0;
   
    PORTGbits.RG2 = 0;    // set blank as low
    while(*message != '\0')
    {
        byteIndex = *message - 0x20;
        shiftout(byteIndex);
        PORTFbits.RF4 = 1;
        PORTFbits.RF4 = 0;
        *message++;
        delay(100);
    }
}

void delay(int n)
{
    int i;
    int index;
    for(i=0;i<20000;i++)
    {
        for(index=0;index<n;index++);
    }
}

void shiftout(int data)
{
    long ascii[97][20]={
        {0,0,0,0,0,0,0,0,0,0,0,0,0,0,0,0,0,0,0,0}, //blank    
        {0,0,0,0,0,0,0,1,1,1,0,0,1,0,0,0,0,0,0,0}, //!
        {0,0,0,1,0,0,0,0,0,1,0,0,1,1,0,0,0,0,0,0}, // ?2?
        {0,1,0,0,1,0,0,0,0,0,0,1,0,1,0,1,0,1,0,0},// ?3?
        {0,0,1,0,1,0,1,1,0,0,1,1,0,1,0,1,1,1,0,0},// $
        {0,0,0,1,1,0,1,1,0,0,1,0,1,1,0,1,1,1,0,0},// %
        {0,1,1,0,0,1,1,0,0,0,0,0,0,1,1,1,1,0,0,0},  // ?6?
        {0,0,0,0,0,0,0,0,0,0,0,0,0,1,0,0,0,0,0,0},// ?7?
        {0,0,0,0,0,1,0,0,0,0,0,0,1,0,0,0,0,0,0,0},//  ?8?
        {0,0,0,1,0,0,0,0,0,0,0,0,0,0,1,0,0,0,0,0},//  ?9?
        {0,0,0,1,1,1,0,0,0,0,0,1,1,1,1,1,0,0,0,0},// *
        {0,0,0,0,1,0,0,0,0,0,0,1,0,1,0,1,0,0,0,0},// +
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
        {0,0,0,0,1,0,1,0,0,0,1,0,0,1,0,1,0,0,0,0},// {
        {0,1,0,0,0,0,0,0,0,0,0,0,0,0,0,0,0,1,0,0},// ?6c?
        {0,0,0,0,0,0,1,1,0,1,1,1,0,0,0,0,0,0,0,0},// }
        {0,0,0,0,0,0,0,0,0,0,0,0,1,0,1,0,0,0,0,0},// 6e
        {0,0,0,0,0,0,0,0,0,0,1,0,0,0,0,0,1,0,0,0}, //6f
       
        {1,1,1,1,1,1,1,1,1,1,1,1,1,1,1,1,1,1,1,1}//debug

    };

    int i;
    int var = 0;

    for (i=19; i>=0; i--)  {
        var = ascii[data][i];
        PORTAbits.RA2 = var;
        PORTAbits.RA1 = 0;
        PORTAbits.RA1 = 1;
        PORTAbits.RA2 = 0;

    }
}
