linkejian123/Antique-Music-Box/MICRO/MAIN/AntiqueMusicBox.X/VFDdisplayMessage.h

/* 
 * File:   VFDdisplayMessage.h
 * Author: EE63PC9-user
 *
 * Created on October 31, 2015, 2:59 PM
 */

#ifndef VFDDISPLAYMESSAGE_H
#define	VFDDISPLAYMESSAGE_H

#ifdef	__cplusplus
extern "C" {
#endif

extern void VFDdisplayMessage(char*);
extern void delay(int);

#ifdef	__cplusplus
}
#endif

#endif	/* VFDDISPLAYMESSAGE_H */
