linkejian123/Antique-Music-Box/MICRO/MAIN/AntiqueMusicBox.X/configuration_pins.h

/* 
 * File:   configuration_pins.h
 * Author: EE63PC9-user
 *
 * Created on October 31, 2015, 12:02 AM
 */

#ifndef CONFIGURATION_PINS_H
#define	CONFIGURATION_PINS_H

#ifdef	__cplusplus
extern "C" {
#endif

extern void Configure_Pins(void);



#ifdef	__cplusplus
}
#endif

#endif	/* CONFIGURATION_PINS_H */
