linkejian123/Antique-Music-Box/SD/SD.X/MP3Codec.h

/* 
 * File:   MP3Codec.h
 * Author: EE63PC9-user
 *
 * Created on November 5, 2015, 11:25 AM
 */

#ifndef MP3CODEC_H
#define	MP3CODEC_H

#ifdef	__cplusplus
extern "C" {
#endif

extern void MP3Codec(int);


#ifdef	__cplusplus
}
#endif

#endif	/* MP3CODEC_H */
