linkejian123/Antique-Music-Box/AntiqueMB.X/ADC.h

/**********************************************************************
* © 2005 Microchip Technology Inc.
*
* FileName:        ADC.h
* Dependencies:    Other (.h) files if applicable, see below
* Processor:       dsPIC33Fxxxx
* Compiler:        MPLAB® C30 v3.00 or higher
*
* SOFTWARE LICENSE AGREEMENT:
* Microchip Technology Incorporated ("Microchip") retains all ownership and 
* intellectual property rights in the code accompanying this message and in all 
* derivatives hereto.  You may use this code, and any derivatives created by 
* any person or entity by or on your behalf, exclusively with Microchip's
* proprietary products.  Your acceptance and/or use of this code constitutes 
* agreement to the terms and conditions of this notice.
*
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
* YOU ACKNOWLEDGE AND AGREE THAT, IN NO EVENT, SHALL MICROCHIP BE LIABLE, WHETHER 
* IN CONTRACT, WARRANTY, TORT (INCLUDING NEGLIGENCE OR BREACH OF STATUTORY DUTY), 
* STRICT LIABILITY, INDEMNITY, CONTRIBUTION, OR OTHERWISE, FOR ANY INDIRECT, SPECIAL, 
* PUNITIVE, EXEMPLARY, INCIDENTAL OR CONSEQUENTIAL LOSS, DAMAGE, FOR COST OR EXPENSE OF 
* ANY KIND WHATSOEVER RELATED TO THE CODE, HOWSOEVER CAUSED, EVEN IF MICROCHIP HAS BEEN 
* ADVISED OF THE POSSIBILITY OR THE DAMAGES ARE FORESEEABLE.  TO THE FULLEST EXTENT 
* ALLOWABLE BY LAW, MICROCHIP'S TOTAL LIABILITY ON ALL CLAIMS IN ANY WAY RELATED TO 
* THIS CODE, SHALL NOT EXCEED THE PRICE YOU PAID DIRECTLY TO MICROCHIP SPECIFICALLY TO 
* HAVE THIS CODE DEVELOPED.
*
* You agree that you are solely responsible for testing the code and 
* determining its suitability.  Microchip has no obligation to modify, test, 
* certify, or support the code.
*
* REVISION HISTORY:
*~~~~~~~~~~~~~~~~~~~~~~~~~~~~~~~~~~~~~~~~~~~~~~~~~~~~~~~~~~~~~~~~~~~~~~
* Author            Date      Comments on this revision
*~~~~~~~~~~~~~~~~~~~~~~~~~~~~~~~~~~~~~~~~~~~~~~~~~~~~~~~~~~~~~~~~~~~~~~
* Settu D 			03/09/06  First release of source file
*~~~~~~~~~~~~~~~~~~~~~~~~~~~~~~~~~~~~~~~~~~~~~~~~~~~~~~~~~~~~~~~~~~~~~~*
* ADDITIONAL NOTES:
*
**********************************************************************/
#ifndef __ADC_H__
#define __ADC_H__ 

// Sampling Control
#define Fosc		18000000
#define Fcy			(Fosc/2)
#define Fs   		8000
#define SAMPPRD    (Fcy/Fs)-1
#define NUMSAMP     256
// Define Message Buffer Length for ECAN1/ECAN2



// External Functions
extern void initAdc1(void);
extern void initTmr3();
extern void initDma0(void);
extern void __attribute__((__interrupt__)) _DMA0Interrupt(void);
void ProcessADCSamples(int * AdcBuffer);

#endif
